batchku/MO/openframeworks/MOD/bin/data/img_mask_720b.png

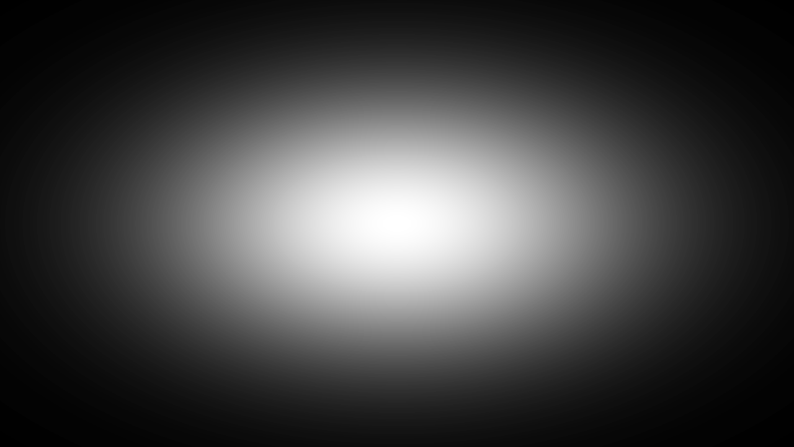
openframeworks/MOD/bin/data/img_mask_720b.png
