batchku/MO/openframeworks/MOD/bin/data/img_mask_720c.png

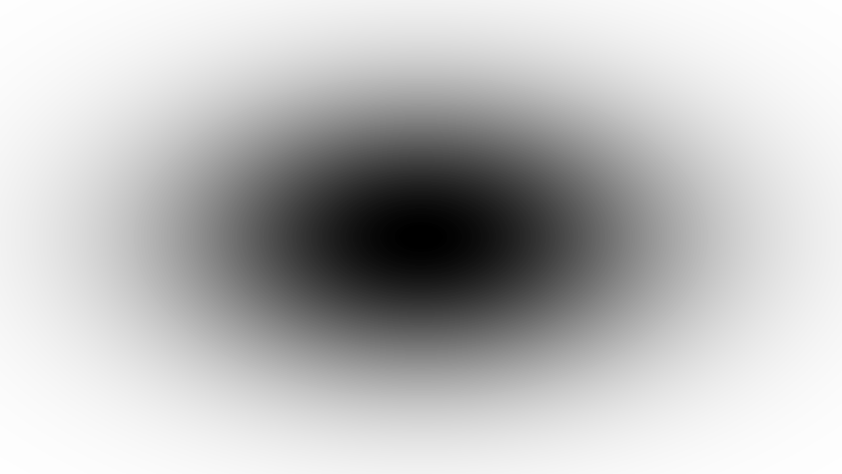
openframeworks/MOD/bin/data/img_mask_720c.png
