batchku/MO/CAD/MOD/_MOD-vr_rhino-exports/MOD-v1_MOD-lightbox-mids.dxf

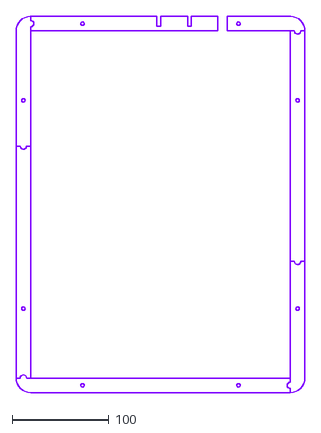
[picture p23: CAD file, 2017-08-02]
CAD/MOD/_MOD-vr_rhino-exports/MOD-v1_MOD-lightbox-mids.dxf
299.0 x 389.5
