batchku/MO/CAD/MOD/MOD-Button-Cap-Cap_v9-A.stl

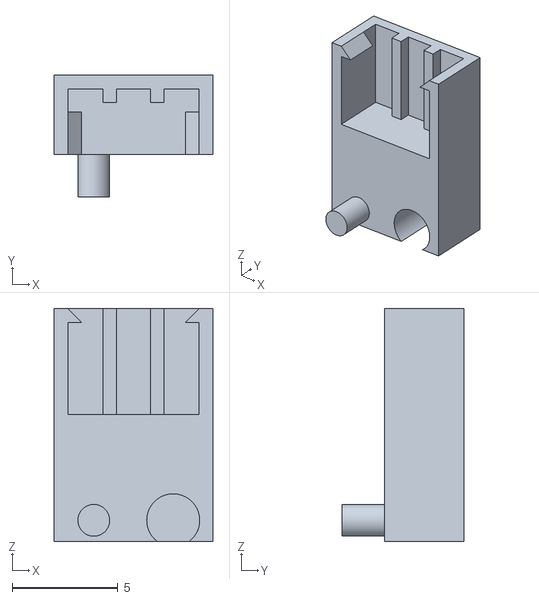
[picture p24: CAD file, 2017-09-18]
CAD/MOD/MOD-Button-Cap-Cap_v9-A.stl
7.50 x 5.75 x 11.0
