batchku/MO/CAD/MOM/_exports/MOMv2_bottom-plate.dxf

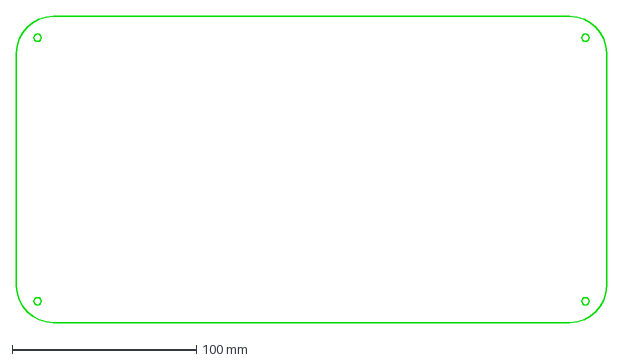
[picture p25: CAD file, 2017-09-16]
CAD/MOM/_exports/MOMv2_bottom-plate.dxf
320.0 x 166.0 mm
