batchku/MO/PCBs/MO/MO-v2-6b.dxf

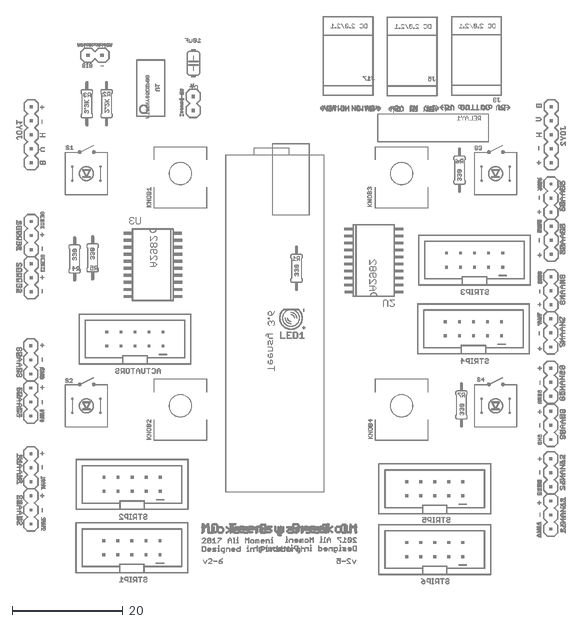
[picture p26: CAD file, 2017-12-16]
PCBs/MO/MO-v2-6b.dxf
99.4 x 102.7
