batchku/MO/PCBs/MOD/MOD-v2-1_MOD-Strips.dxf

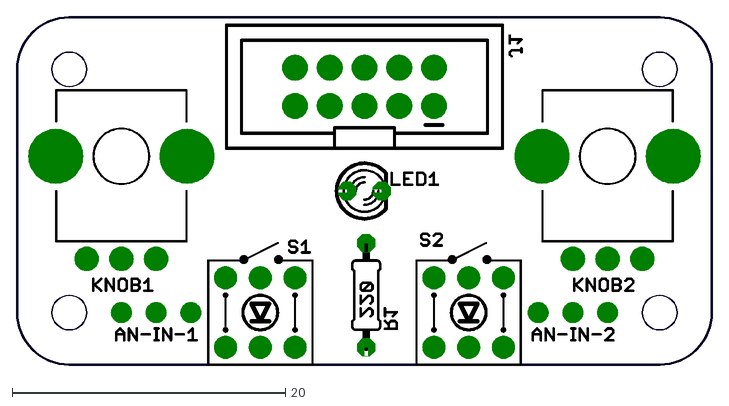
[picture p27: CAD file, 2017-07-28]
PCBs/MOD/MOD-v2-1_MOD-Strips.dxf
51.0 x 25.6
