batchku/MO/CAD/_exports/Clamp-male-4.stl

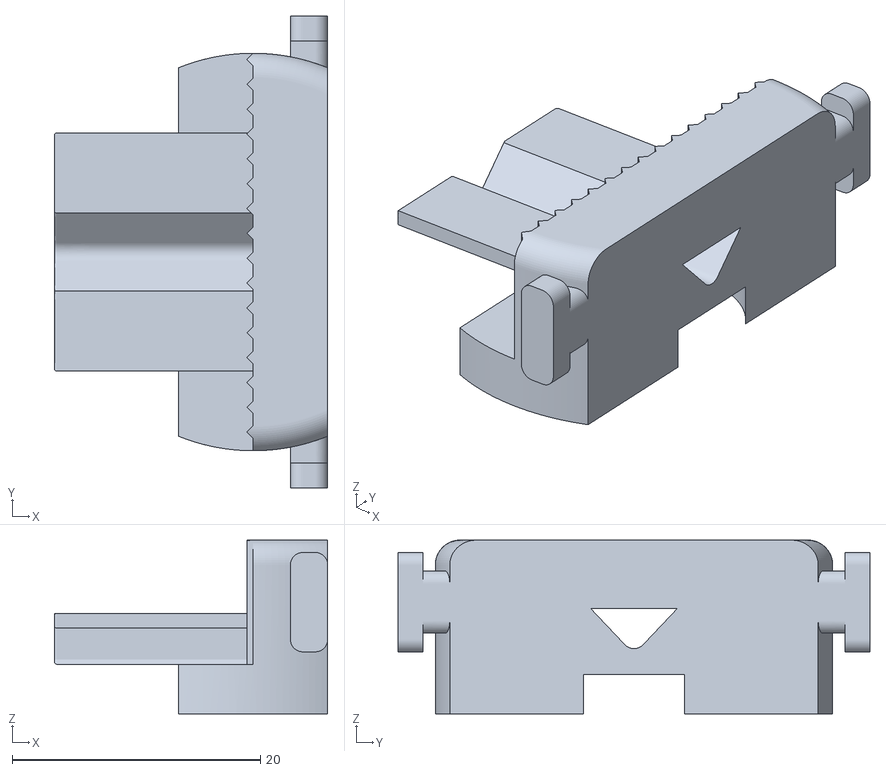
[picture p28: CAD file, 2017-12-22]
CAD/_exports/Clamp-male-4.stl
22.0 x 38.0 x 14.0
