batchku/MO/CAD/MOD/_MOD-vr_rhino-exports/MOD-v1_MOD-lightbox-neck.dxf

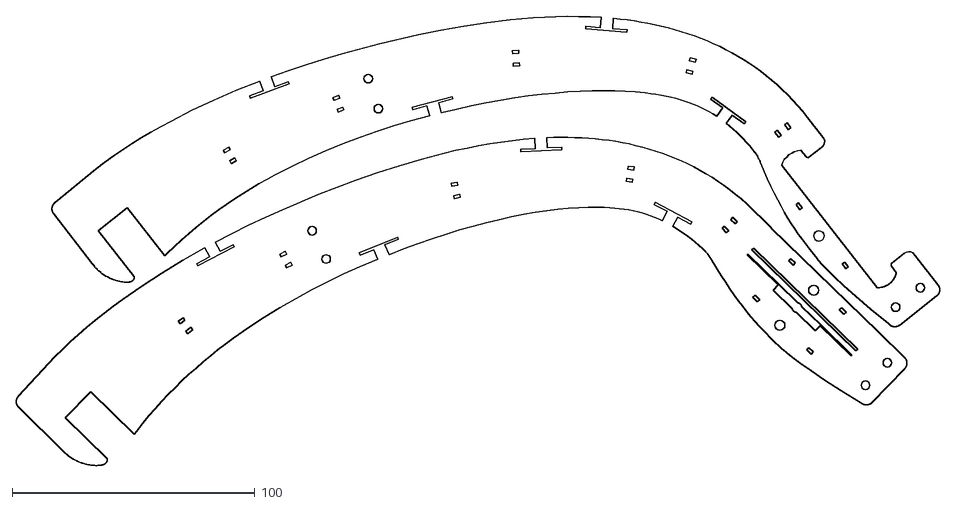
[picture p29: CAD file, 2017-08-02]
CAD/MOD/_MOD-vr_rhino-exports/MOD-v1_MOD-lightbox-neck.dxf
380.2 x 184.8
