batchku/MO/CAD/MOM/_exports/MOMv2_top-plate.dxf

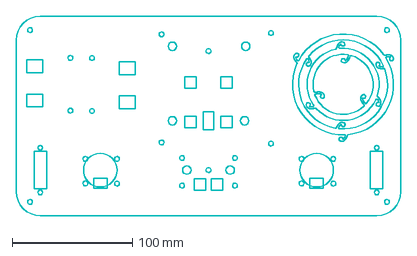
[picture p30: CAD file, 2017-09-16]
CAD/MOM/_exports/MOMv2_top-plate.dxf
320.0 x 166.0 mm
