batchku/MO/PCBs/MO/MO-v2-6.dxf

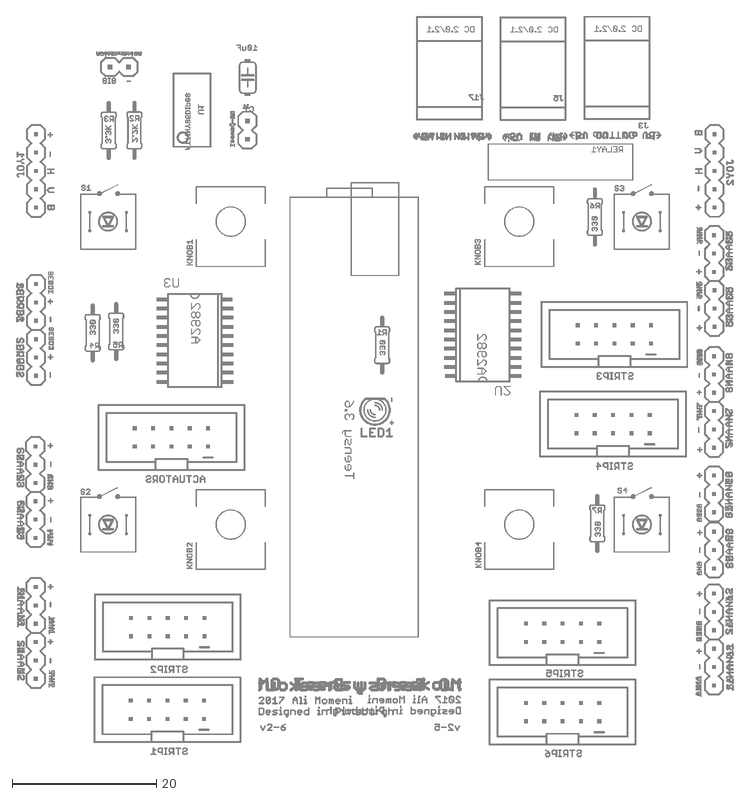
[picture p31: CAD file, 2017-12-16]
PCBs/MO/MO-v2-6.dxf
99.4 x 102.7
