batchku/MO/PCBs/MOD/MOD-v2-1.dxf

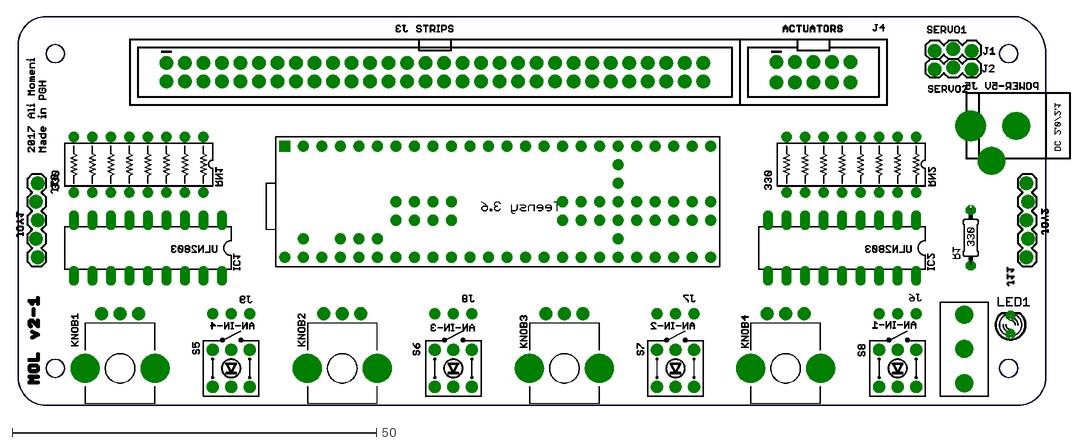
[picture p32: CAD file, 2017-07-28]
PCBs/MOD/MOD-v2-1.dxf
144.6 x 53.5
