batchku/MO/CAD/MOD/MOD-Button-Cap-Cap_v7.stl

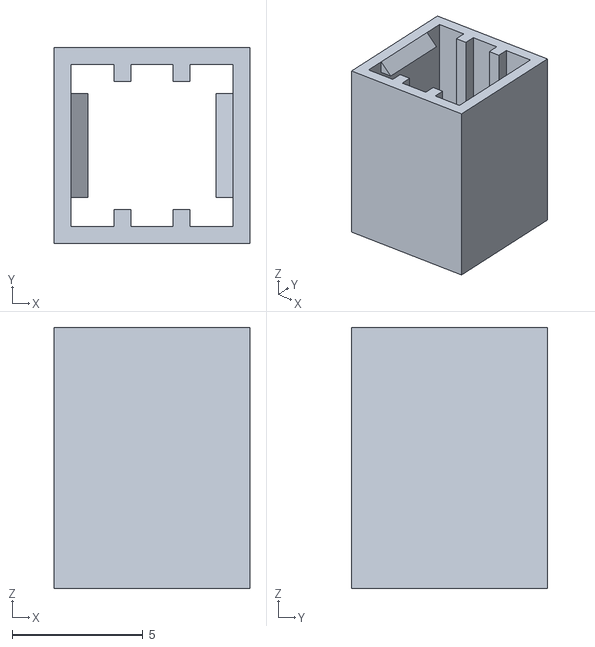
[picture p35: CAD file, 2017-09-17]
CAD/MOD/MOD-Button-Cap-Cap_v7.stl
7.50 x 7.50 x 10.0
