batchku/MO/PCBs/MO/MO-v2-6c.dxf

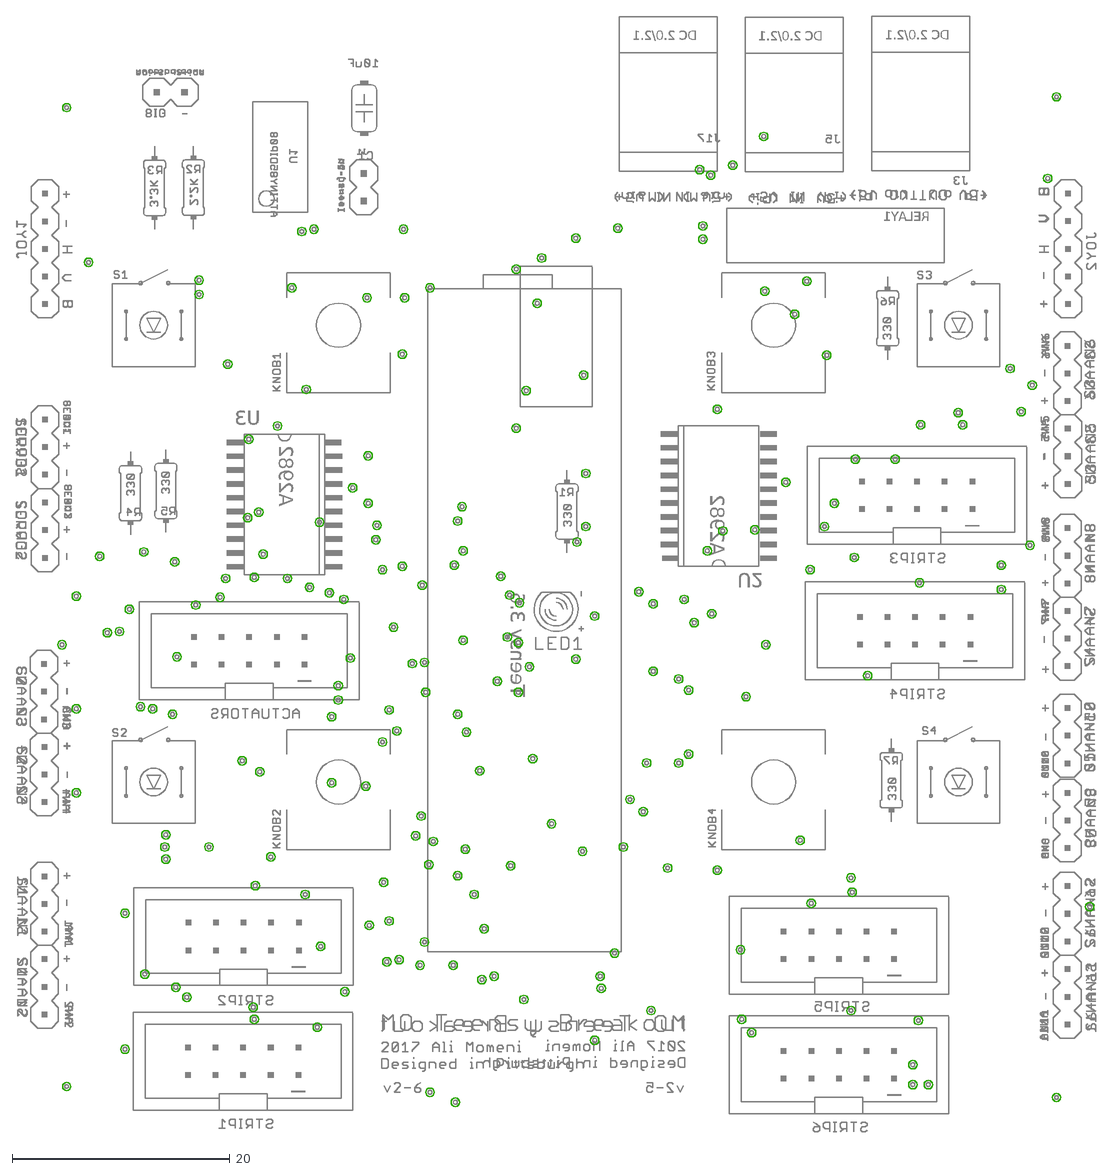
[picture p36: CAD file, 2017-12-16]
PCBs/MO/MO-v2-6c.dxf
DC 2.0/2.1
RELAY1
Teensy 3.6
U2
A2982
U3
