batchku/MO/PCBs/MOD/Joystick.dxf

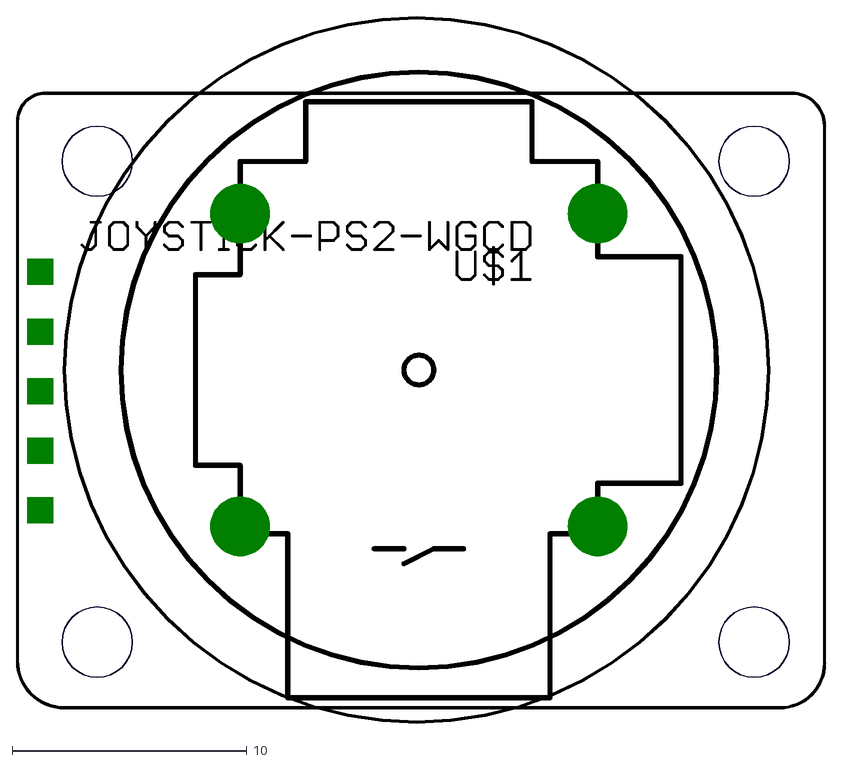
[picture p37: CAD file, 2017-07-28]
PCBs/MOD/Joystick.dxf
34.5 x 30.1
