batchku/MO/CAD/_exports/magnet-test-3.dxf

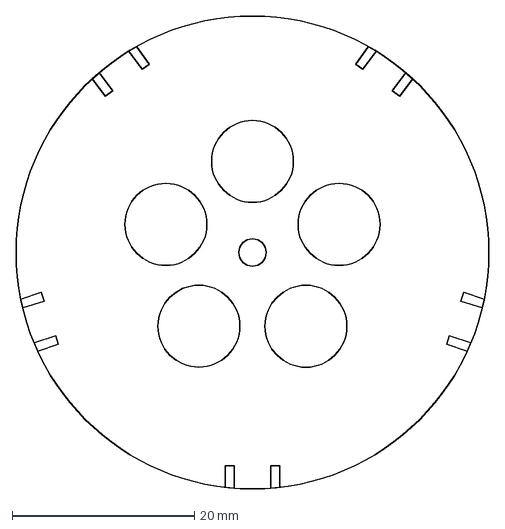
[picture p38: CAD file, 2017-12-21]
CAD/_exports/magnet-test-3.dxf
51.9 x 51.9 mm
