batchku/MO/CAD/MOD/MOD-Button-Cap-Frame_v6.stl

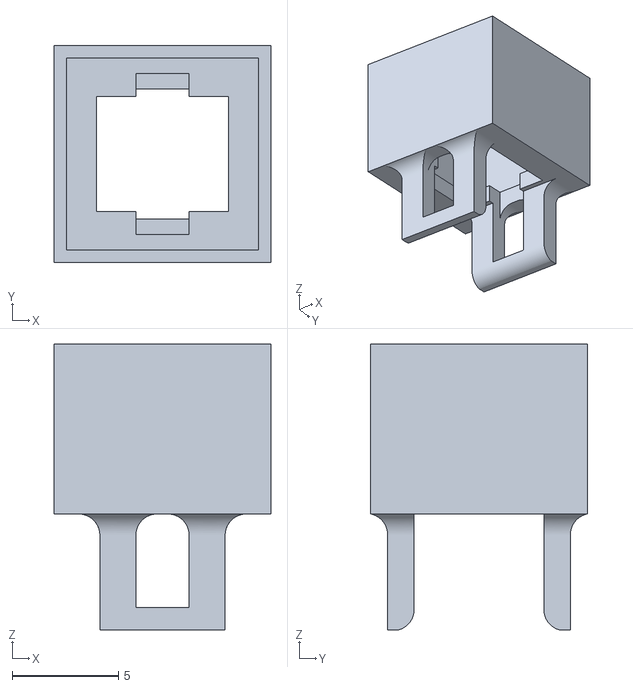
[picture p39: CAD file, 2017-09-17]
CAD/MOD/MOD-Button-Cap-Frame_v6.stl
10.2 x 10.2 x 13.5
