batchku/MO/PCBs/MO/MO-v2-1_MOD-Actuators.dxf

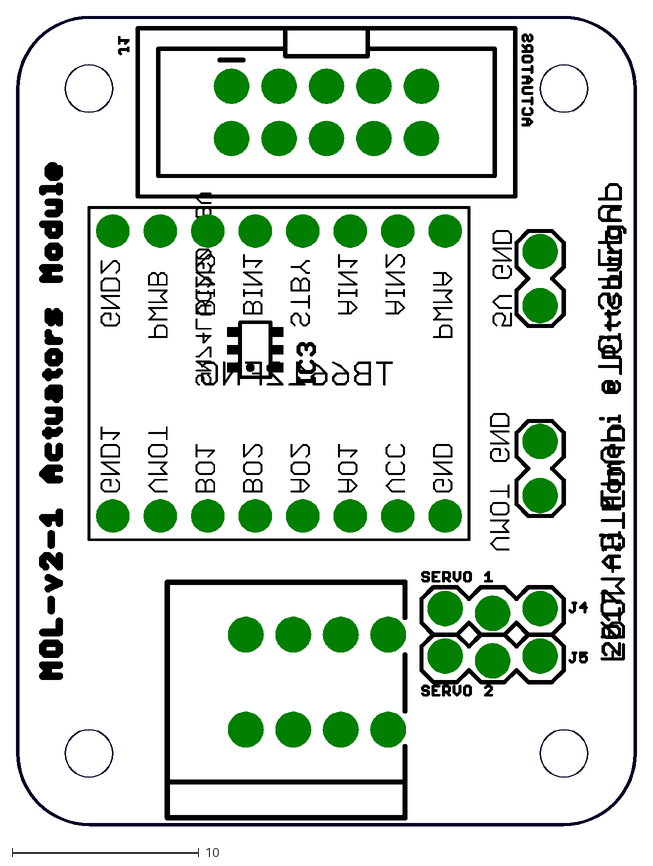
[picture p40: CAD file, 2017-07-28]
PCBs/MO/MO-v2-1_MOD-Actuators.dxf
33.2 x 43.3
