batchku/MO/PCBs/MOD/MOD-v1.dxf

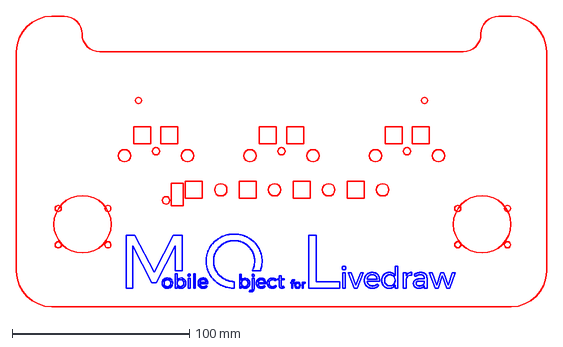
[picture p41: CAD file, 2017-07-28]
PCBs/MOD/MOD-v1.dxf
299.0 x 163.8 mm
