batchku/MO/CAD/_exports/MOMv5_tickler-pad.dxf

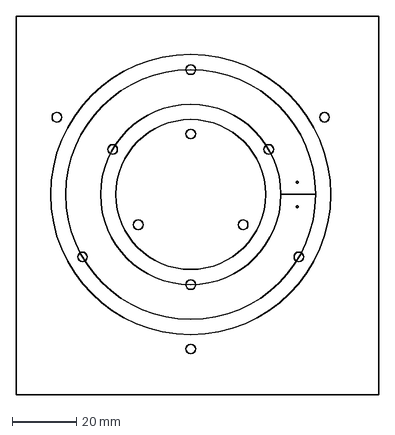
[picture p44: CAD file, 2017-12-21]
CAD/_exports/MOMv5_tickler-pad.dxf
112.6 x 117.7 mm
