batchku/MO/CAD/MOD/Button-profile.dxf

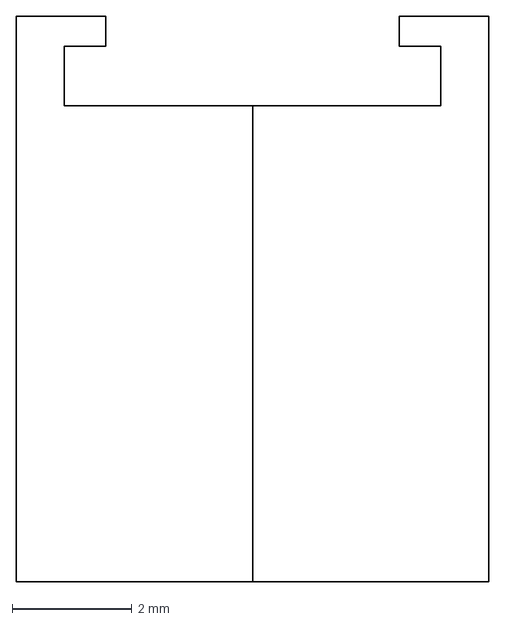
[picture p46: CAD file, 2017-08-03]
CAD/MOD/Button-profile.dxf
7.90 x 9.46 mm
