batchku/MO/CAD/_exports/clamp-metal-holder-4.stl

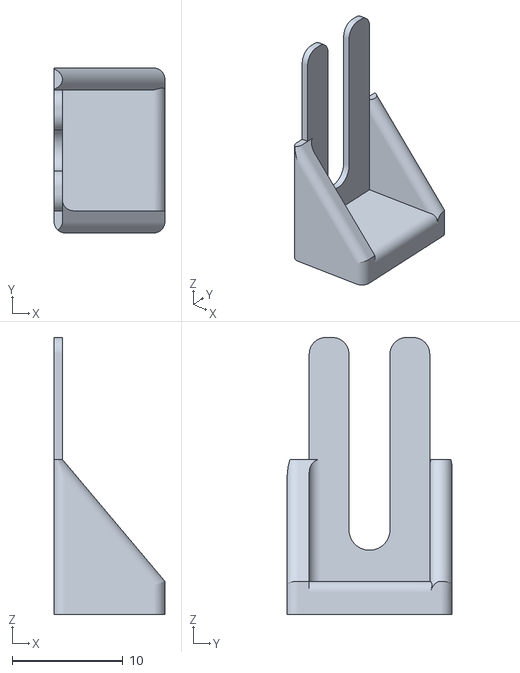
[picture p47: CAD file, 2017-12-21]
CAD/_exports/clamp-metal-holder-4.stl
10.0 x 14.9 x 25.0
