batchku/MO/CAD/MOD/MOD-Button-Cap-Cap-1.stl

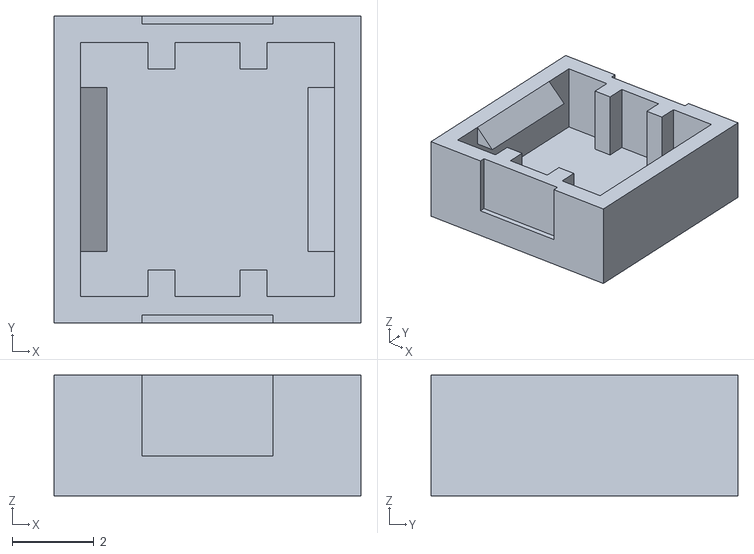
[picture p48: CAD file, 2017-08-03]
CAD/MOD/MOD-Button-Cap-Cap-1.stl
7.50 x 7.50 x 2.95
