batchku/MO/CAD/_exports/MOMv5-6_base.dxf

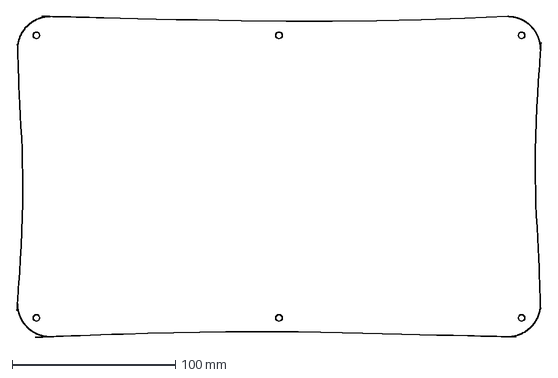
[picture p49: CAD file, 2017-12-21]
CAD/_exports/MOMv5-6_base.dxf
321.5 x 196.9 mm
