batchku/MO/CAD/MOD/MOD-Button-Frame-1.stl

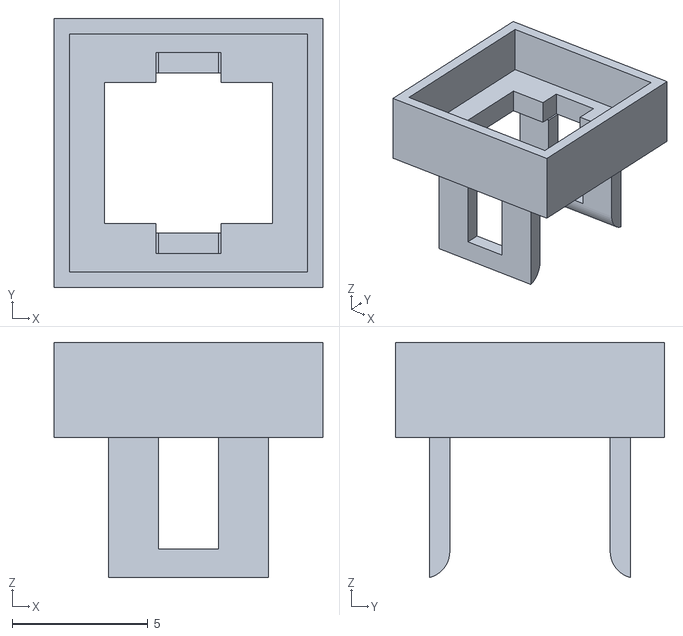
[picture p50: CAD file, 2017-08-03]
CAD/MOD/MOD-Button-Frame-1.stl
9.90 x 9.90 x 8.66
