batchku/MO/CAD/_exports/button-simple.stl

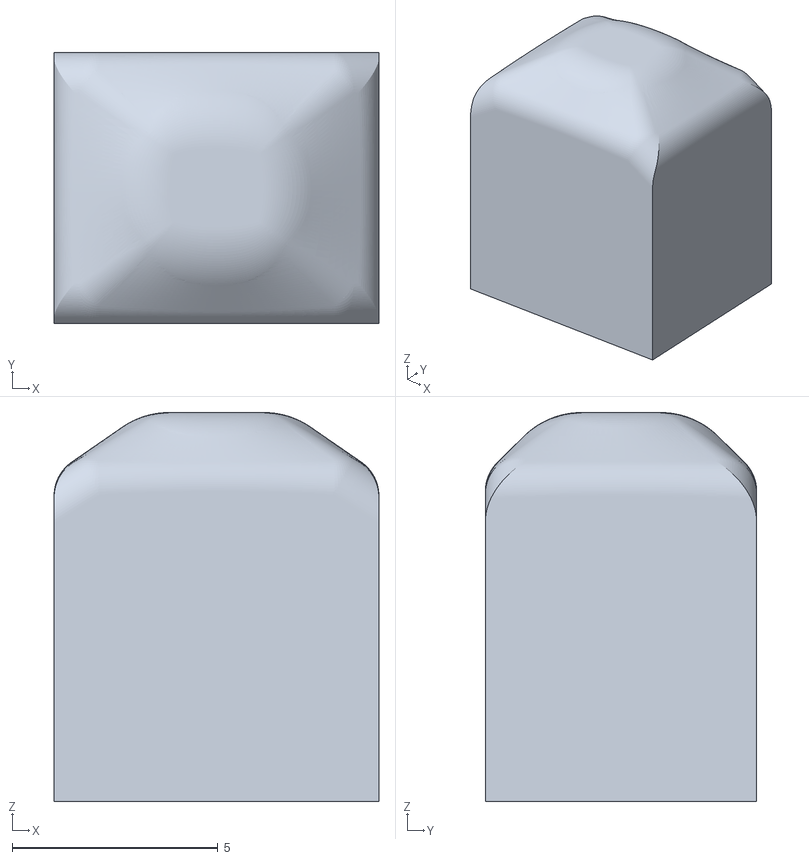
[picture p51: CAD file, 2017-12-21]
CAD/_exports/button-simple.stl
7.90 x 6.60 x 9.46
