batchku/MO/CAD/_exports/button-simple-5.stl

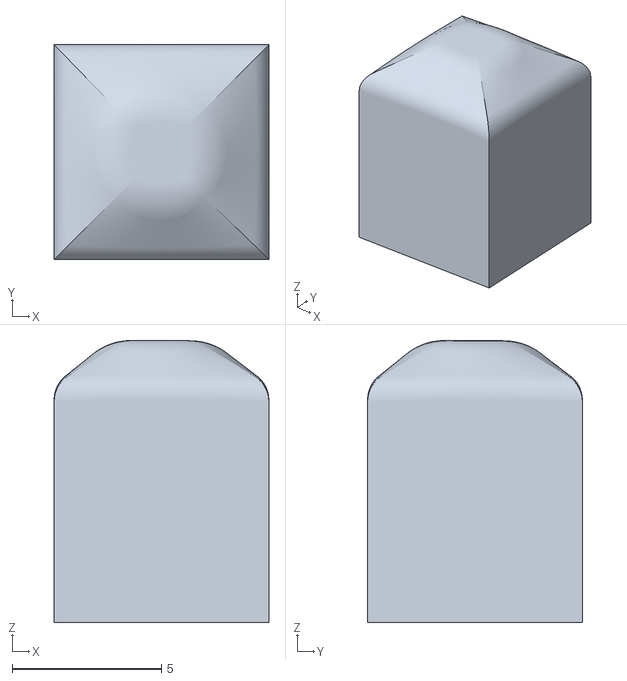
[picture p53: CAD file, 2017-12-21]
CAD/_exports/button-simple-5.stl
7.20 x 7.20 x 9.46
