batchku/MO/CAD/MOD/MOD-v2.0-all-b.dxf

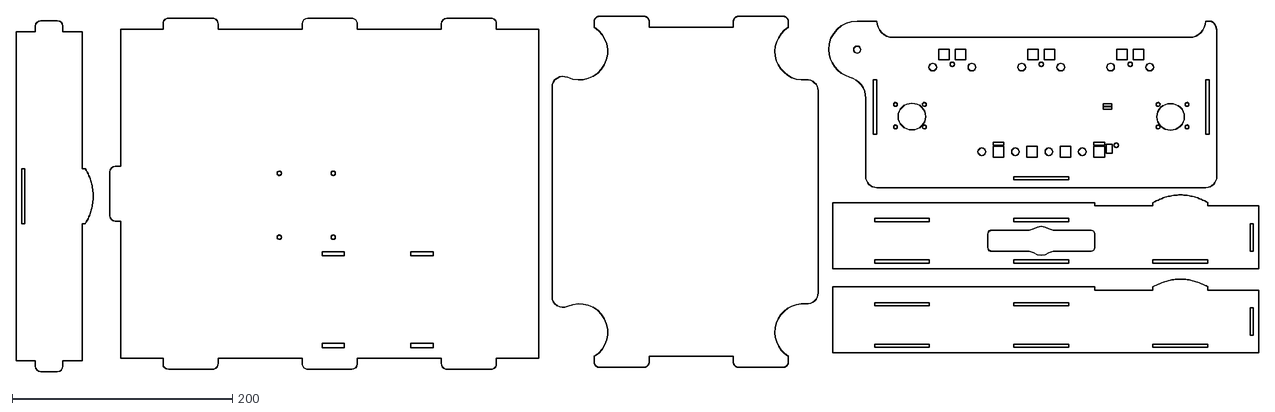
[picture p54: CAD file, 2017-08-02]
CAD/MOD/MOD-v2.0-all-b.dxf
1129.0 x 322.9
