batchku/MO/CAD/MOD/MOD-v2.0-all-UI-panel-a.dxf

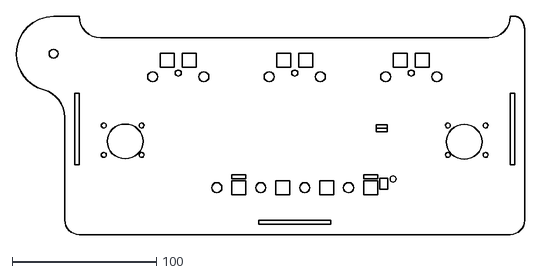
[picture p56: CAD file, 2017-08-02]
CAD/MOD/MOD-v2.0-all-UI-panel-a.dxf
352.6 x 151.3
