batchku/MO/CAD/_exports/button-simple-4.stl

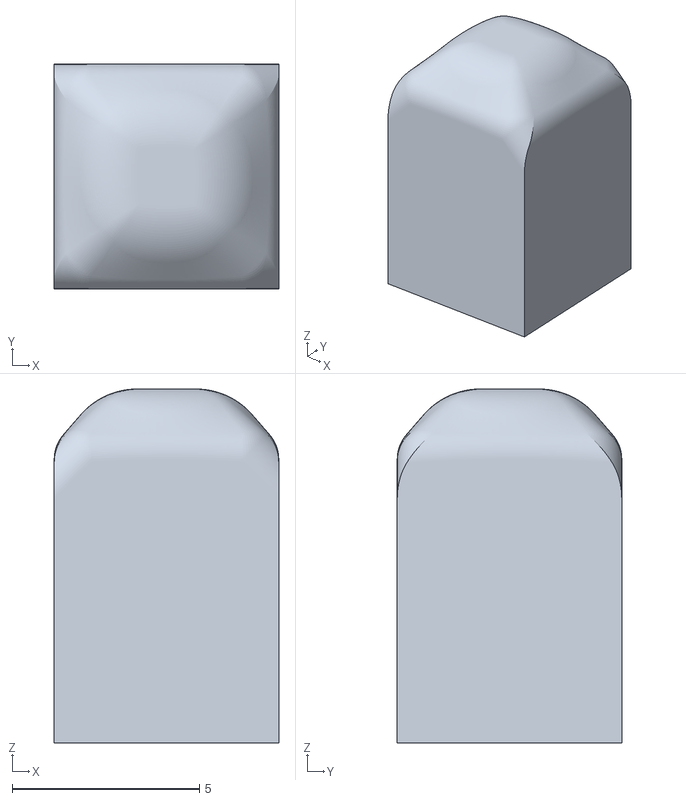
[picture p57: CAD file, 2017-12-21]
CAD/_exports/button-simple-4.stl
6.00 x 6.00 x 9.46
