batchku/MO/CAD/MOD/MOD-v2.0-all-UI-panel-b.dxf

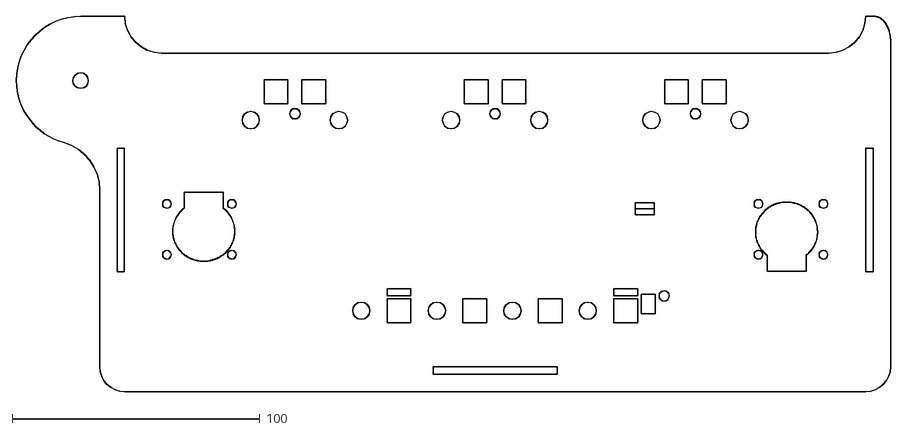
[picture p58: CAD file, 2017-08-02]
CAD/MOD/MOD-v2.0-all-UI-panel-b.dxf
352.6 x 151.3
