batchku/MO/CAD/_exports/Clamp-female-2.stl

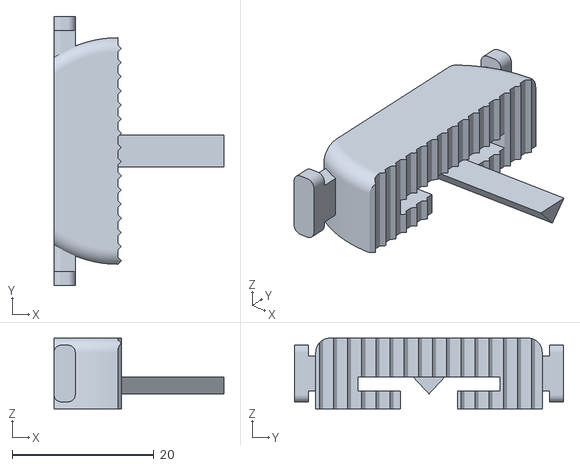
[picture p59: CAD file, 2017-12-21]
CAD/_exports/Clamp-female-2.stl
24.0 x 38.0 x 10.0
