batchku/MO/CAD/MOD/MOD-v2.0-all-h.dxf

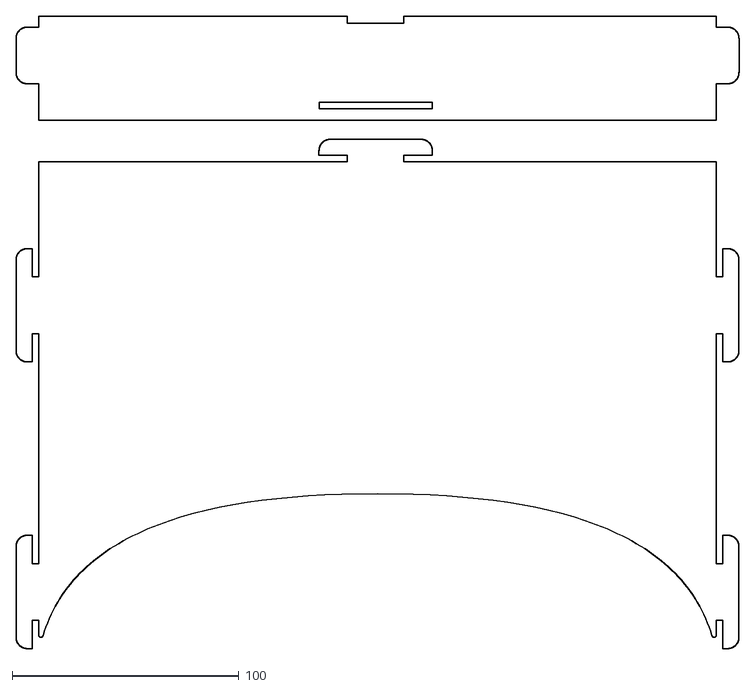
[picture p60: CAD file, 2017-08-02]
CAD/MOD/MOD-v2.0-all-h.dxf
319.0 x 278.9
