batchku/MO/CAD/MOD/MOD-v2.0-all-UI-wall-e.dxf

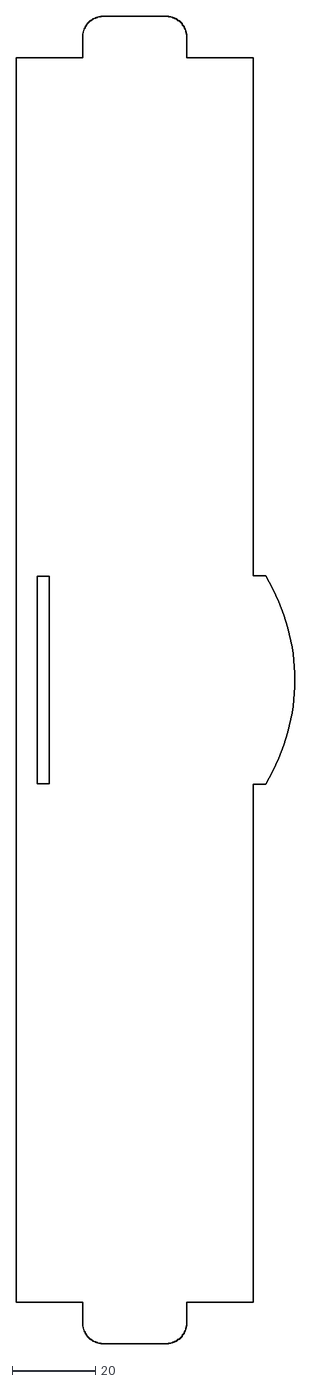
[picture p61: CAD file, 2017-08-02]
CAD/MOD/MOD-v2.0-all-UI-wall-e.dxf
67.0 x 319.0
