batchku/MO/CAD/_exports/Clamp-part2_2.stl

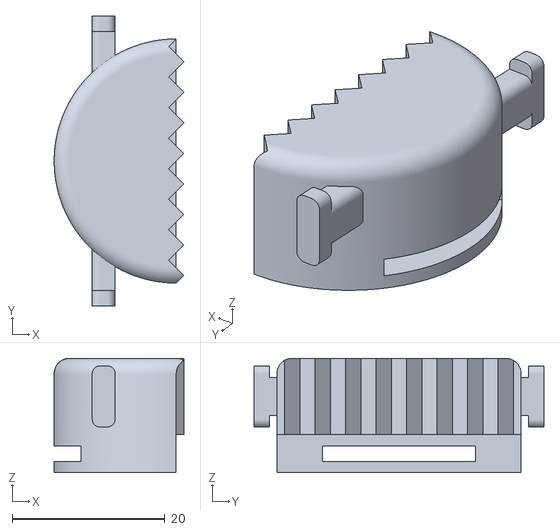
[picture p62: CAD file, 2017-12-21]
CAD/_exports/Clamp-part2_2.stl
17.0 x 38.0 x 15.0
