batchku/MO/CAD/MOD/MOD-v2.0-all-UI-wall-f.dxf

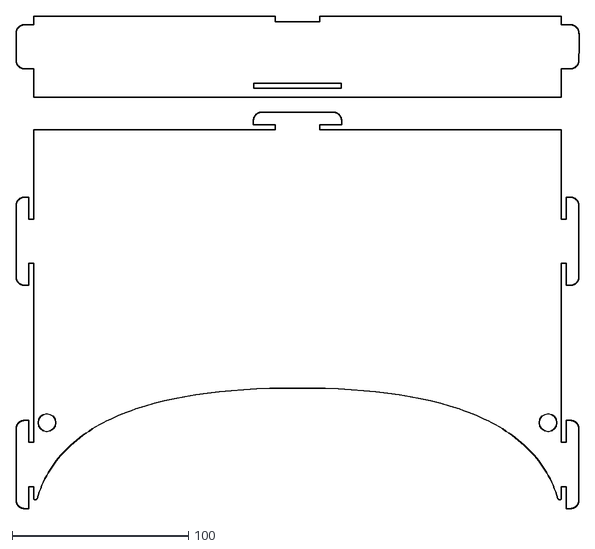
[picture p63: CAD file, 2017-08-02]
CAD/MOD/MOD-v2.0-all-UI-wall-f.dxf
319.0 x 278.9
