batchku/MO/CAD/_exports/clamp-part1_1.stl

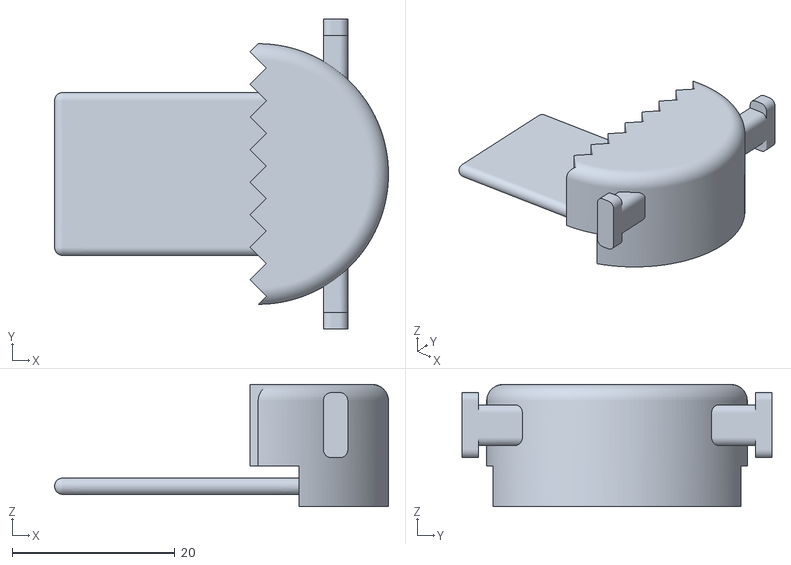
[picture p64: CAD file, 2017-12-21]
CAD/_exports/clamp-part1_1.stl
41.0 x 38.0 x 15.0
