batchku/MO/CAD/MOD/MOD-v2.0-all.dxf

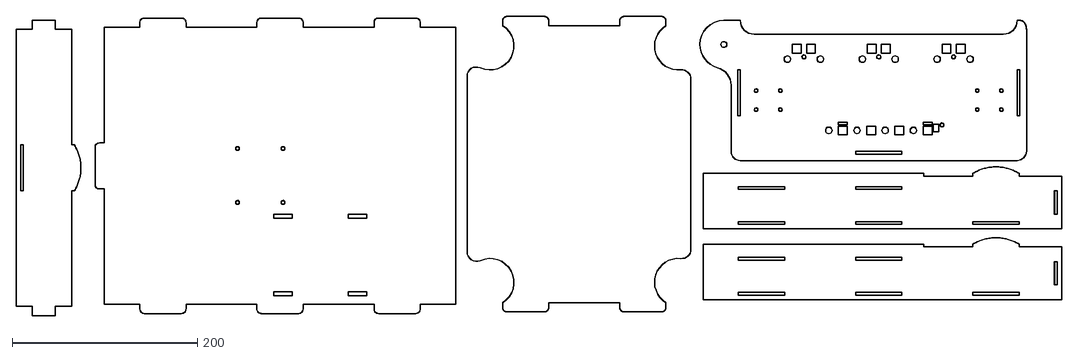
[picture p65: CAD file, 2017-08-02]
CAD/MOD/MOD-v2.0-all.dxf
1129.0 x 322.9
