batchku/MO/CAD/_exports/magnet-test-1.dxf

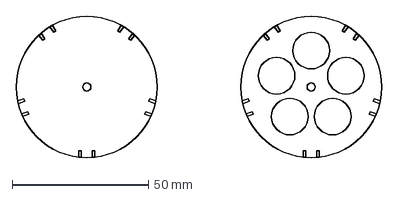
[picture p66: CAD file, 2017-12-21]
CAD/_exports/magnet-test-1.dxf
134.4 x 51.9 mm
