batchku/MO/CAD/MOD/MOD-v2.0-all-UI-some-d.dxf

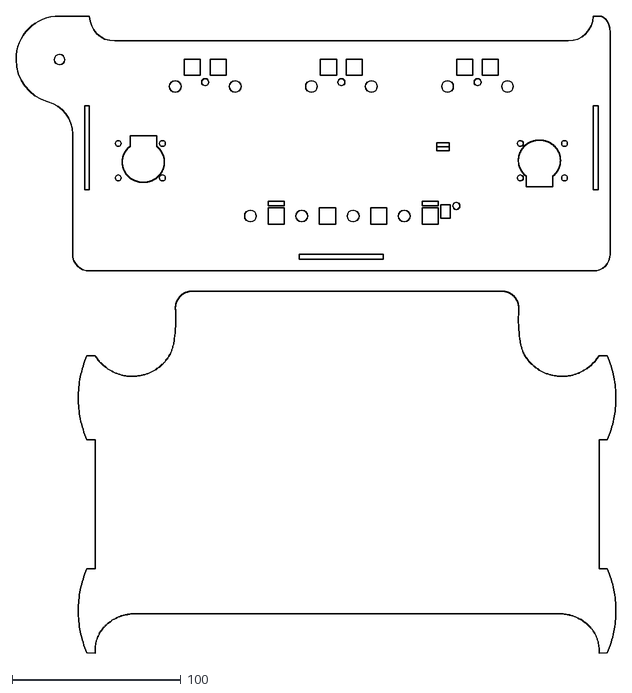
[picture p67: CAD file, 2017-08-02]
CAD/MOD/MOD-v2.0-all-UI-some-d.dxf
356.1 x 378.0
