batchku/MO/CAD/_exports/MOMv5-5.dxf

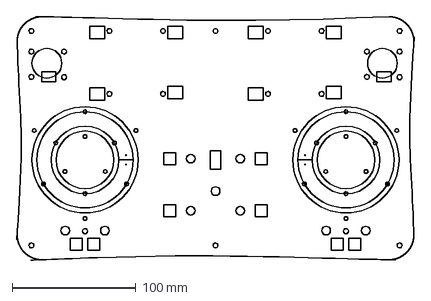
[picture p68: CAD file, 2017-12-21]
CAD/_exports/MOMv5-5.dxf
321.5 x 196.9 mm
