batchku/MO/CAD/MOD/MOD-v2.0-all-i2.dxf

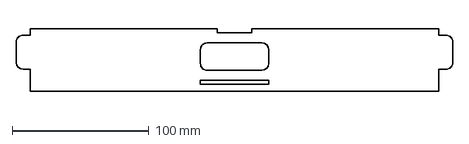
[picture p69: CAD file, 2017-08-02]
CAD/MOD/MOD-v2.0-all-i2.dxf
319.0 x 45.7 mm
