batchku/MO/CAD/_exports/Clamp-part2.stl

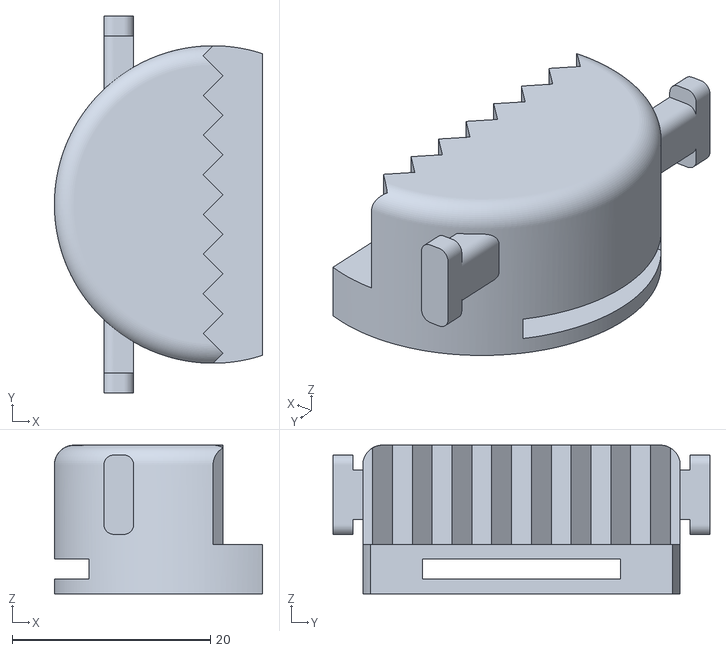
[picture p70: CAD file, 2017-12-21]
CAD/_exports/Clamp-part2.stl
21.0 x 38.0 x 15.0
