batchku/MO/CAD/MOD/MOD-v2.0-all-i.dxf

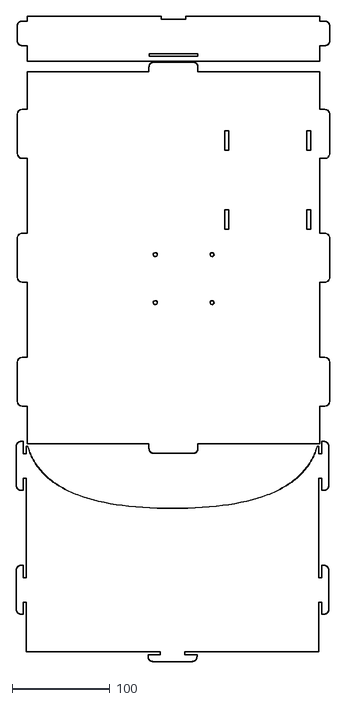
[picture p71: CAD file, 2017-08-02]
CAD/MOD/MOD-v2.0-all-i.dxf
320.0 x 658.5
