batchku/MO/CAD/_exports/button-simple-2.stl

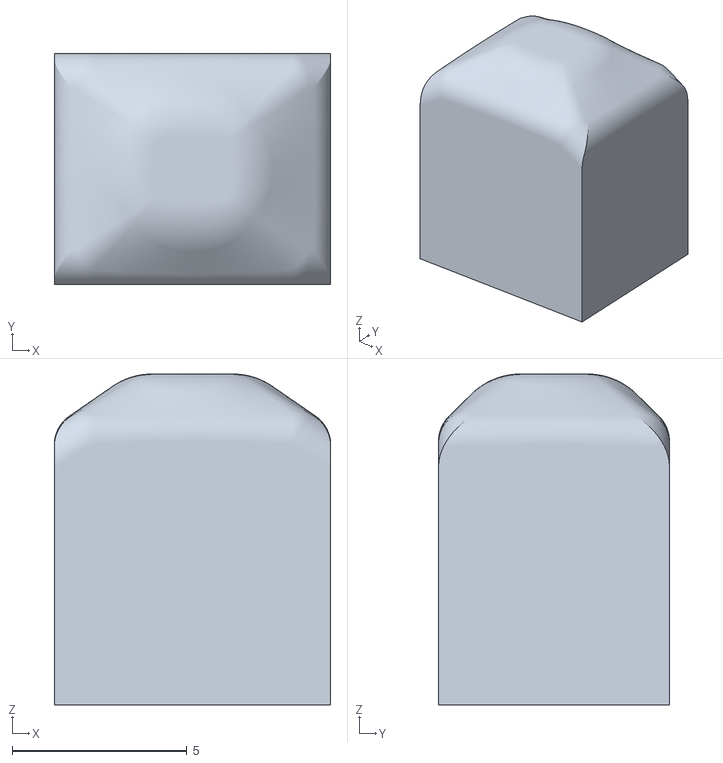
[picture p72: CAD file, 2017-12-21]
CAD/_exports/button-simple-2.stl
7.90 x 6.60 x 9.46
