batchku/MO/CAD/MOD/MOD-v2.0-all-g.dxf

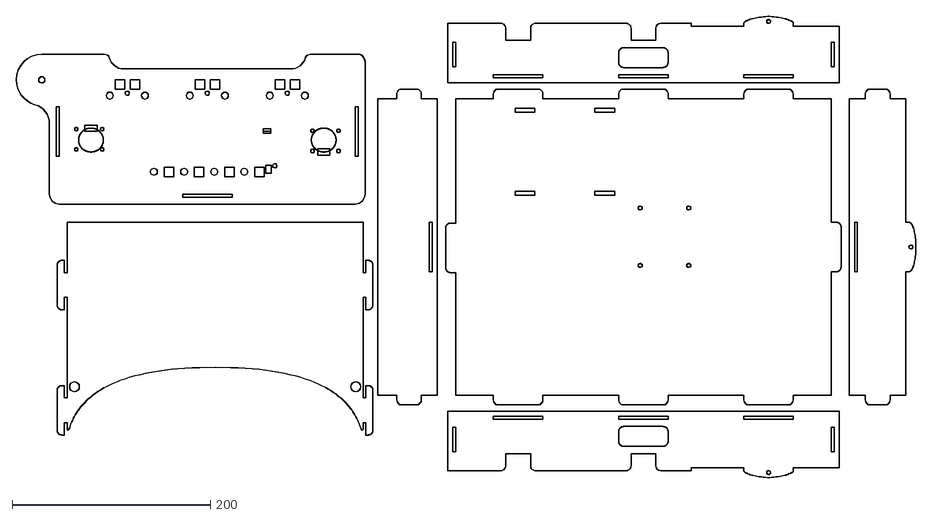
[picture p73: CAD file, 2017-08-02]
CAD/MOD/MOD-v2.0-all-g.dxf
908.7 x 465.9
