batchku/MO/CAD/_exports/magnet-test-4.dxf

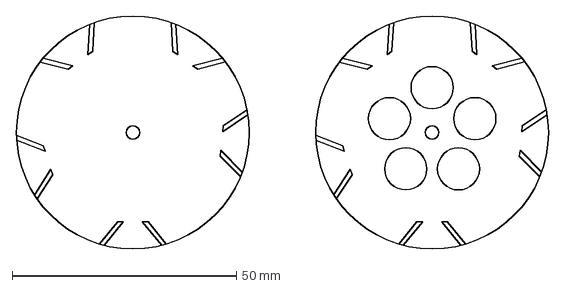
[picture p74: CAD file, 2017-12-21]
CAD/_exports/magnet-test-4.dxf
118.6 x 51.9 mm
