batchku/MO/CAD/MOD/MOD-v1.1.dxf

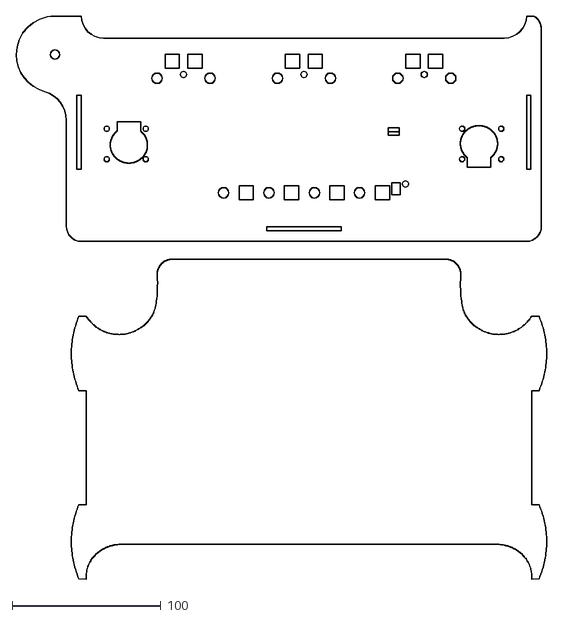
[picture p75: CAD file, 2017-08-02]
CAD/MOD/MOD-v1.1.dxf
356.1 x 378.0
