batchku/MO/CAD/_exports/Clamp-male-2.stl

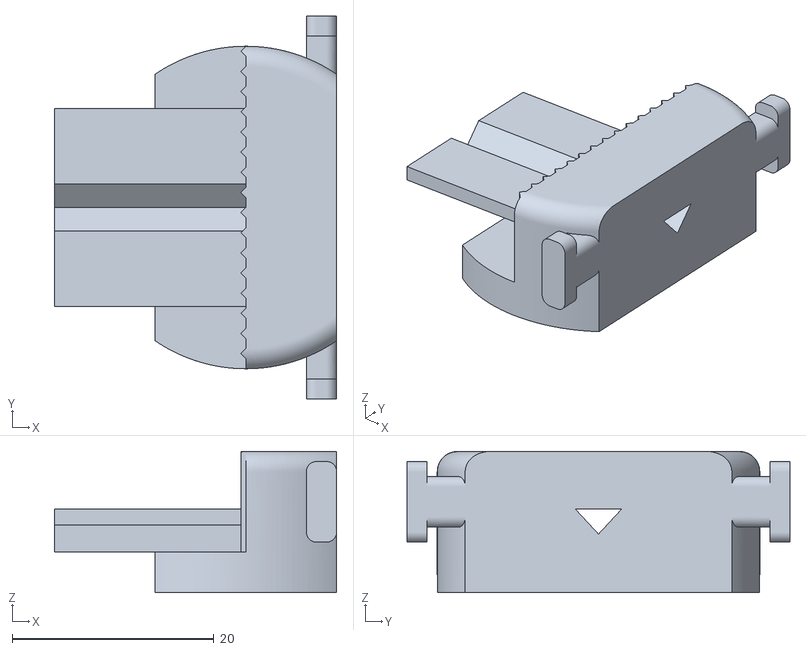
[picture p76: CAD file, 2017-12-21]
CAD/_exports/Clamp-male-2.stl
28.0 x 38.0 x 14.0
