batchku/MO/CAD/MOD/MOD-holder_all-v3-4.dxf

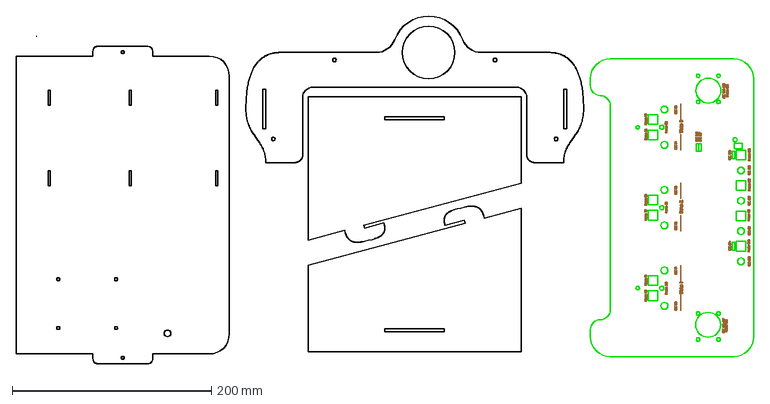
[picture p77: CAD file, 2017-07-31]
CAD/MOD/MOD-holder_all-v3-4.dxf
740.2 x 349.1 mm
