batchku/MO/CAD/_exports/clamp-metal-holder.stl

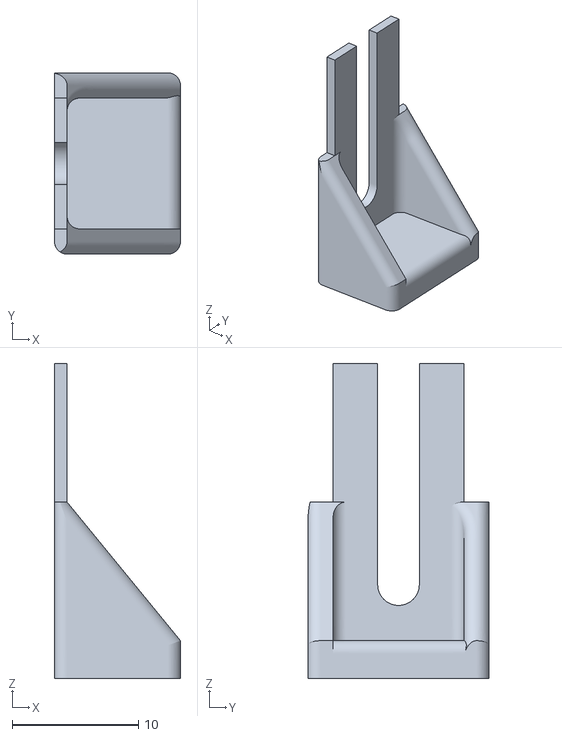
[picture p78: CAD file, 2017-12-21]
CAD/_exports/clamp-metal-holder.stl
10.0 x 14.4 x 25.0
