batchku/MO/CAD/MOD/MOD-v1_knob-cap17.stl

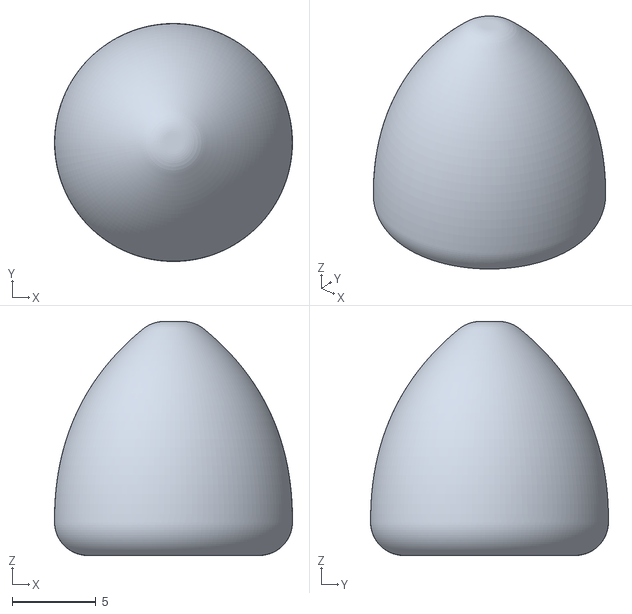
[picture p79: CAD file, 2017-07-31]
CAD/MOD/MOD-v1_knob-cap17.stl
14.2 x 14.2 x 14.0
