batchku/MO/CAD/_exports/magnet-test-5.dxf

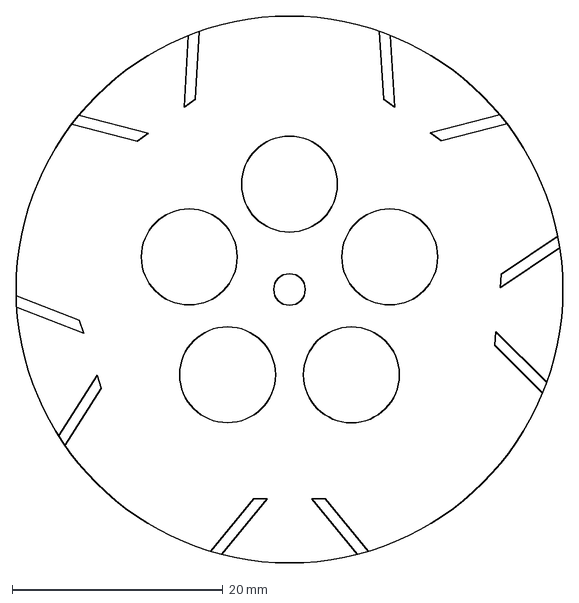
[picture p80: CAD file, 2017-12-21]
CAD/_exports/magnet-test-5.dxf
51.9 x 51.9 mm
