batchku/MO/CAD/MOD/MOM-holder-ali_v3-2d.dxf

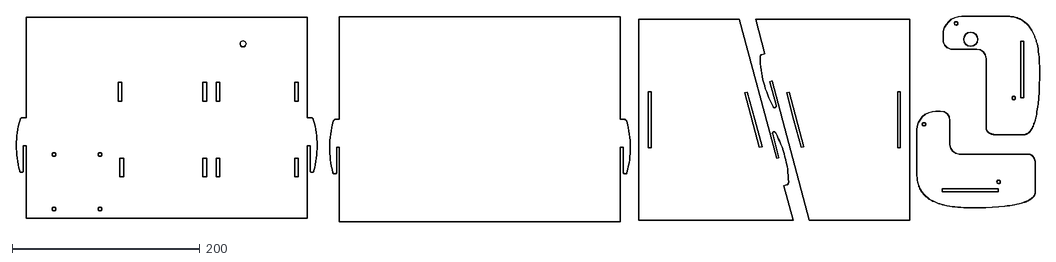
[picture p81: CAD file, 2017-07-31]
CAD/MOD/MOM-holder-ali_v3-2d.dxf
1088.8 x 218.6
