batchku/MO/CAD/_exports/Clamp-part1_2.stl

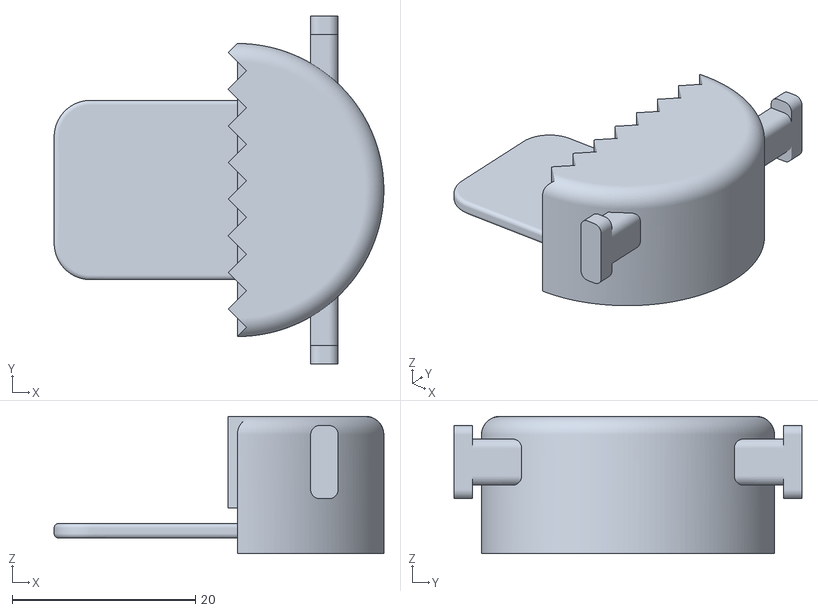
[picture p82: CAD file, 2017-12-21]
CAD/_exports/Clamp-part1_2.stl
36.0 x 38.0 x 15.0
