batchku/MO/CAD/MOD/MOD-v1_knob-cap7.stl

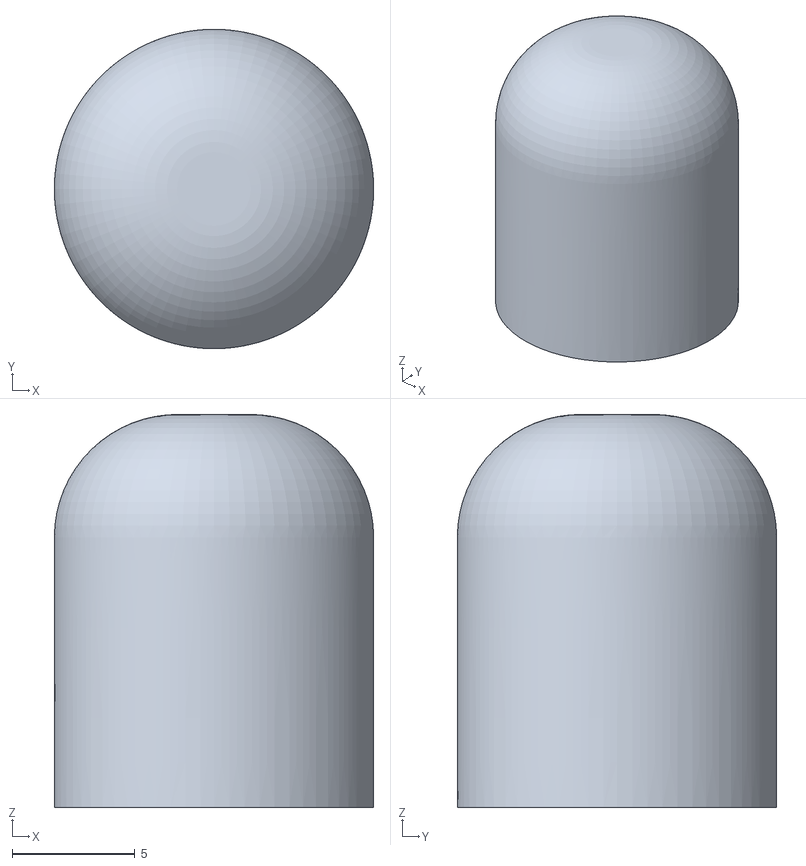
[picture p83: CAD file, 2017-07-31]
CAD/MOD/MOD-v1_knob-cap7.stl
13.0 x 13.0 x 16.0
