batchku/MO/CAD/MOD/MOD-v1_knob-cap19.stl

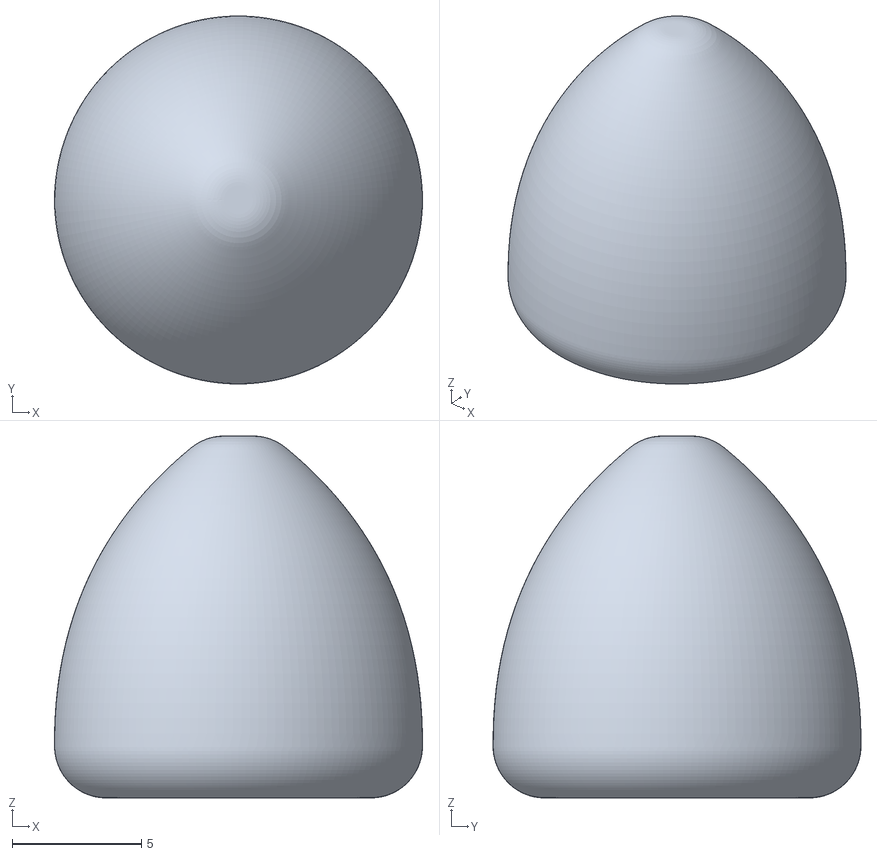
[picture p85: CAD file, 2017-07-31]
CAD/MOD/MOD-v1_knob-cap19.stl
14.2 x 14.2 x 14.0
