batchku/MO/CAD/MOD/MOM-holder-top_v3-2b.dxf

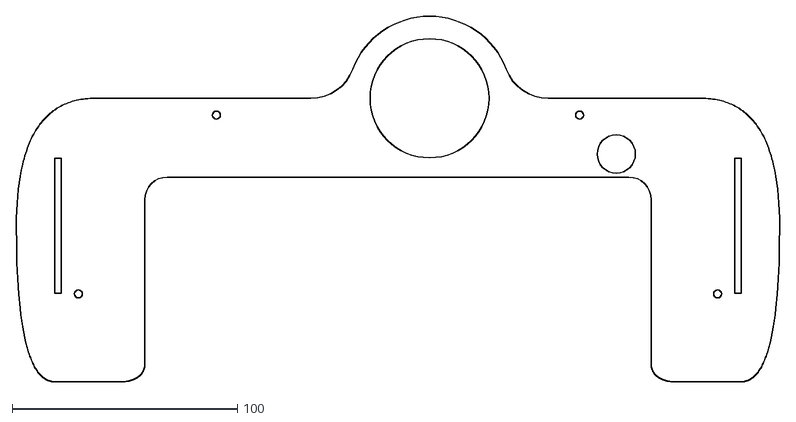
[picture p86: CAD file, 2017-07-31]
CAD/MOD/MOM-holder-top_v3-2b.dxf
339.1 x 162.4
