batchku/MO/CAD/_exports/magnet-test-6.dxf

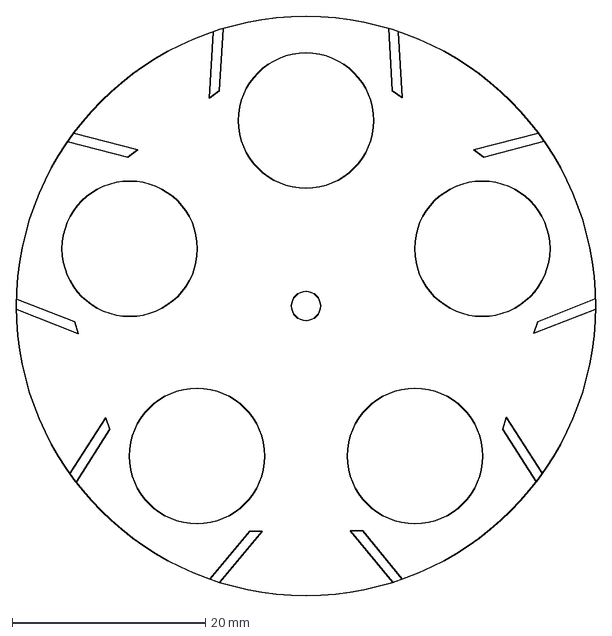
[picture p87: CAD file, 2017-12-21]
CAD/_exports/magnet-test-6.dxf
59.9 x 59.9 mm
