batchku/MO/CAD/MOD/MOM-holder-top_v3-2-RevB.dxf

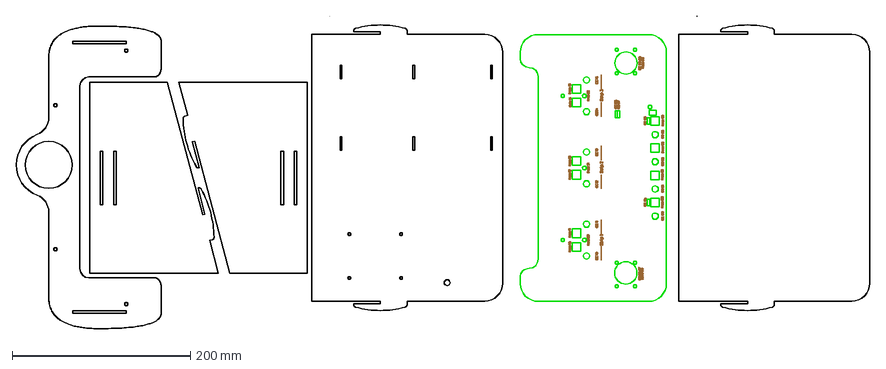
[picture p88: CAD file, 2017-07-31]
CAD/MOD/MOM-holder-top_v3-2-RevB.dxf
956.4 x 349.9 mm
