batchku/MO/CAD/_exports/magnet-test-2.dxf

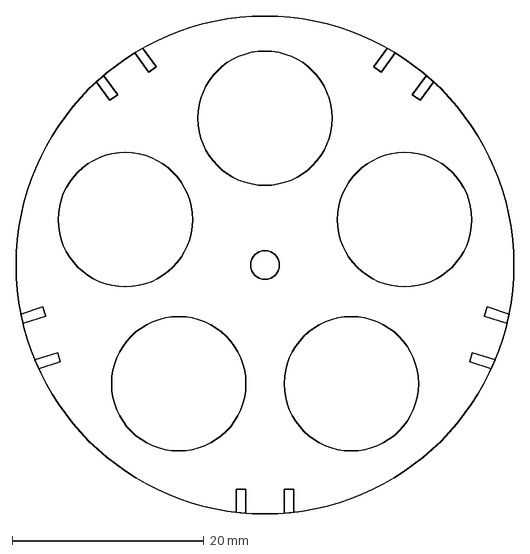
[picture p89: CAD file, 2017-12-21]
CAD/_exports/magnet-test-2.dxf
51.9 x 51.9 mm
