batchku/MO/CAD/MOD/MOD-v1_knob-cap20.stl

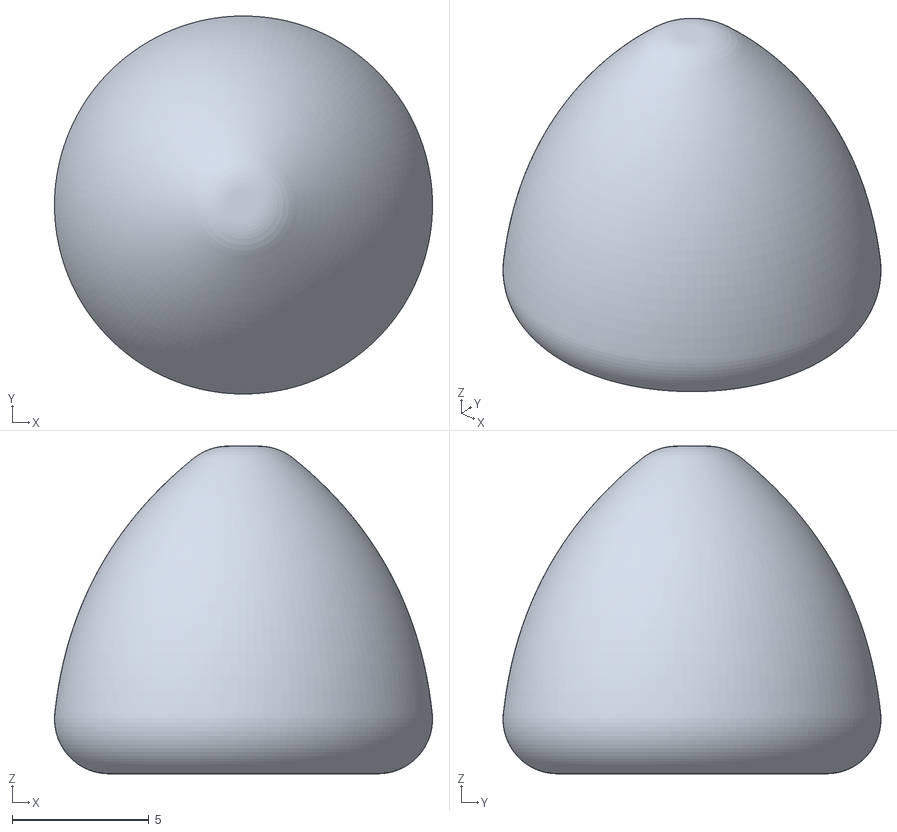
[picture p90: CAD file, 2017-07-31]
CAD/MOD/MOD-v1_knob-cap20.stl
13.8 x 13.8 x 12.0
