batchku/MO/CAD/MOD/MOD-v1_button-cap8.stl

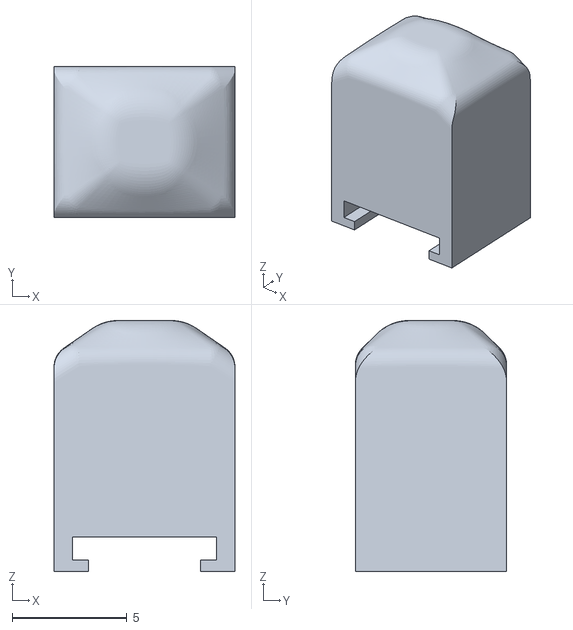
[picture p92: CAD file, 2017-07-31]
CAD/MOD/MOD-v1_button-cap8.stl
7.90 x 6.60 x 11.0
