batchku/MO/CAD/_exports/Livedraw Redraw 2017-Lightbox-Webcam FISHBOWL 02.dxf

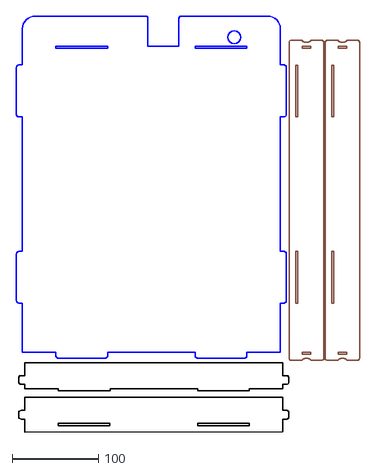
[picture p93: CAD file, 2017-07-26]
CAD/_exports/Livedraw Redraw 2017-Lightbox-Webcam FISHBOWL 02.dxf
397.9 x 482.1
