batchku/MO/CAD/_exports/Livedraw Redraw 2017-Lightbox-Webcam 04b.dxf

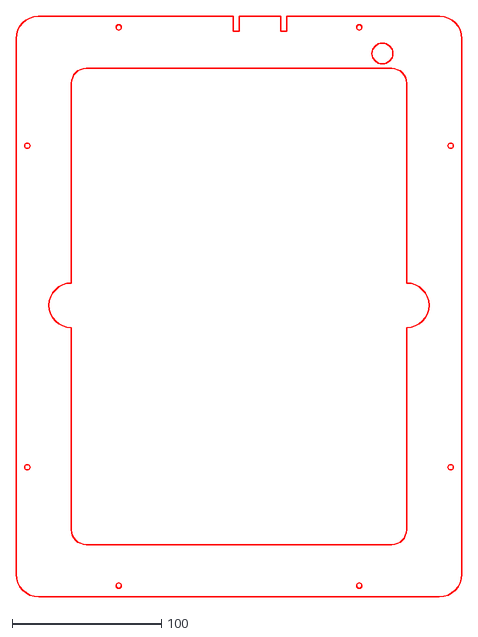
[picture p94: CAD file, 2017-07-26]
CAD/_exports/Livedraw Redraw 2017-Lightbox-Webcam 04b.dxf
299.0 x 389.5
