batchku/MO/CAD/MOD/MOD-v1_knob-cap13.stl

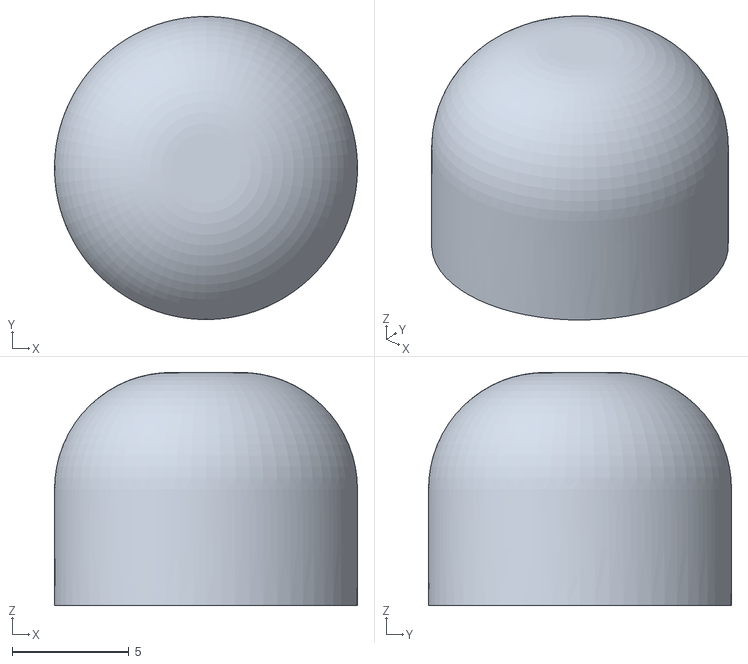
[picture p95: CAD file, 2017-07-31]
CAD/MOD/MOD-v1_knob-cap13.stl
13.0 x 13.0 x 10.0
