batchku/MO/CAD/_exports/Livedraw Redraw 2017-Lightbox-Webcam FISHBOWL 02 test.dxf

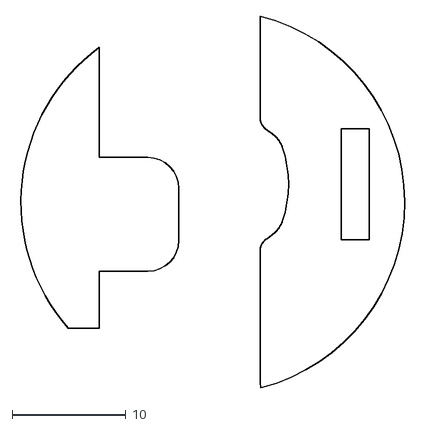
[picture p96: CAD file, 2017-07-26]
CAD/_exports/Livedraw Redraw 2017-Lightbox-Webcam FISHBOWL 02 test.dxf
34.2 x 32.7
