batchku/MO/CAD/MOD/MOD-v1_knob-cap22.stl

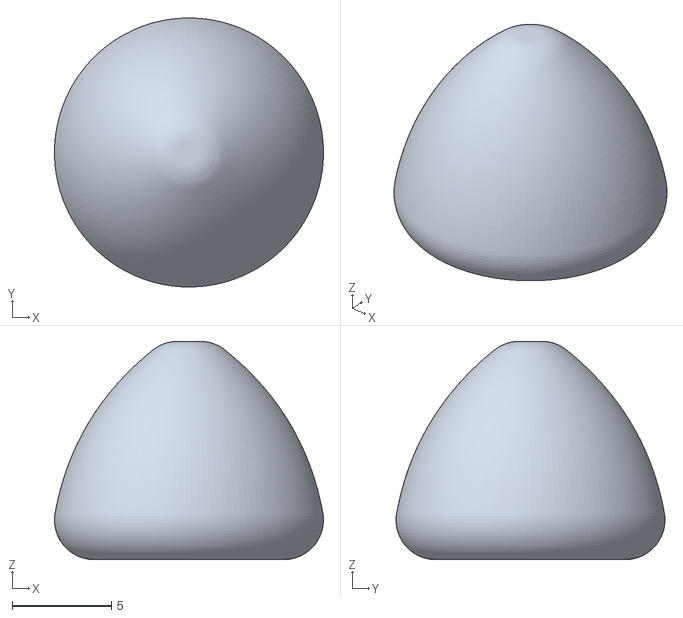
[picture p97: CAD file, 2017-07-31]
CAD/MOD/MOD-v1_knob-cap22.stl
13.6 x 13.6 x 11.0
