batchku/MO/CAD/_exports/Livedraw Redraw 2017-Lightbox-Webcam 09.dxf

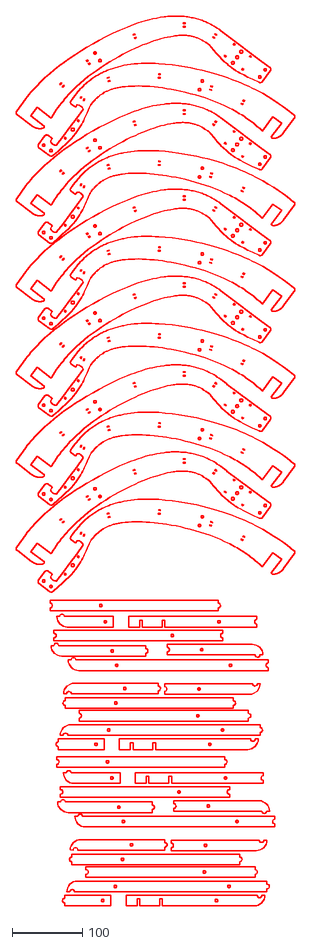
[picture p98: CAD file, 2017-07-26]
CAD/_exports/Livedraw Redraw 2017-Lightbox-Webcam 09.dxf
395.9 x 1263.5
