batchku/MO/CAD/_exports/Livedraw Redraw 2017-Lightbox-Webcam 07.dxf

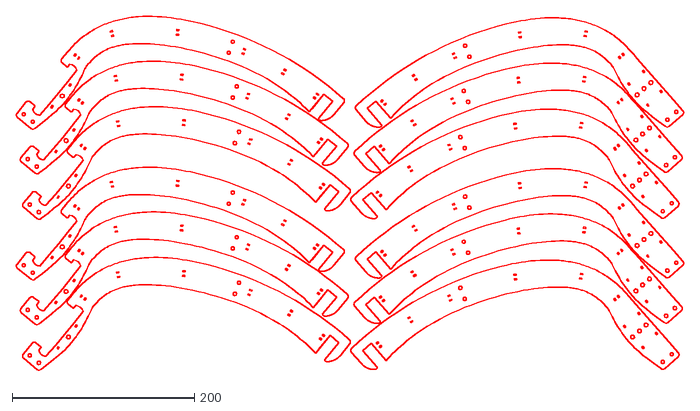
[picture p99: CAD file, 2017-07-26]
CAD/_exports/Livedraw Redraw 2017-Lightbox-Webcam 07.dxf
732.2 x 388.8
