batchku/MO/CAD/MOD/MOD-v1_proj-holder1.stl

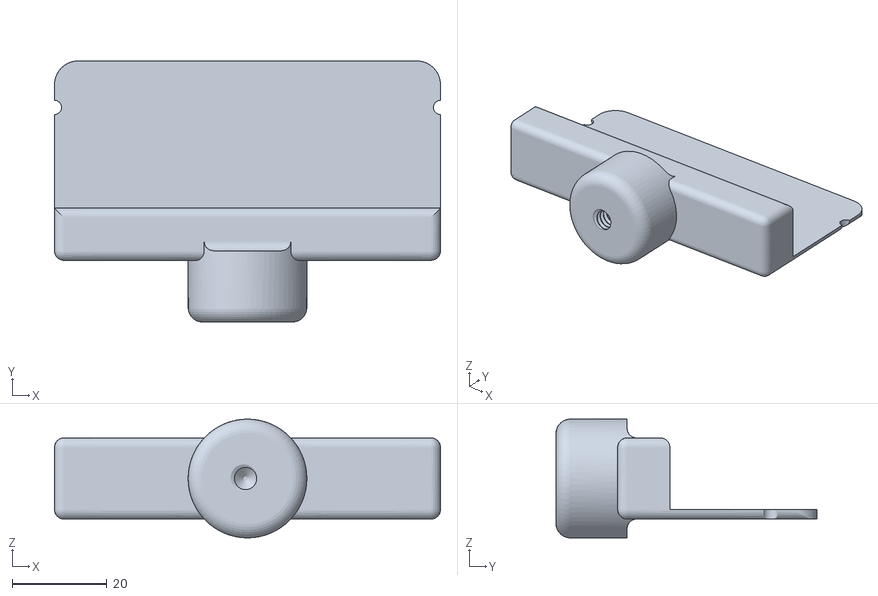
[picture p100: CAD file, 2017-07-31]
CAD/MOD/MOD-v1_proj-holder1.stl
81.3 x 55.0 x 25.0
