batchku/MO/CAD/_exports/Livedraw Redraw 2017-Lightbox-Webcam FISHBOWL 02b.dxf

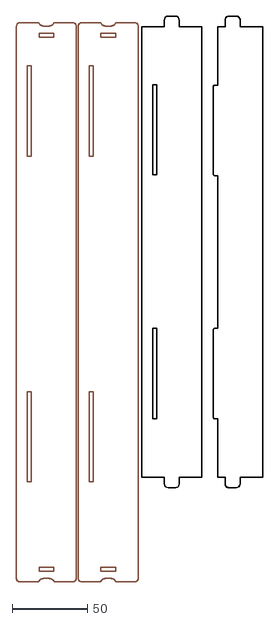
[picture p101: CAD file, 2017-07-26]
CAD/_exports/Livedraw Redraw 2017-Lightbox-Webcam FISHBOWL 02b.dxf
163.6 x 375.5
