batchku/MO/CAD/MOD/MOD-v1_knob-cap10.stl

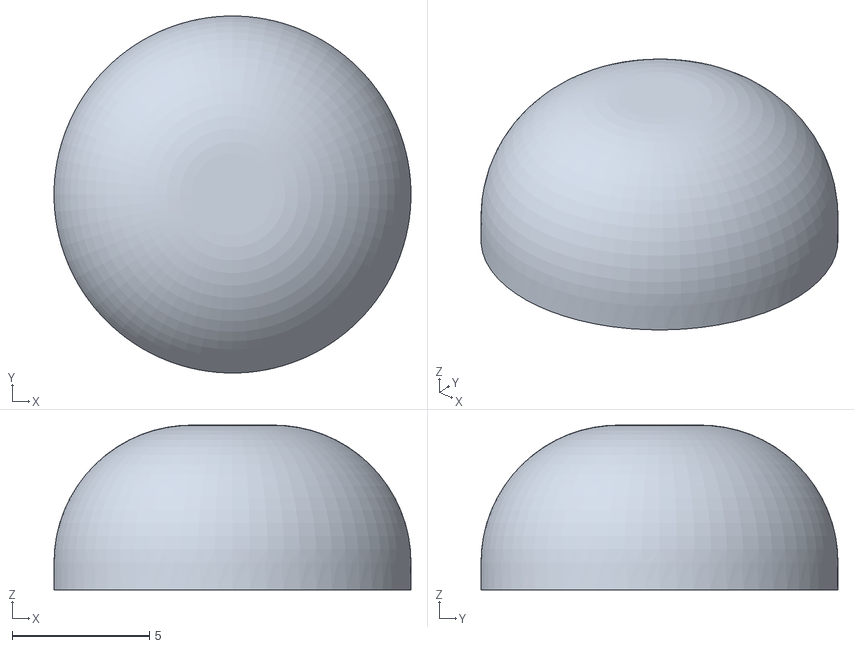
[picture p102: CAD file, 2017-07-31]
CAD/MOD/MOD-v1_knob-cap10.stl
13.0 x 13.0 x 6.00
