batchku/MO/CAD/MOD/MOD-v1_proj-holder2.stl

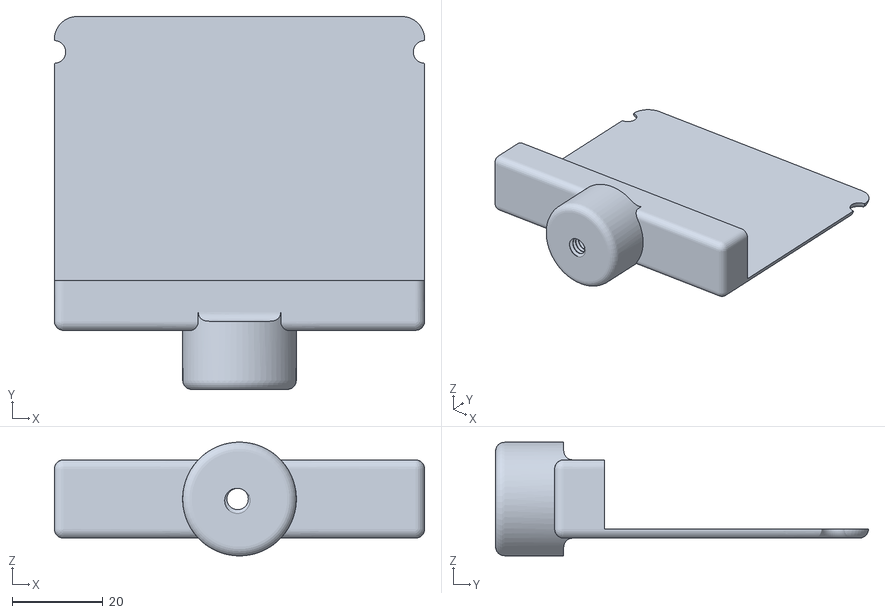
[picture p103: CAD file, 2017-07-31]
CAD/MOD/MOD-v1_proj-holder2.stl
81.4 x 82.0 x 25.0
