batchku/MO/CAD/_exports/Livedraw Redraw 2017-Lightbox-Webcam FISHBOWL 01b.dxf

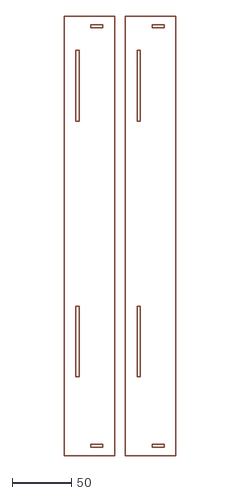
[picture p104: CAD file, 2017-07-26]
CAD/_exports/Livedraw Redraw 2017-Lightbox-Webcam FISHBOWL 01b.dxf
94.6 x 371.2
