batchku/MO/CAD/MOD/MOD-v1_knob-cap11.stl

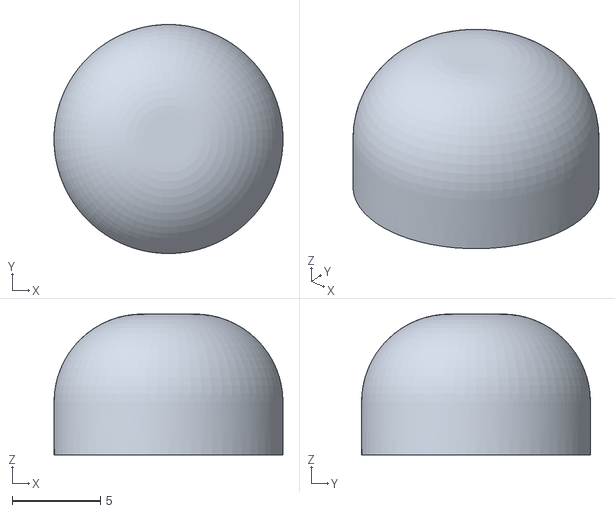
[picture p105: CAD file, 2017-07-31]
CAD/MOD/MOD-v1_knob-cap11.stl
13.0 x 13.0 x 8.00
