batchku/MO/CAD/_exports/Livedraw Redraw 2017-Lightbox-Webcam 05.dxf

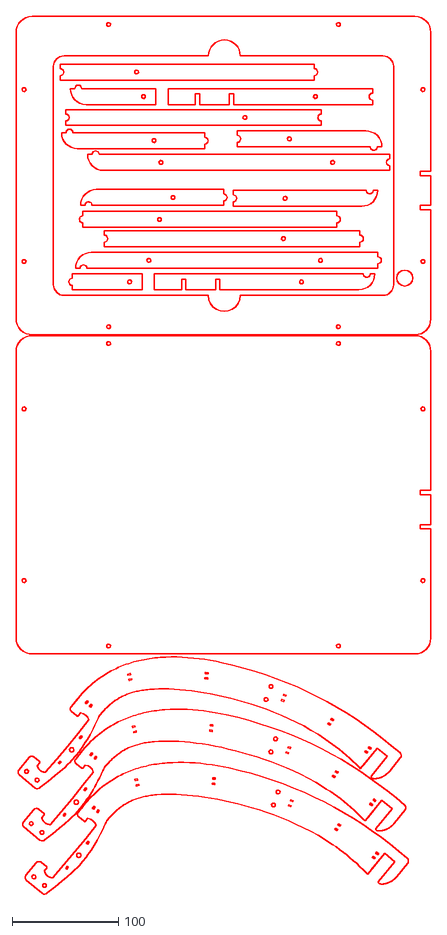
[picture p106: CAD file, 2017-07-26]
CAD/_exports/Livedraw Redraw 2017-Lightbox-Webcam 05.dxf
389.5 x 824.9
