batchku/MO/CAD/MOD/MOD-v1_knob-cap14.stl

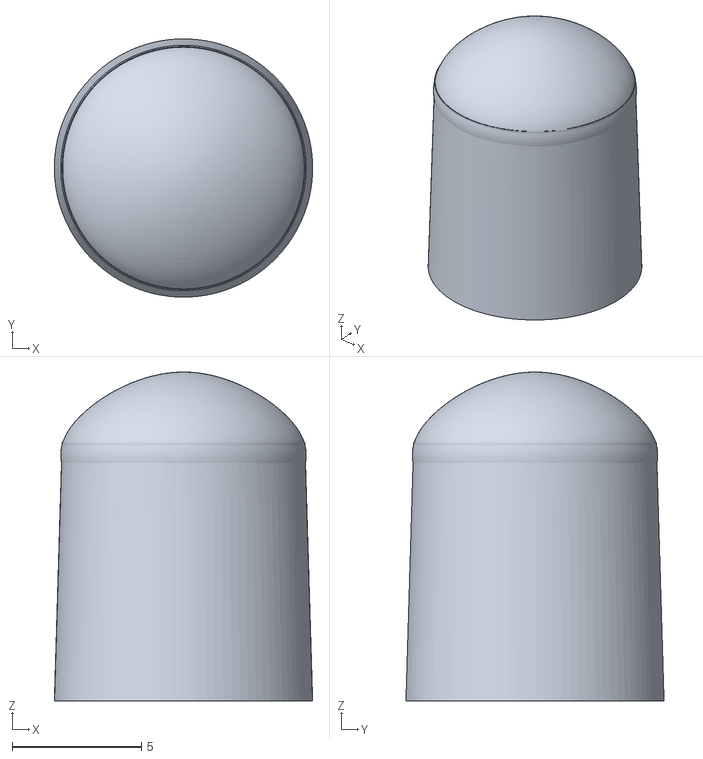
[picture p107: CAD file, 2017-07-31]
CAD/MOD/MOD-v1_knob-cap14.stl
10.0 x 9.99 x 12.7
