batchku/MO/CAD/_exports/Livedraw Redraw 2017-Lightbox-Webcam 05b.dxf

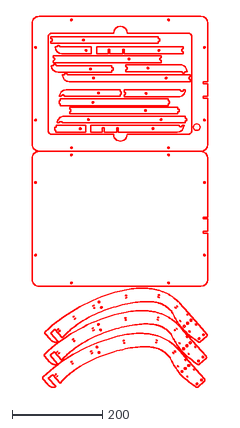
[picture p108: CAD file, 2017-07-26]
CAD/_exports/Livedraw Redraw 2017-Lightbox-Webcam 05b.dxf
389.5 x 823.8
