batchku/MO/CAD/MOD/MOD-v1_knob-cap23.stl

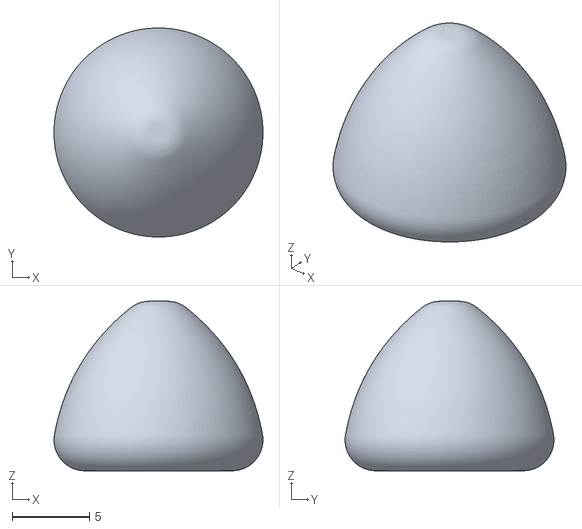
[picture p109: CAD file, 2017-07-31]
CAD/MOD/MOD-v1_knob-cap23.stl
13.6 x 13.6 x 11.0
