batchku/MO/CAD/_exports/Livedraw Redraw 2017-Lightbox-Webcam 02.dxf

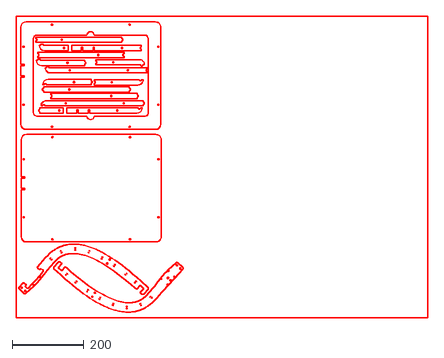
[picture p110: CAD file, 2017-07-26]
CAD/_exports/Livedraw Redraw 2017-Lightbox-Webcam 02.dxf
1143.0 x 838.0
