batchku/MO/CAD/_exports/Livedraw Redraw 2017-Lightbox-Webcam 08.dxf

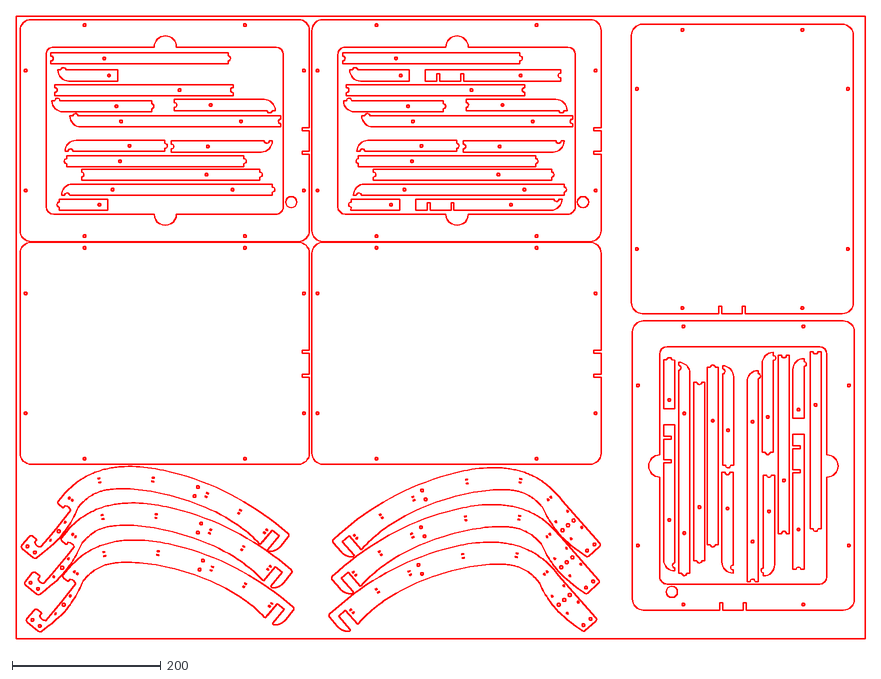
[picture p111: CAD file, 2017-07-26]
CAD/_exports/Livedraw Redraw 2017-Lightbox-Webcam 08.dxf
1143.0 x 838.0
