batchku/MO/CAD/MOD/MOM-holder-top_v3-2c.dxf

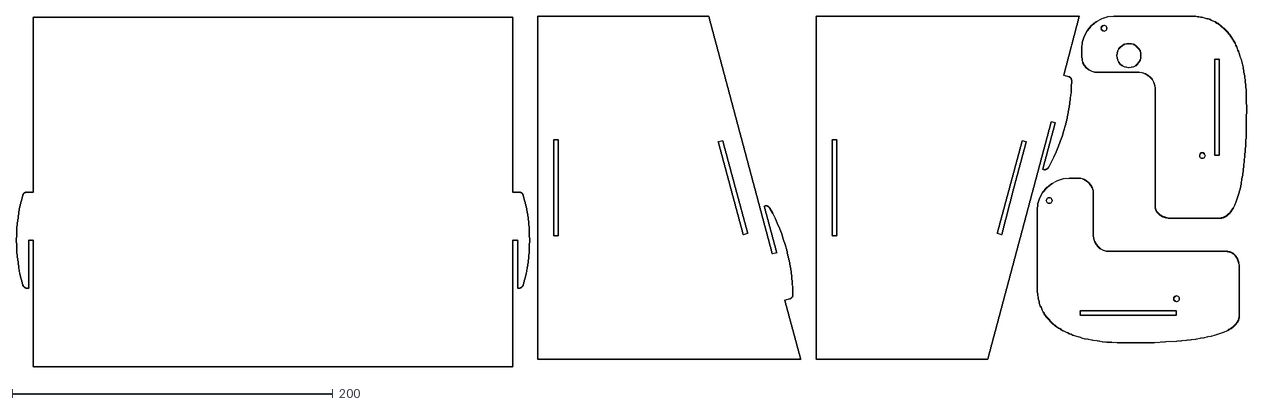
[picture p112: CAD file, 2017-07-31]
CAD/MOD/MOM-holder-top_v3-2c.dxf
767.1 x 218.6
