batchku/MO/CAD/MOD/MOM-mid-plane-ali_v3-2d.dxf

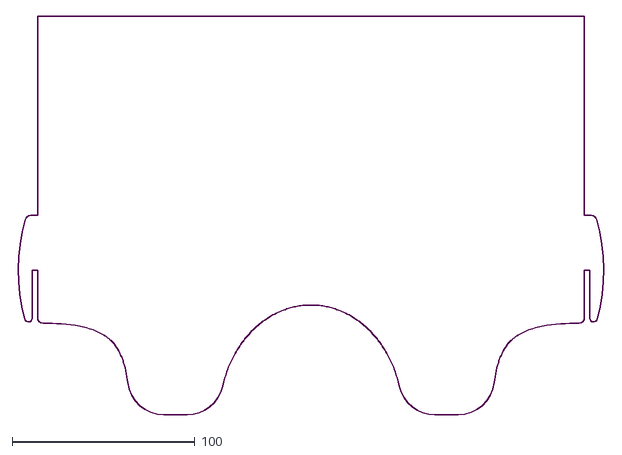
[picture p114: CAD file, 2017-07-31]
CAD/MOD/MOM-mid-plane-ali_v3-2d.dxf
322.6 x 217.9
