batchku/MO/CAD/_exports/Livedraw Redraw 2017-Lightbox-Webcam v2.dxf

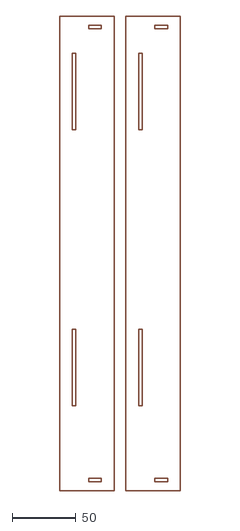
[picture p115: CAD file, 2017-07-26]
CAD/_exports/Livedraw Redraw 2017-Lightbox-Webcam v2.dxf
94.6 x 371.2
