batchku/MO/CAD/MOD/MOD-v1_knob-cap9.stl

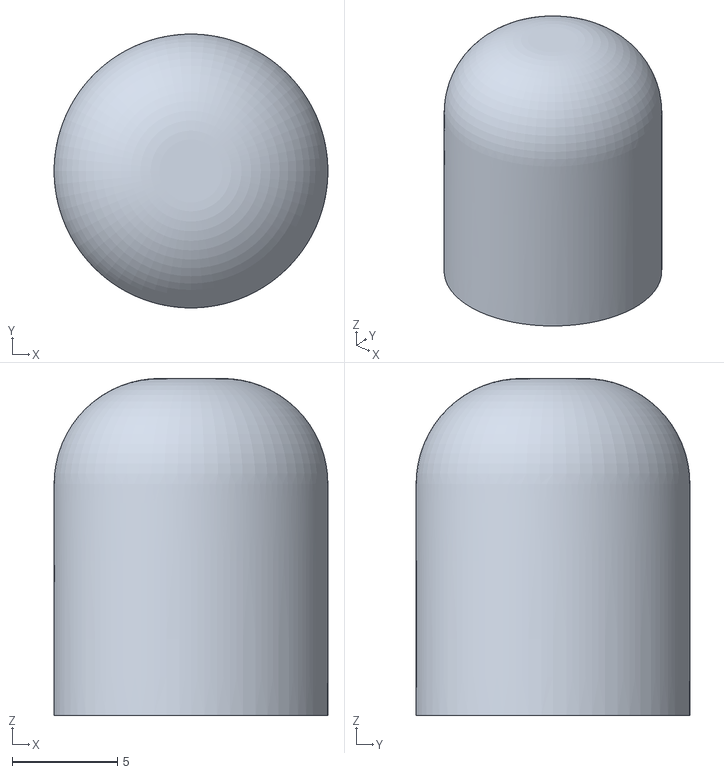
[picture p116: CAD file, 2017-07-31]
CAD/MOD/MOD-v1_knob-cap9.stl
13.0 x 13.0 x 16.0
