batchku/MO/CAD/_exports/Livedraw Redraw 2017-Lightbox-Webcam 03.dxf

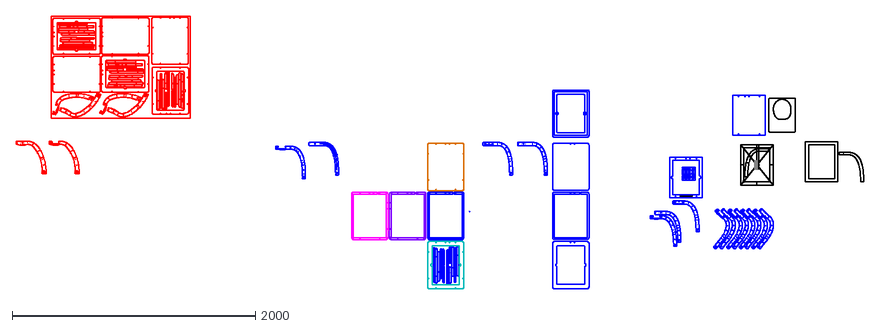
[picture p117: CAD file, 2017-07-26]
CAD/_exports/Livedraw Redraw 2017-Lightbox-Webcam 03.dxf
6964.1 x 2241.8
