batchku/MO/CAD/MOD/MOD-v1_button-cap7.stl

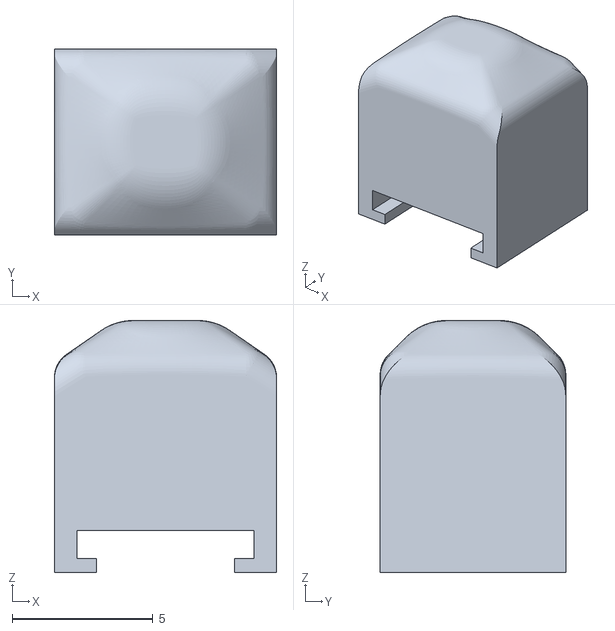
[picture p118: CAD file, 2017-07-31]
CAD/MOD/MOD-v1_button-cap7.stl
7.90 x 6.60 x 8.96
