batchku/MO/CAD/_exports/Livedraw Redraw 2017-Lightbox-Webcam 06a.dxf

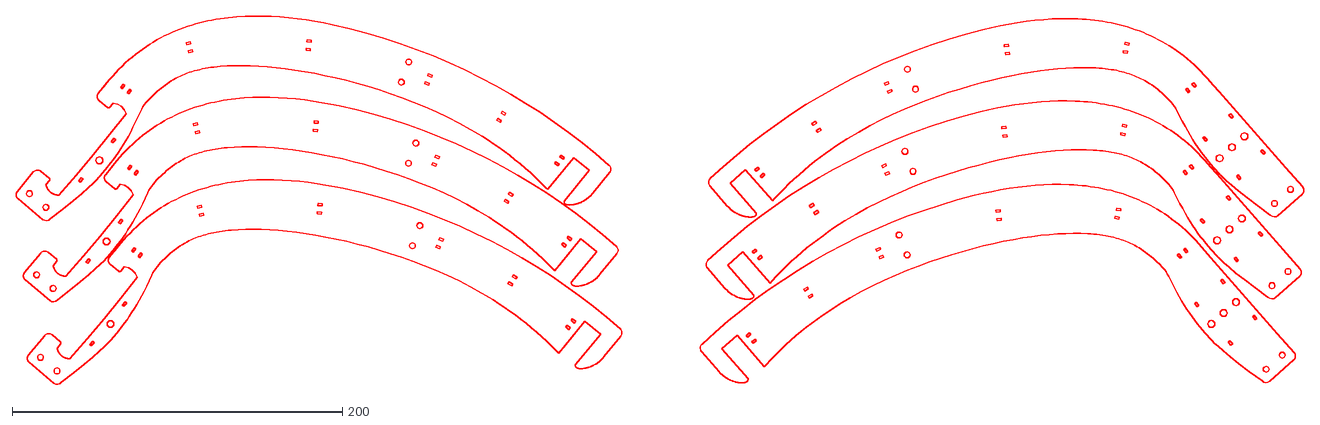
[picture p119: CAD file, 2017-07-26]
CAD/_exports/Livedraw Redraw 2017-Lightbox-Webcam 06a.dxf
779.3 x 223.2
