batchku/MO/CAD/MOD/MOM-mid-plane-ali_v3-2e.dxf

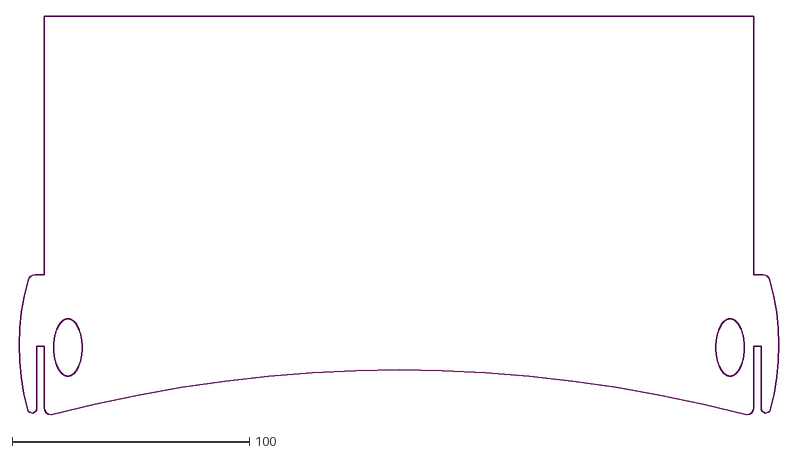
[picture p120: CAD file, 2017-07-31]
CAD/MOD/MOM-mid-plane-ali_v3-2e.dxf
322.6 x 167.9
