batchku/MO/CAD/MOD/MOM-holder-top_v3-2.dxf

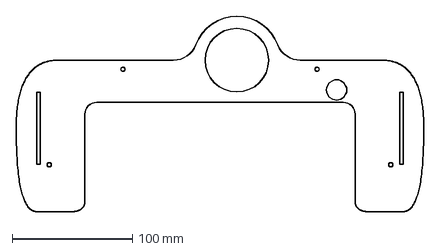
[picture p121: CAD file, 2017-07-31]
CAD/MOD/MOM-holder-top_v3-2.dxf
339.1 x 162.4 mm
