batchku/MO/CAD/MOD/MOD-v1_knob-cap15.stl

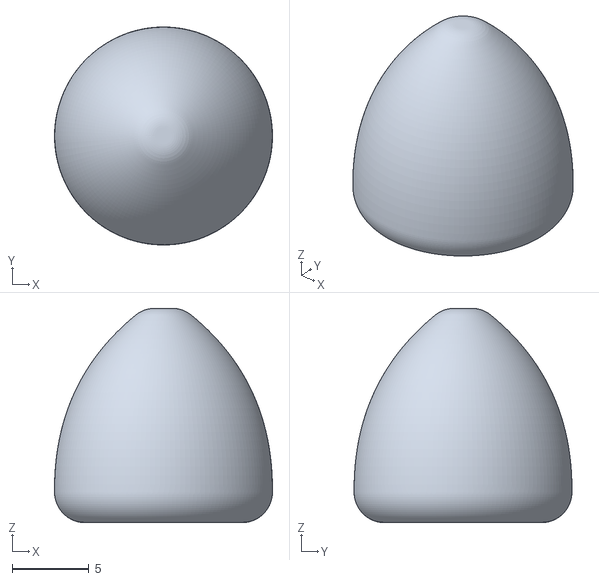
[picture p123: CAD file, 2017-07-31]
CAD/MOD/MOD-v1_knob-cap15.stl
14.2 x 14.2 x 14.0
