batchku/MO/CAD/MOD/MOD-v1.1d.dxf

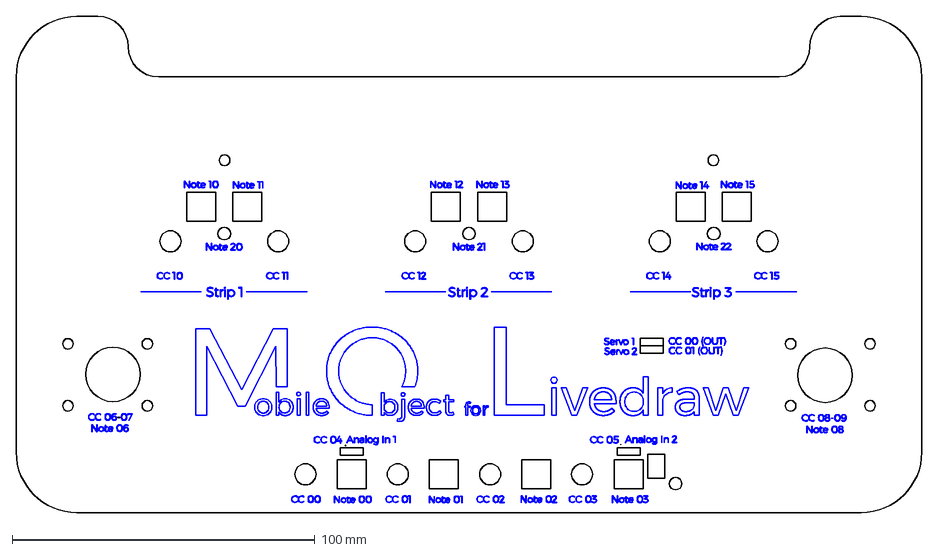
[picture p124: CAD file, 2017-07-31]
CAD/MOD/MOD-v1.1d.dxf
299.0 x 163.8 mm
