batchku/MO/CAD/MOD/MOD-v1.1-neck-v3-2a.dxf

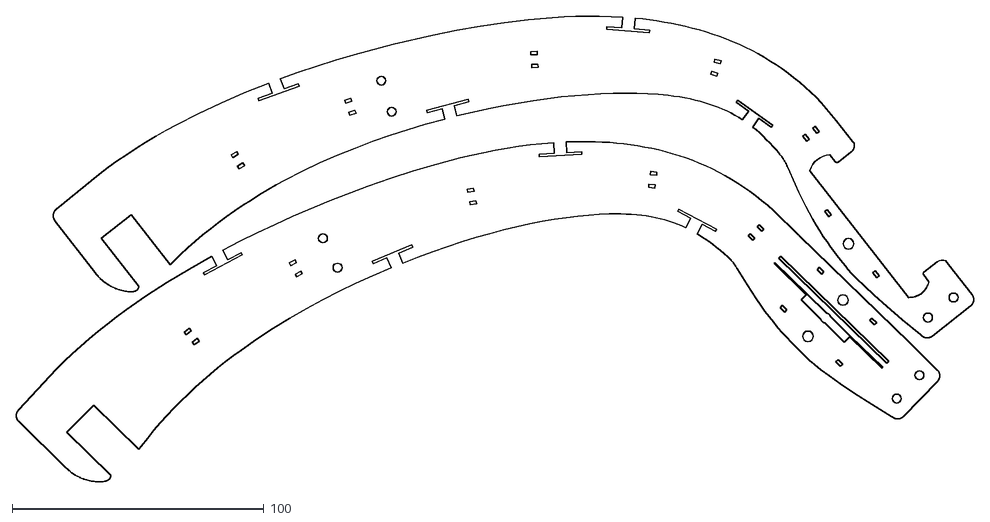
[picture p126: CAD file, 2017-07-31]
CAD/MOD/MOD-v1.1-neck-v3-2a.dxf
380.2 x 184.8
