batchku/MO/CAD/MOD/MOD-v1.1b.dxf

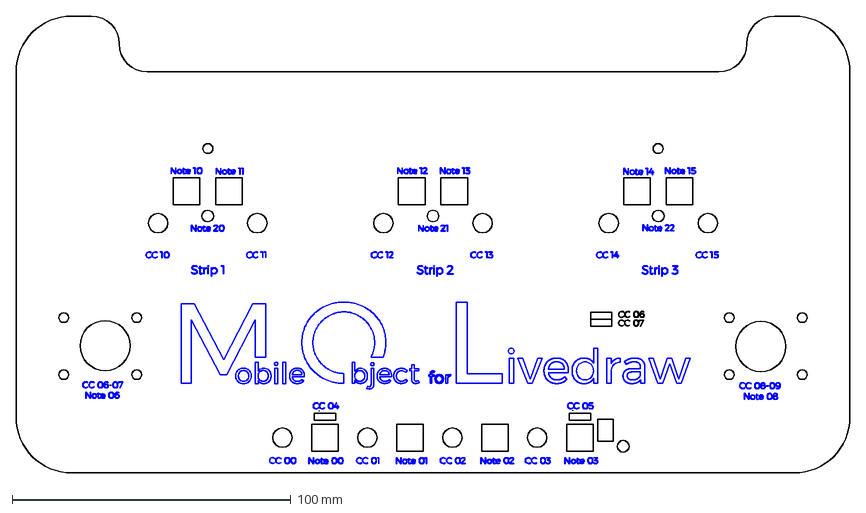
[picture p127: CAD file, 2017-07-28]
CAD/MOD/MOD-v1.1b.dxf
299.0 x 163.8 mm
