batchku/MO/CAD/MOD/MOD-v1.1c.dxf

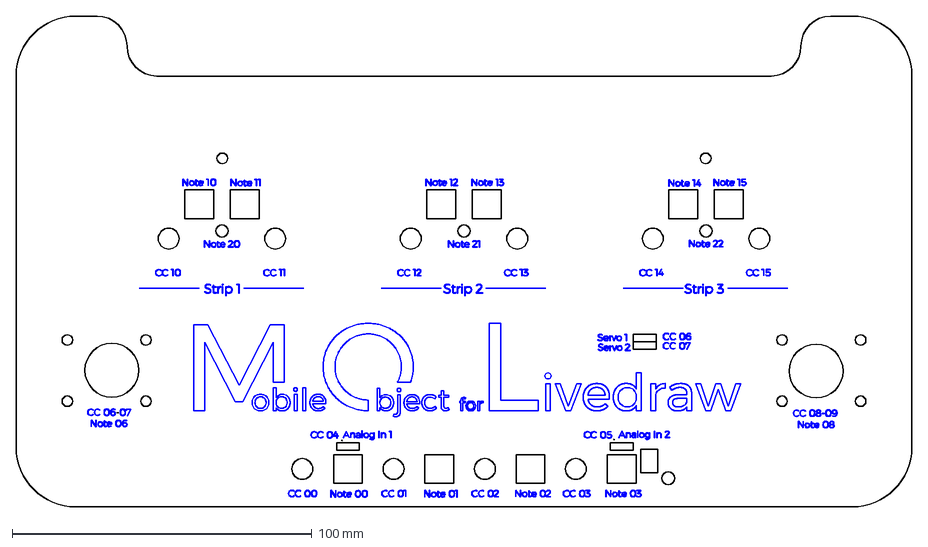
[picture p128: CAD file, 2017-07-28]
CAD/MOD/MOD-v1.1c.dxf
299.0 x 163.8 mm
