batchku/MO/CAD/MOD/MOD-v1.1a.dxf

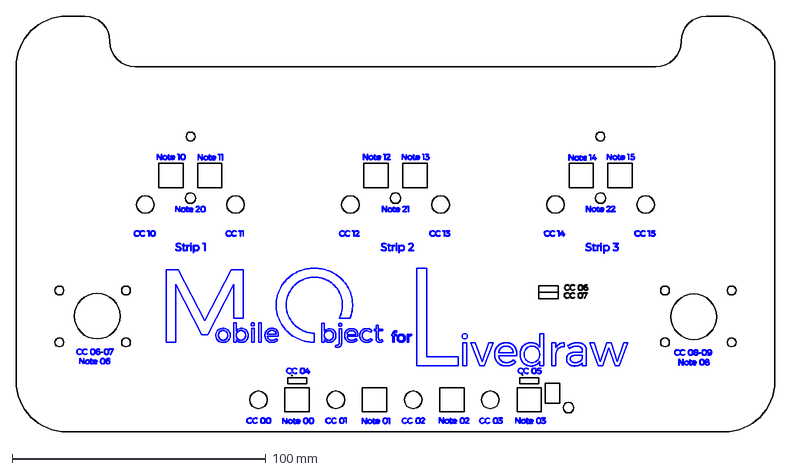
[picture p129: CAD file, 2017-07-28]
CAD/MOD/MOD-v1.1a.dxf
299.0 x 163.8 mm
