batchku/MO/CAD/MOD/MOD-v1_knob-cap4.stl

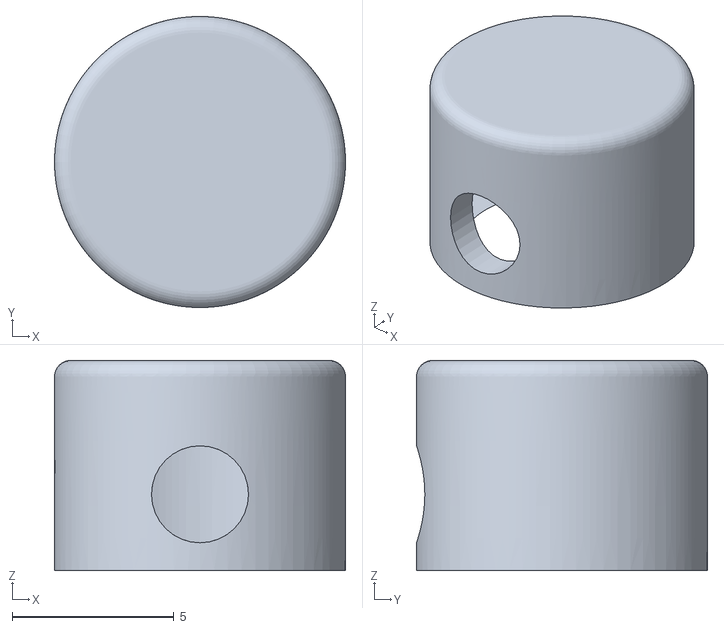
[picture p130: CAD file, 2017-07-28]
CAD/MOD/MOD-v1_knob-cap4.stl
9.00 x 9.00 x 6.50
