batchku/MO/CAD/MOD/MOD-v1_knob-cap6.stl

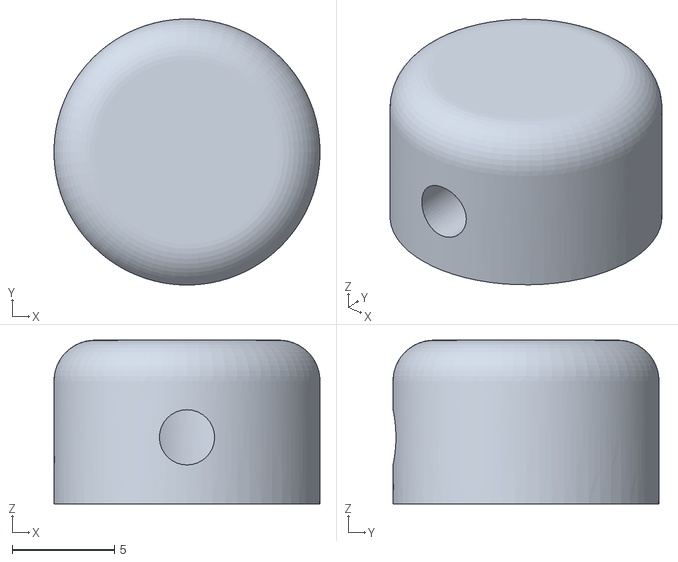
[picture p131: CAD file, 2017-07-28]
CAD/MOD/MOD-v1_knob-cap6.stl
13.0 x 13.0 x 8.00
