batchku/MO/CAD/MOD/MOD-v1_button-cap4.stl

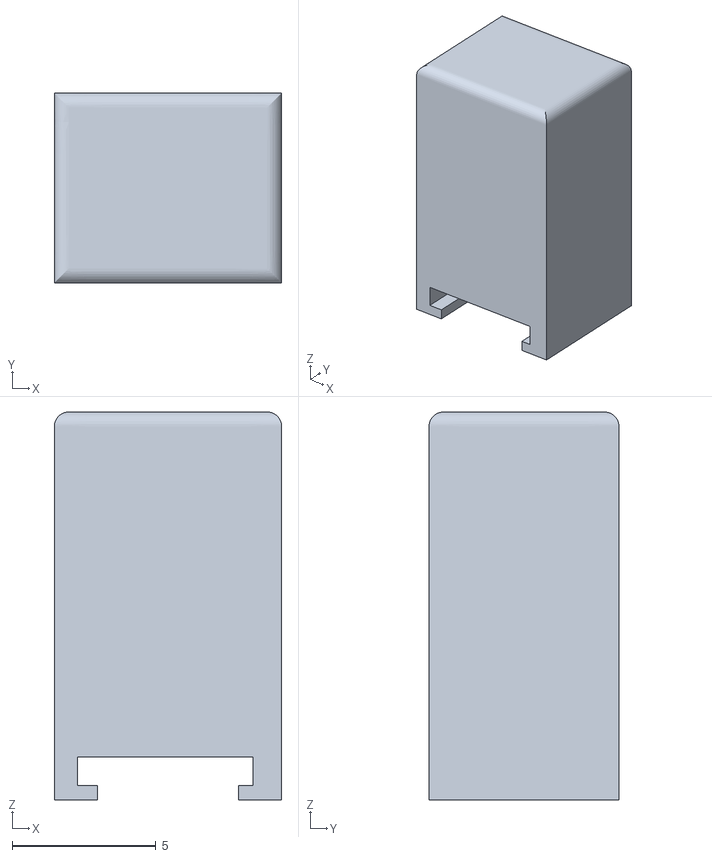
[picture p133: CAD file, 2017-07-28]
CAD/MOD/MOD-v1_button-cap4.stl
7.90 x 6.60 x 13.5
