batchku/MO/CAD/MOD/MOD-v1_button-cap5.stl

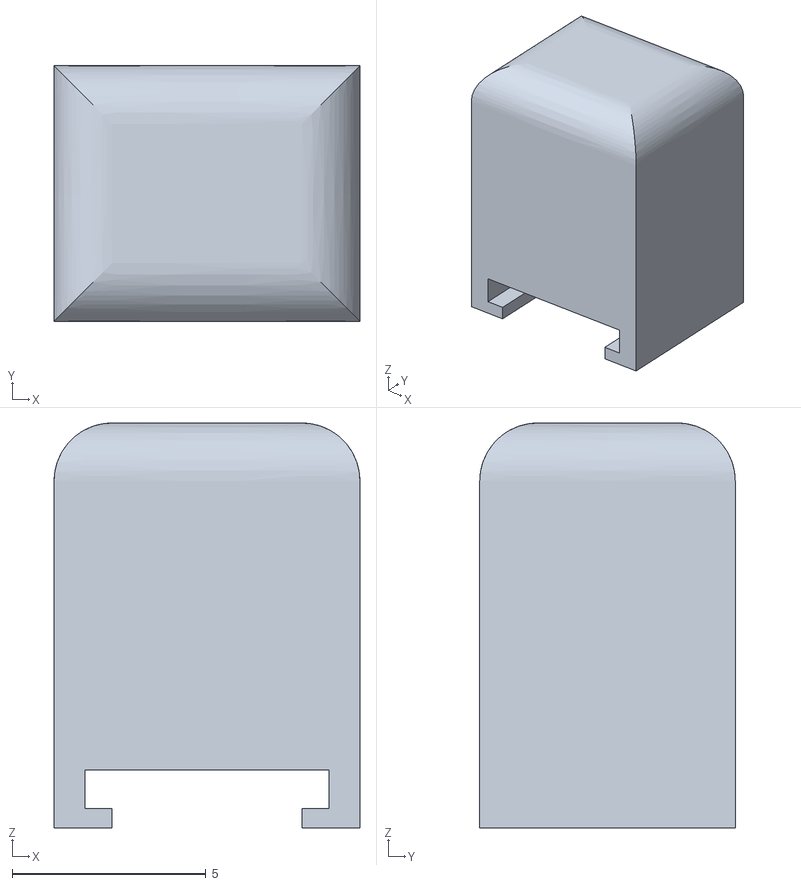
[picture p134: CAD file, 2017-07-28]
CAD/MOD/MOD-v1_button-cap5.stl
7.90 x 6.60 x 10.5
