batchku/MO/CAD/MOD/MOD-v1_button-cap6.stl

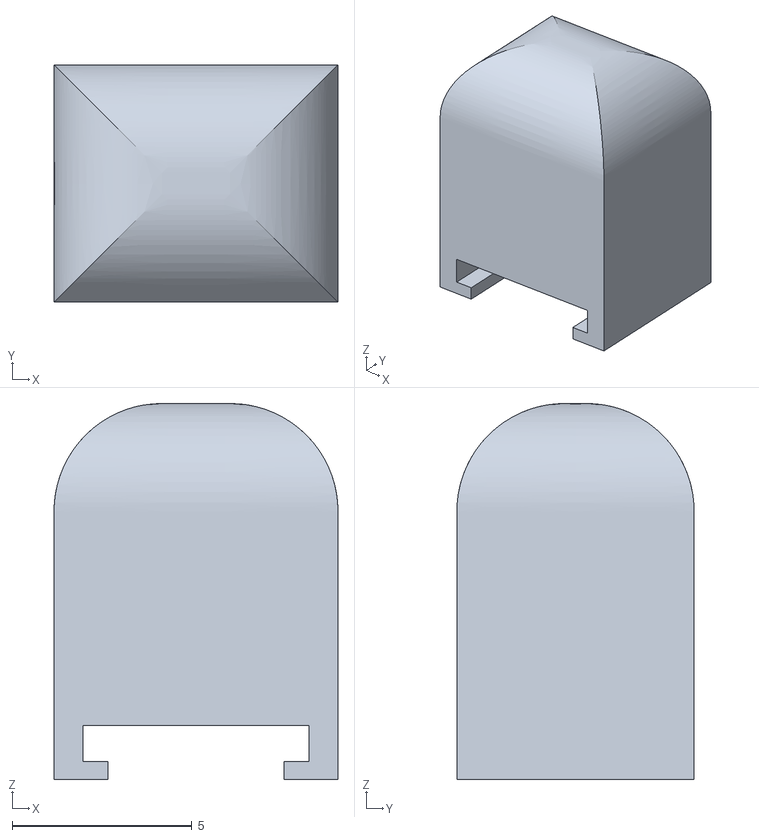
[picture p135: CAD file, 2017-07-28]
CAD/MOD/MOD-v1_button-cap6.stl
7.90 x 6.60 x 10.5
