batchku/MO/CAD/MOD/MOD-v1_knob-cap5.stl

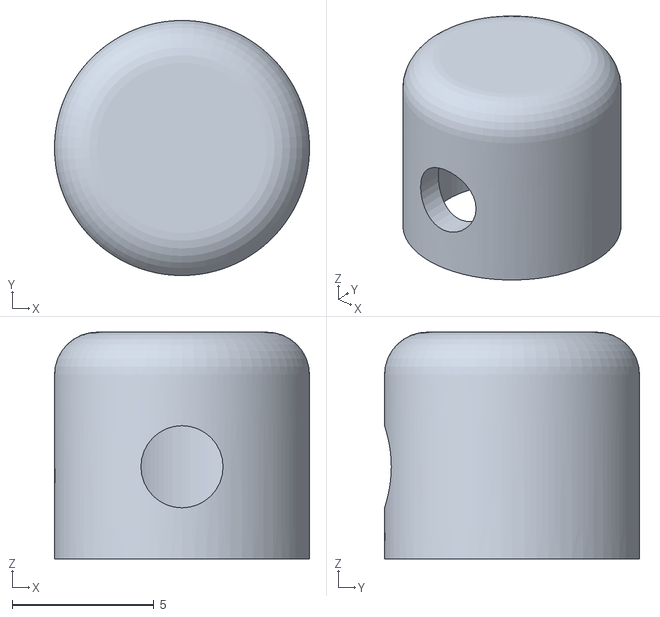
[picture p136: CAD file, 2017-07-28]
CAD/MOD/MOD-v1_knob-cap5.stl
9.00 x 9.00 x 8.00
