batchku/MO/CAD/MOD/MOD-v1_button-cap3.stl

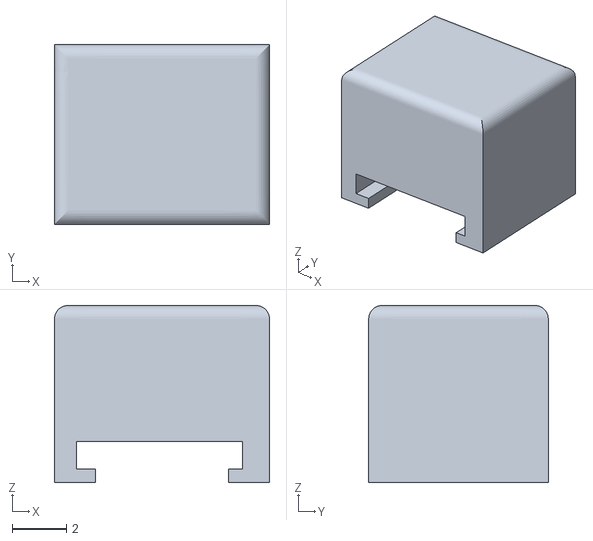
[picture p137: CAD file, 2017-07-28]
CAD/MOD/MOD-v1_button-cap3.stl
7.90 x 6.60 x 6.51
