batchku/MO/PCBs/MO/_archive/MOD-v1.1.brd

## EAGLE design PCBs/MO/_archive/MOD-v1.1.brd (2017-07-26, an earlier design)

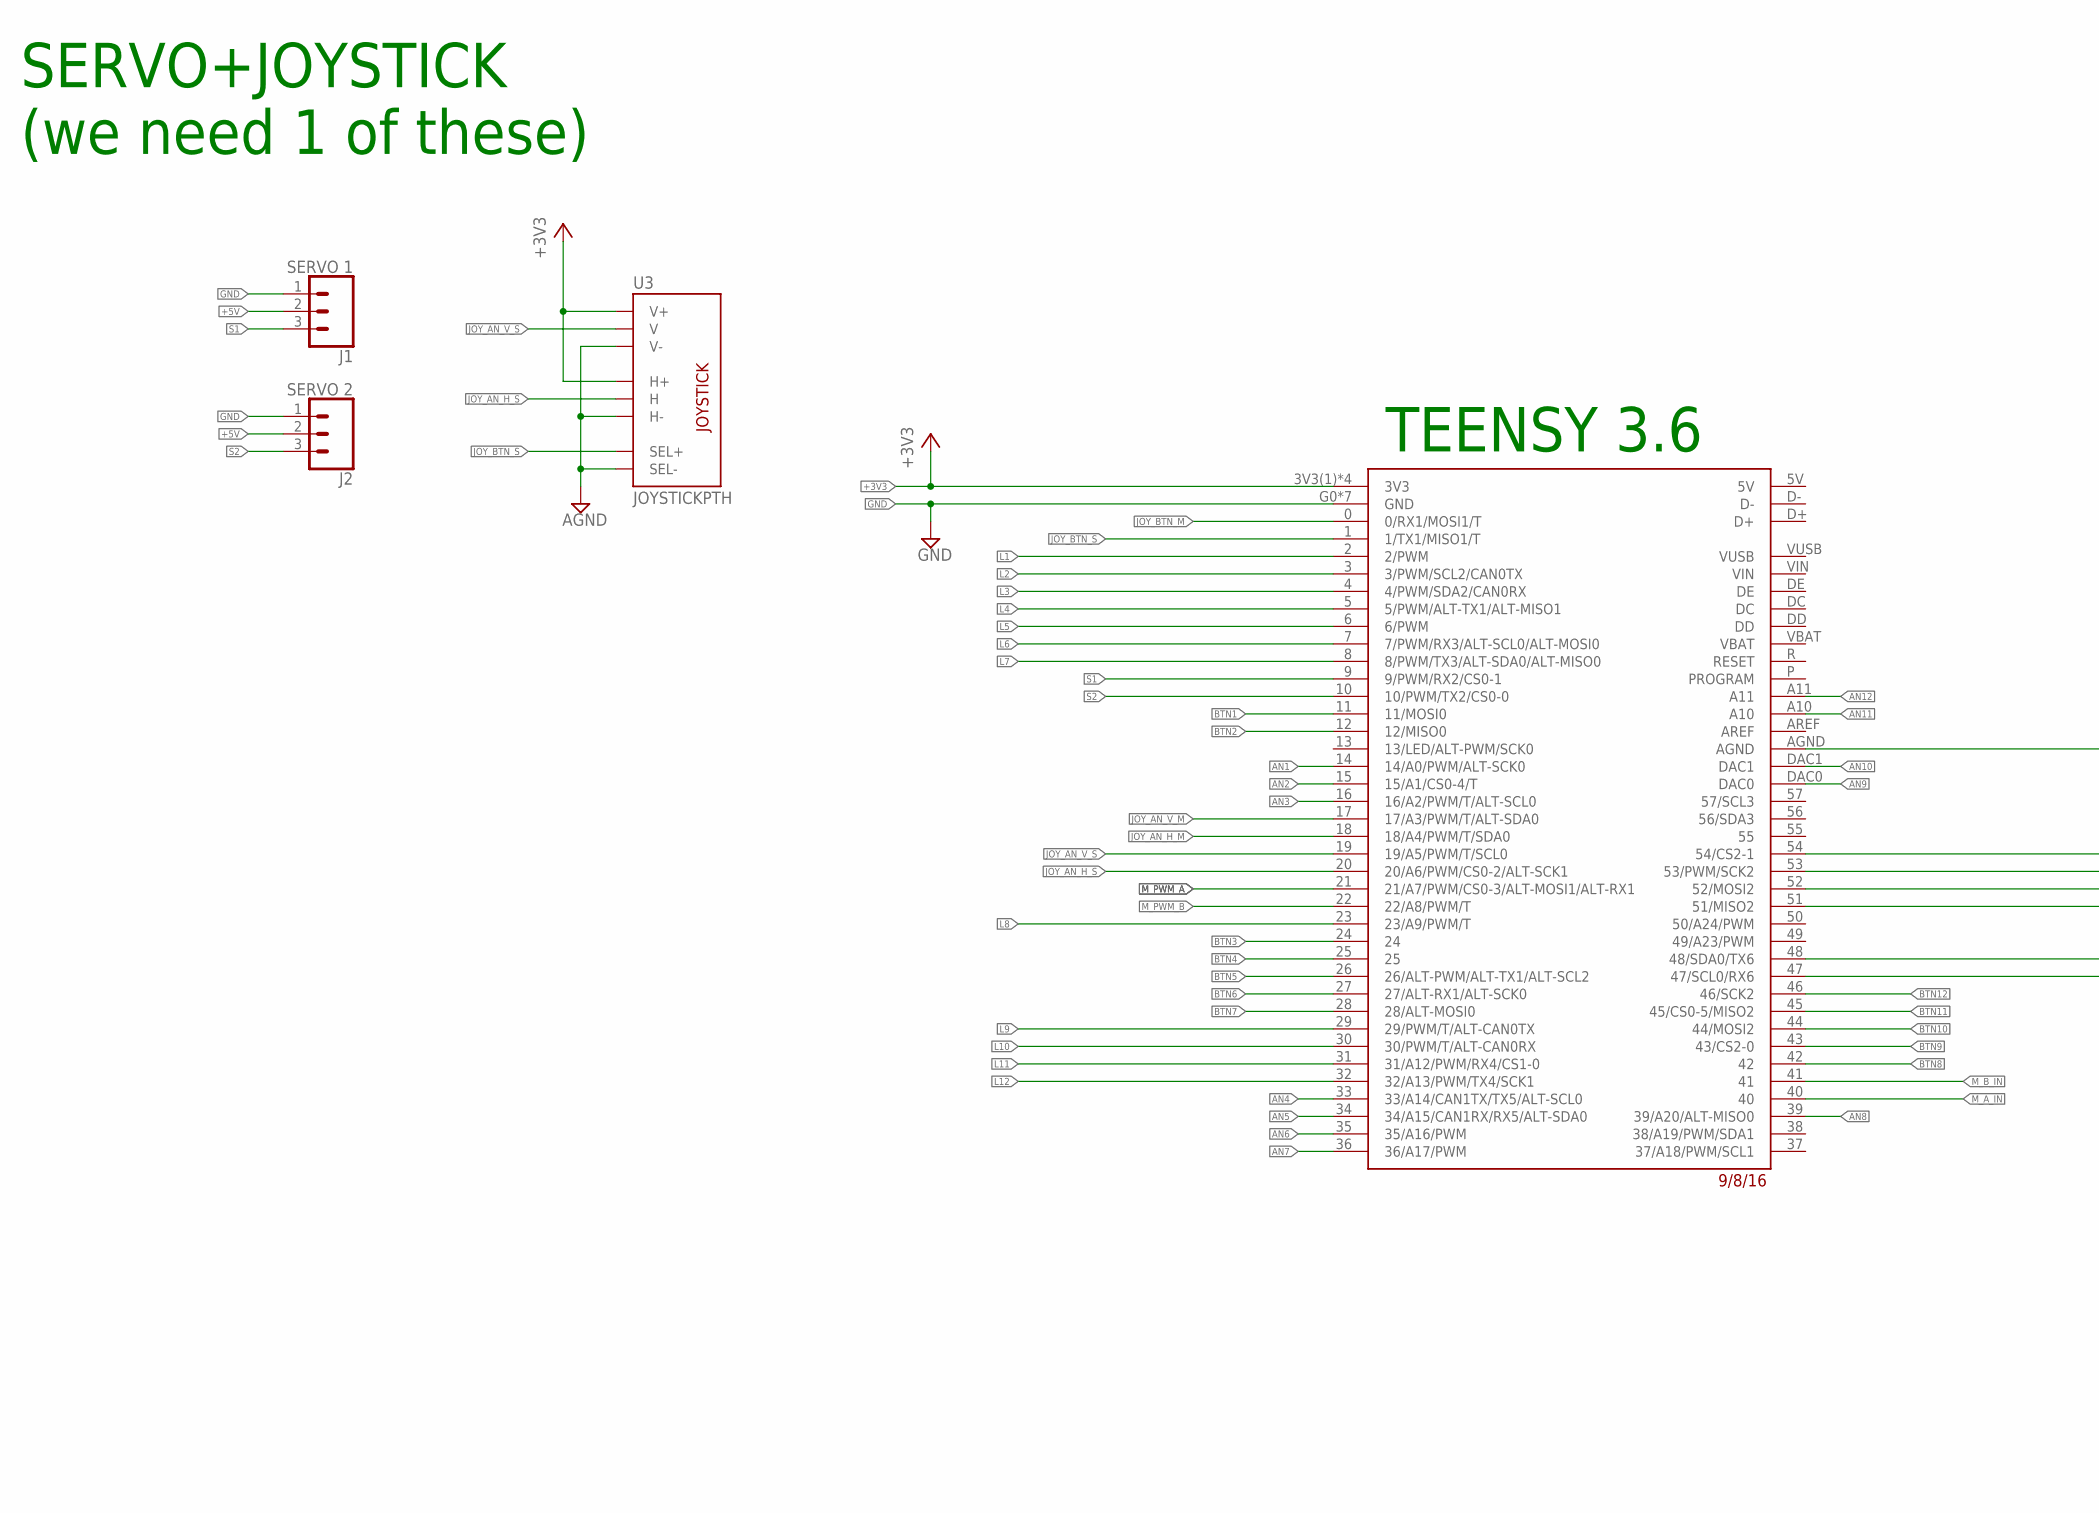
[picture p172: schematic MOD-v1.1.sch, part in row 1, column 1]

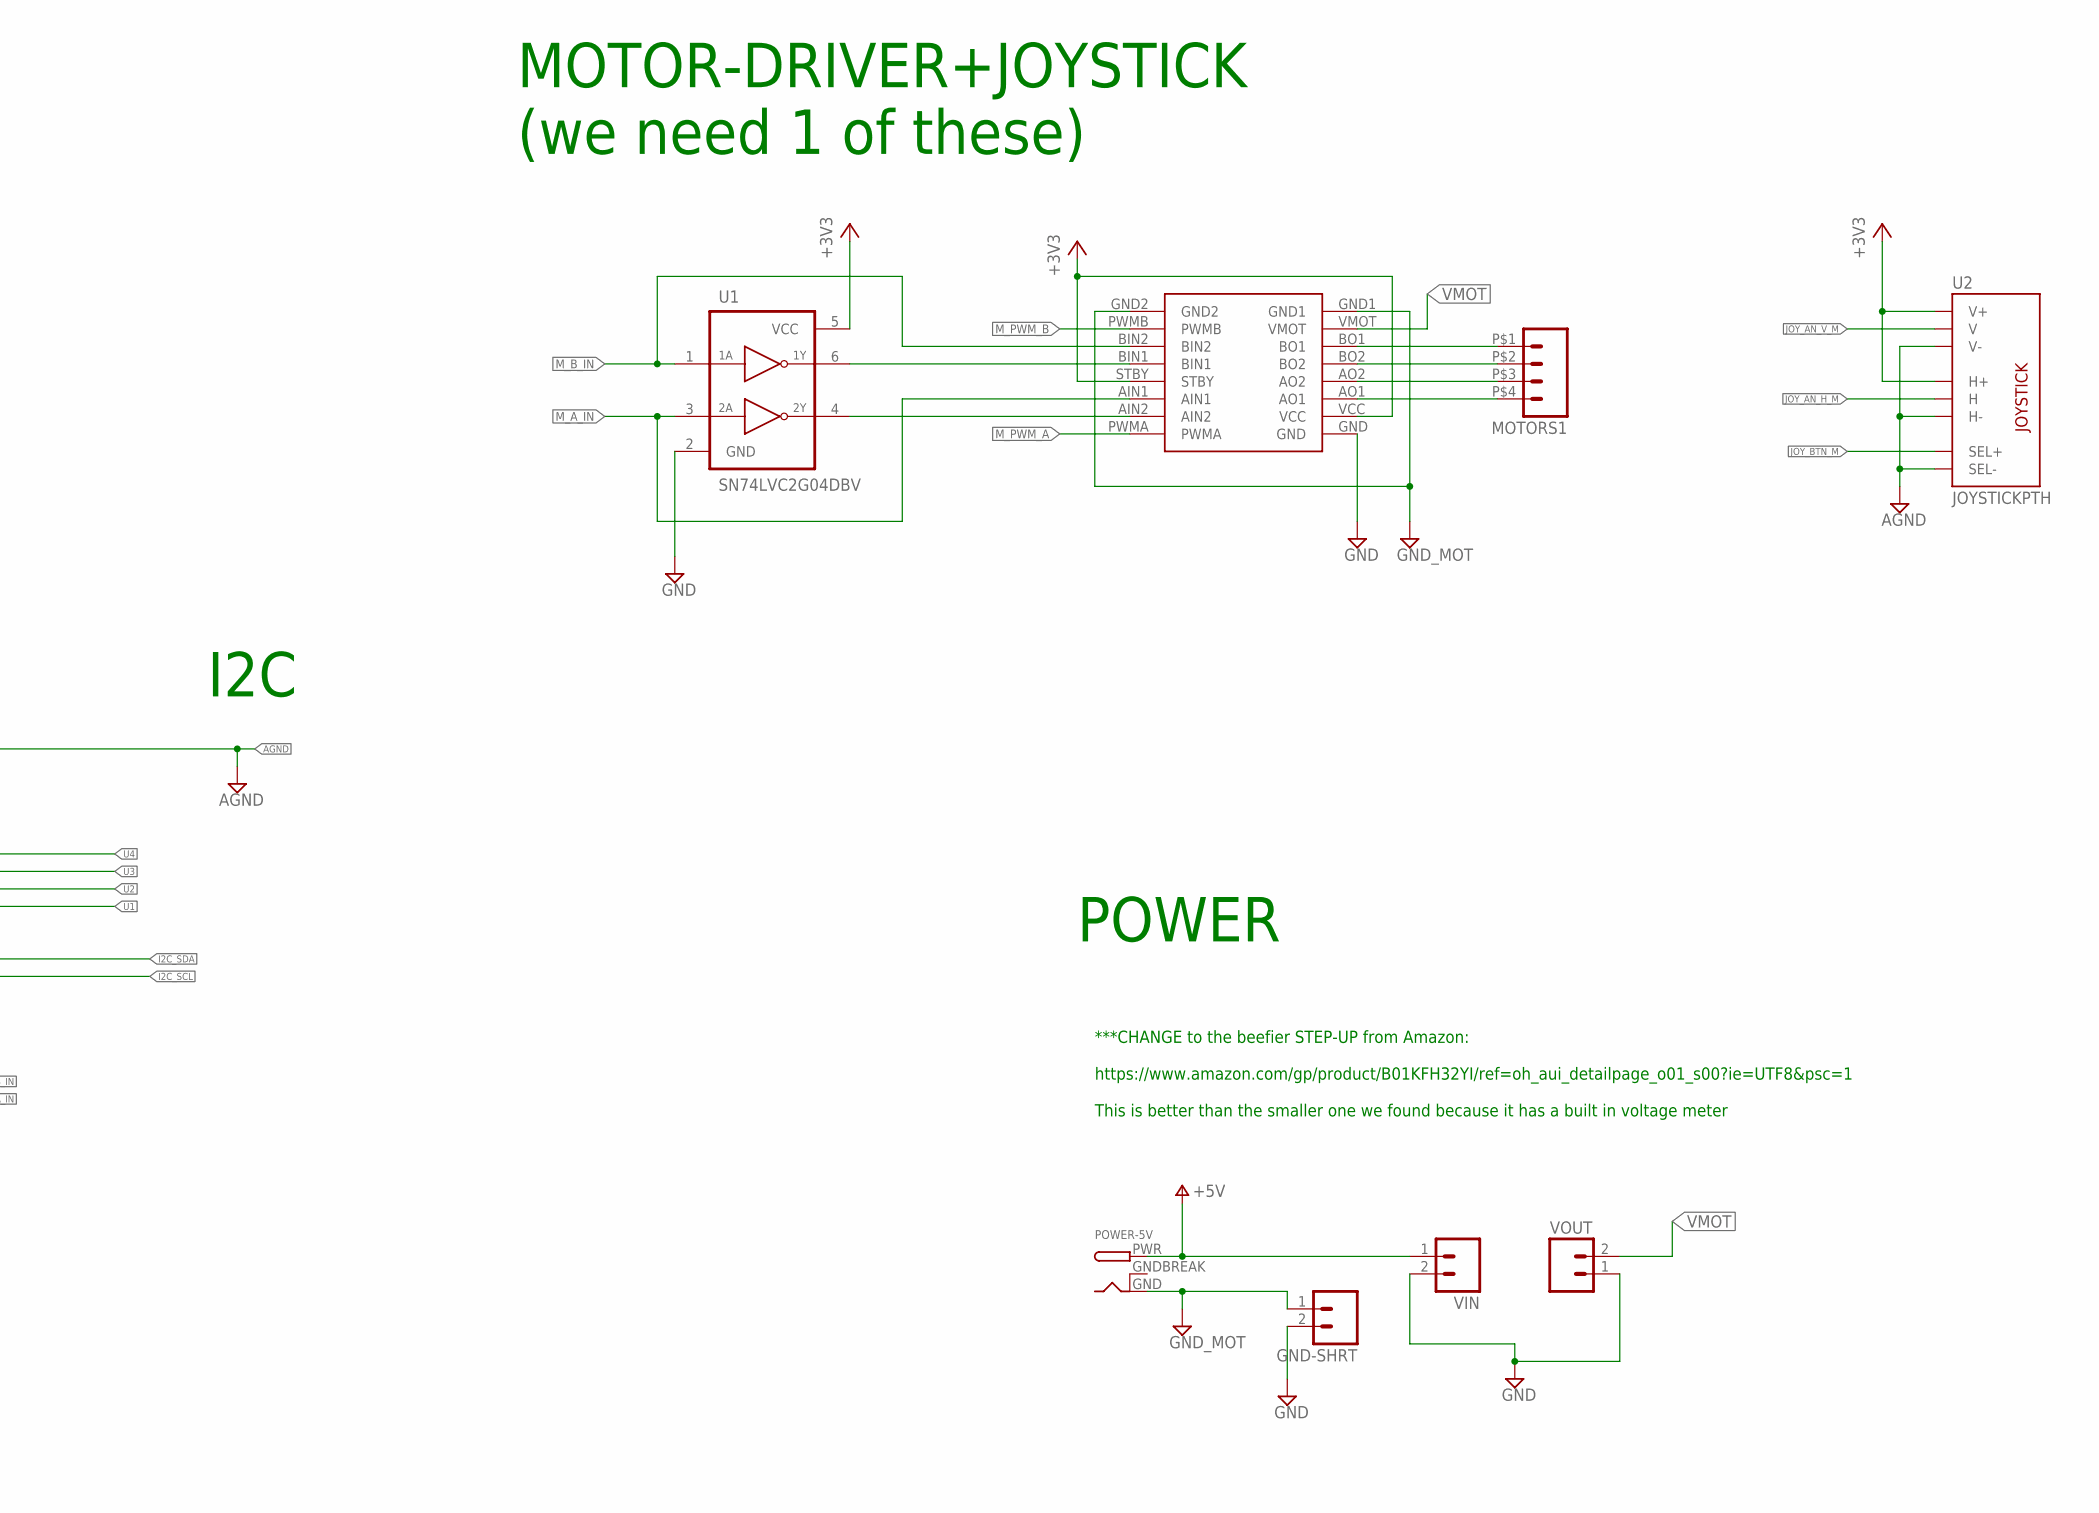
[picture p173: schematic MOD-v1.1.sch, part in row 1, column 2]

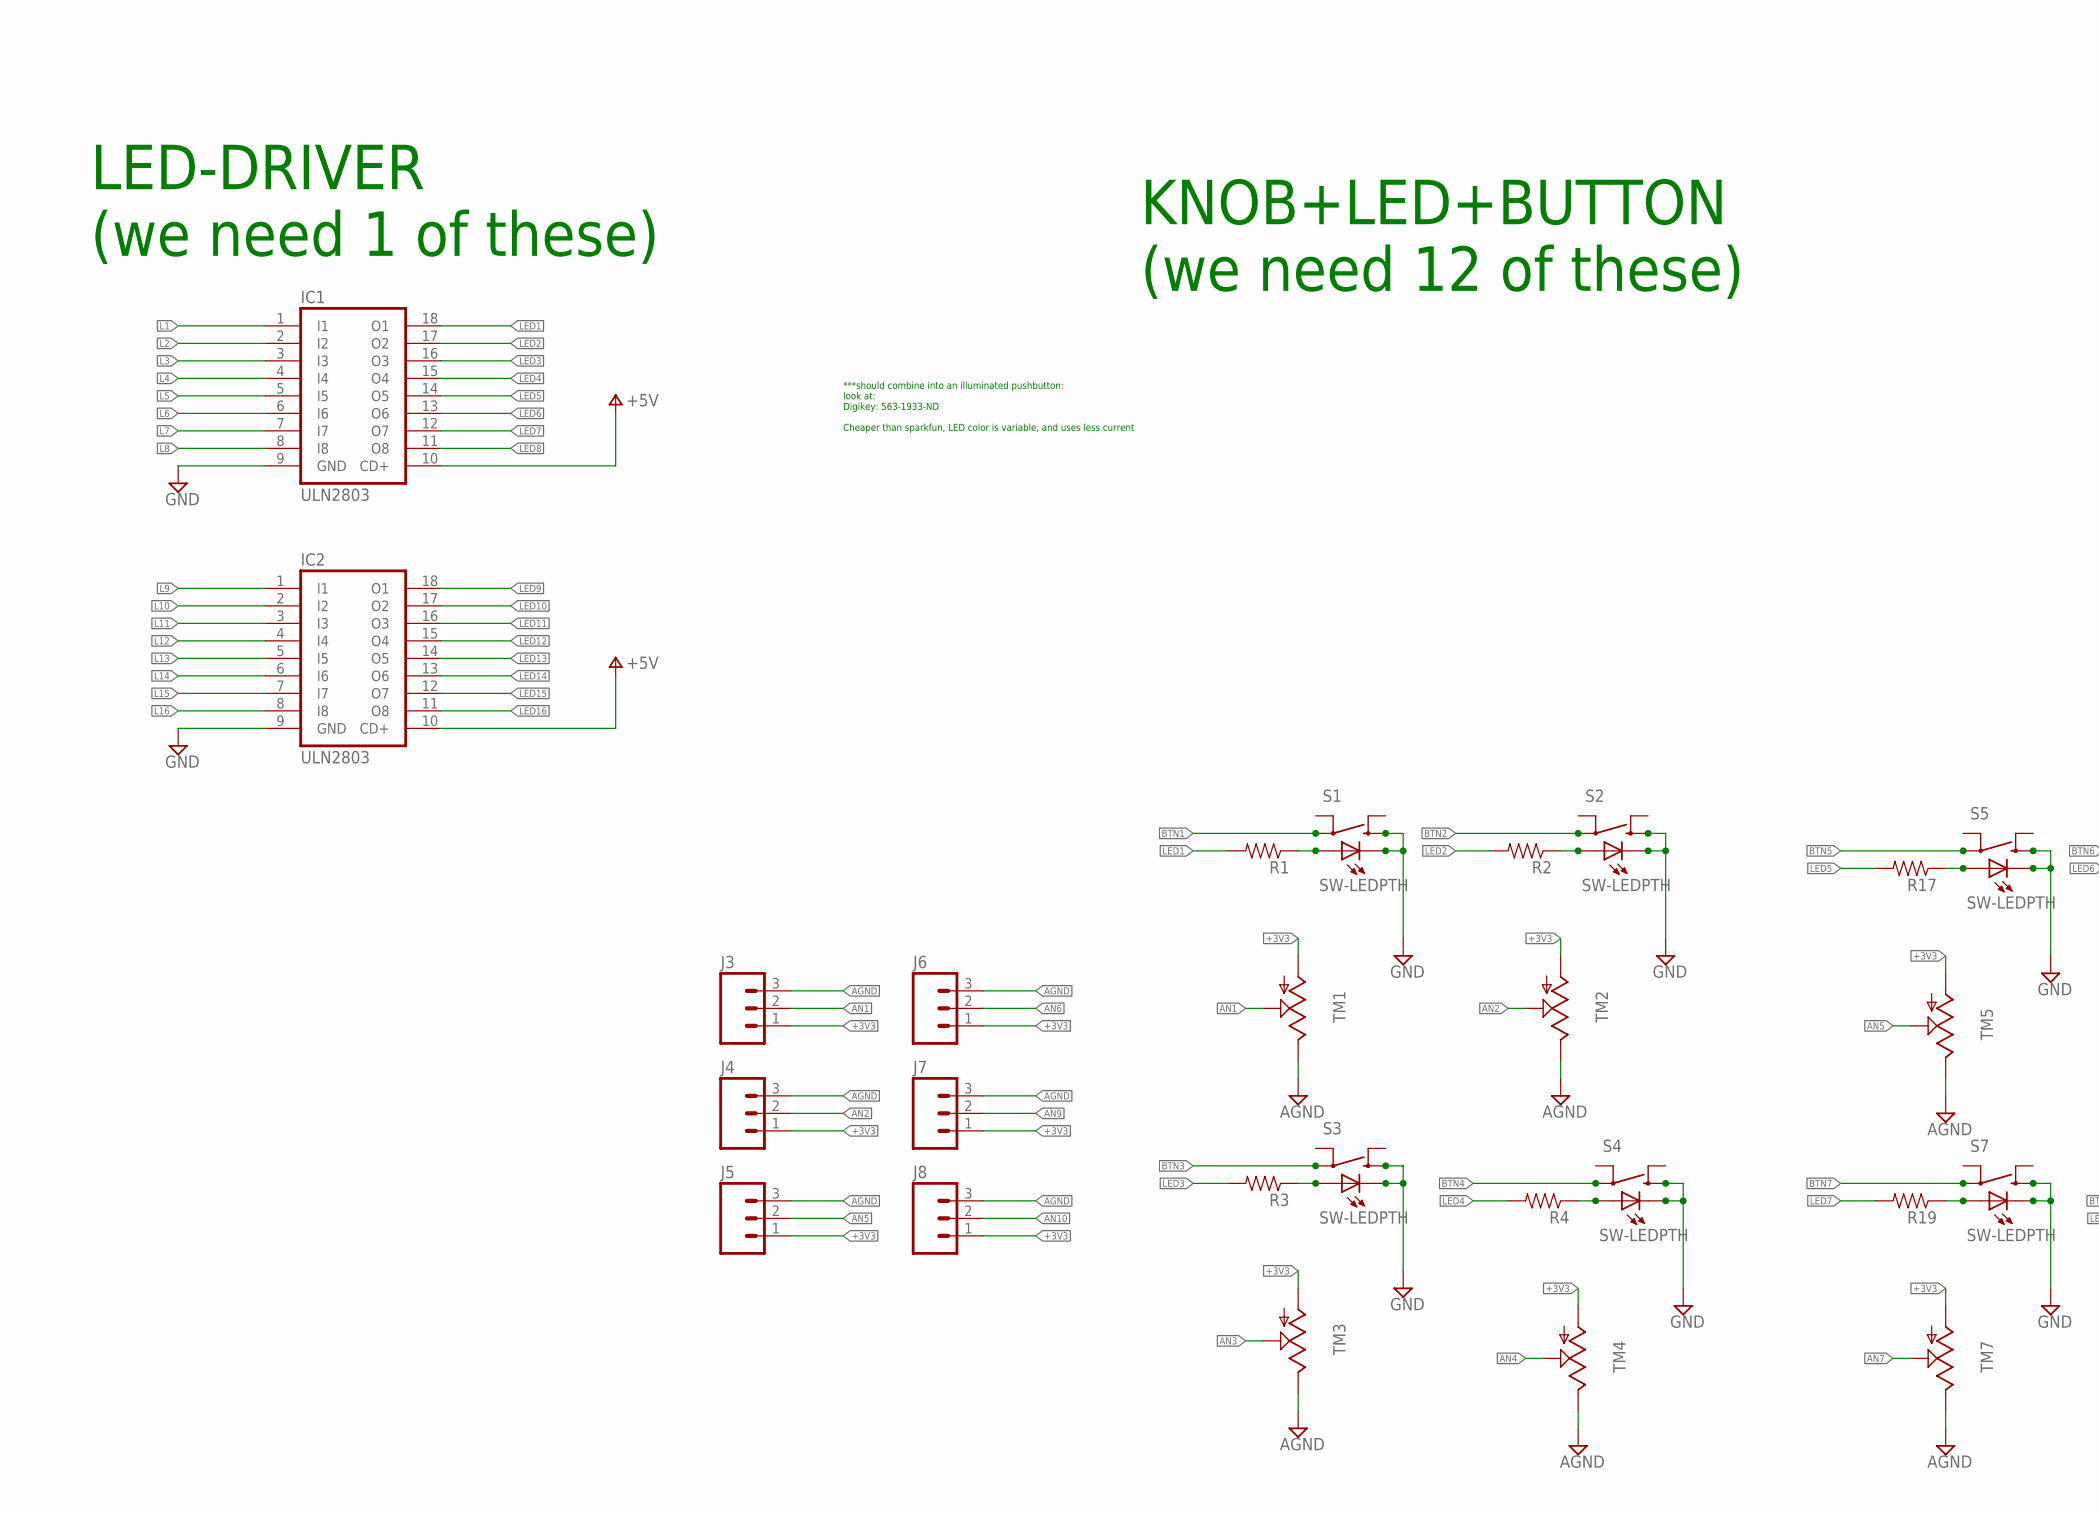
[picture p174: schematic MOD-v1.1.sch, part in row 2, column 1]

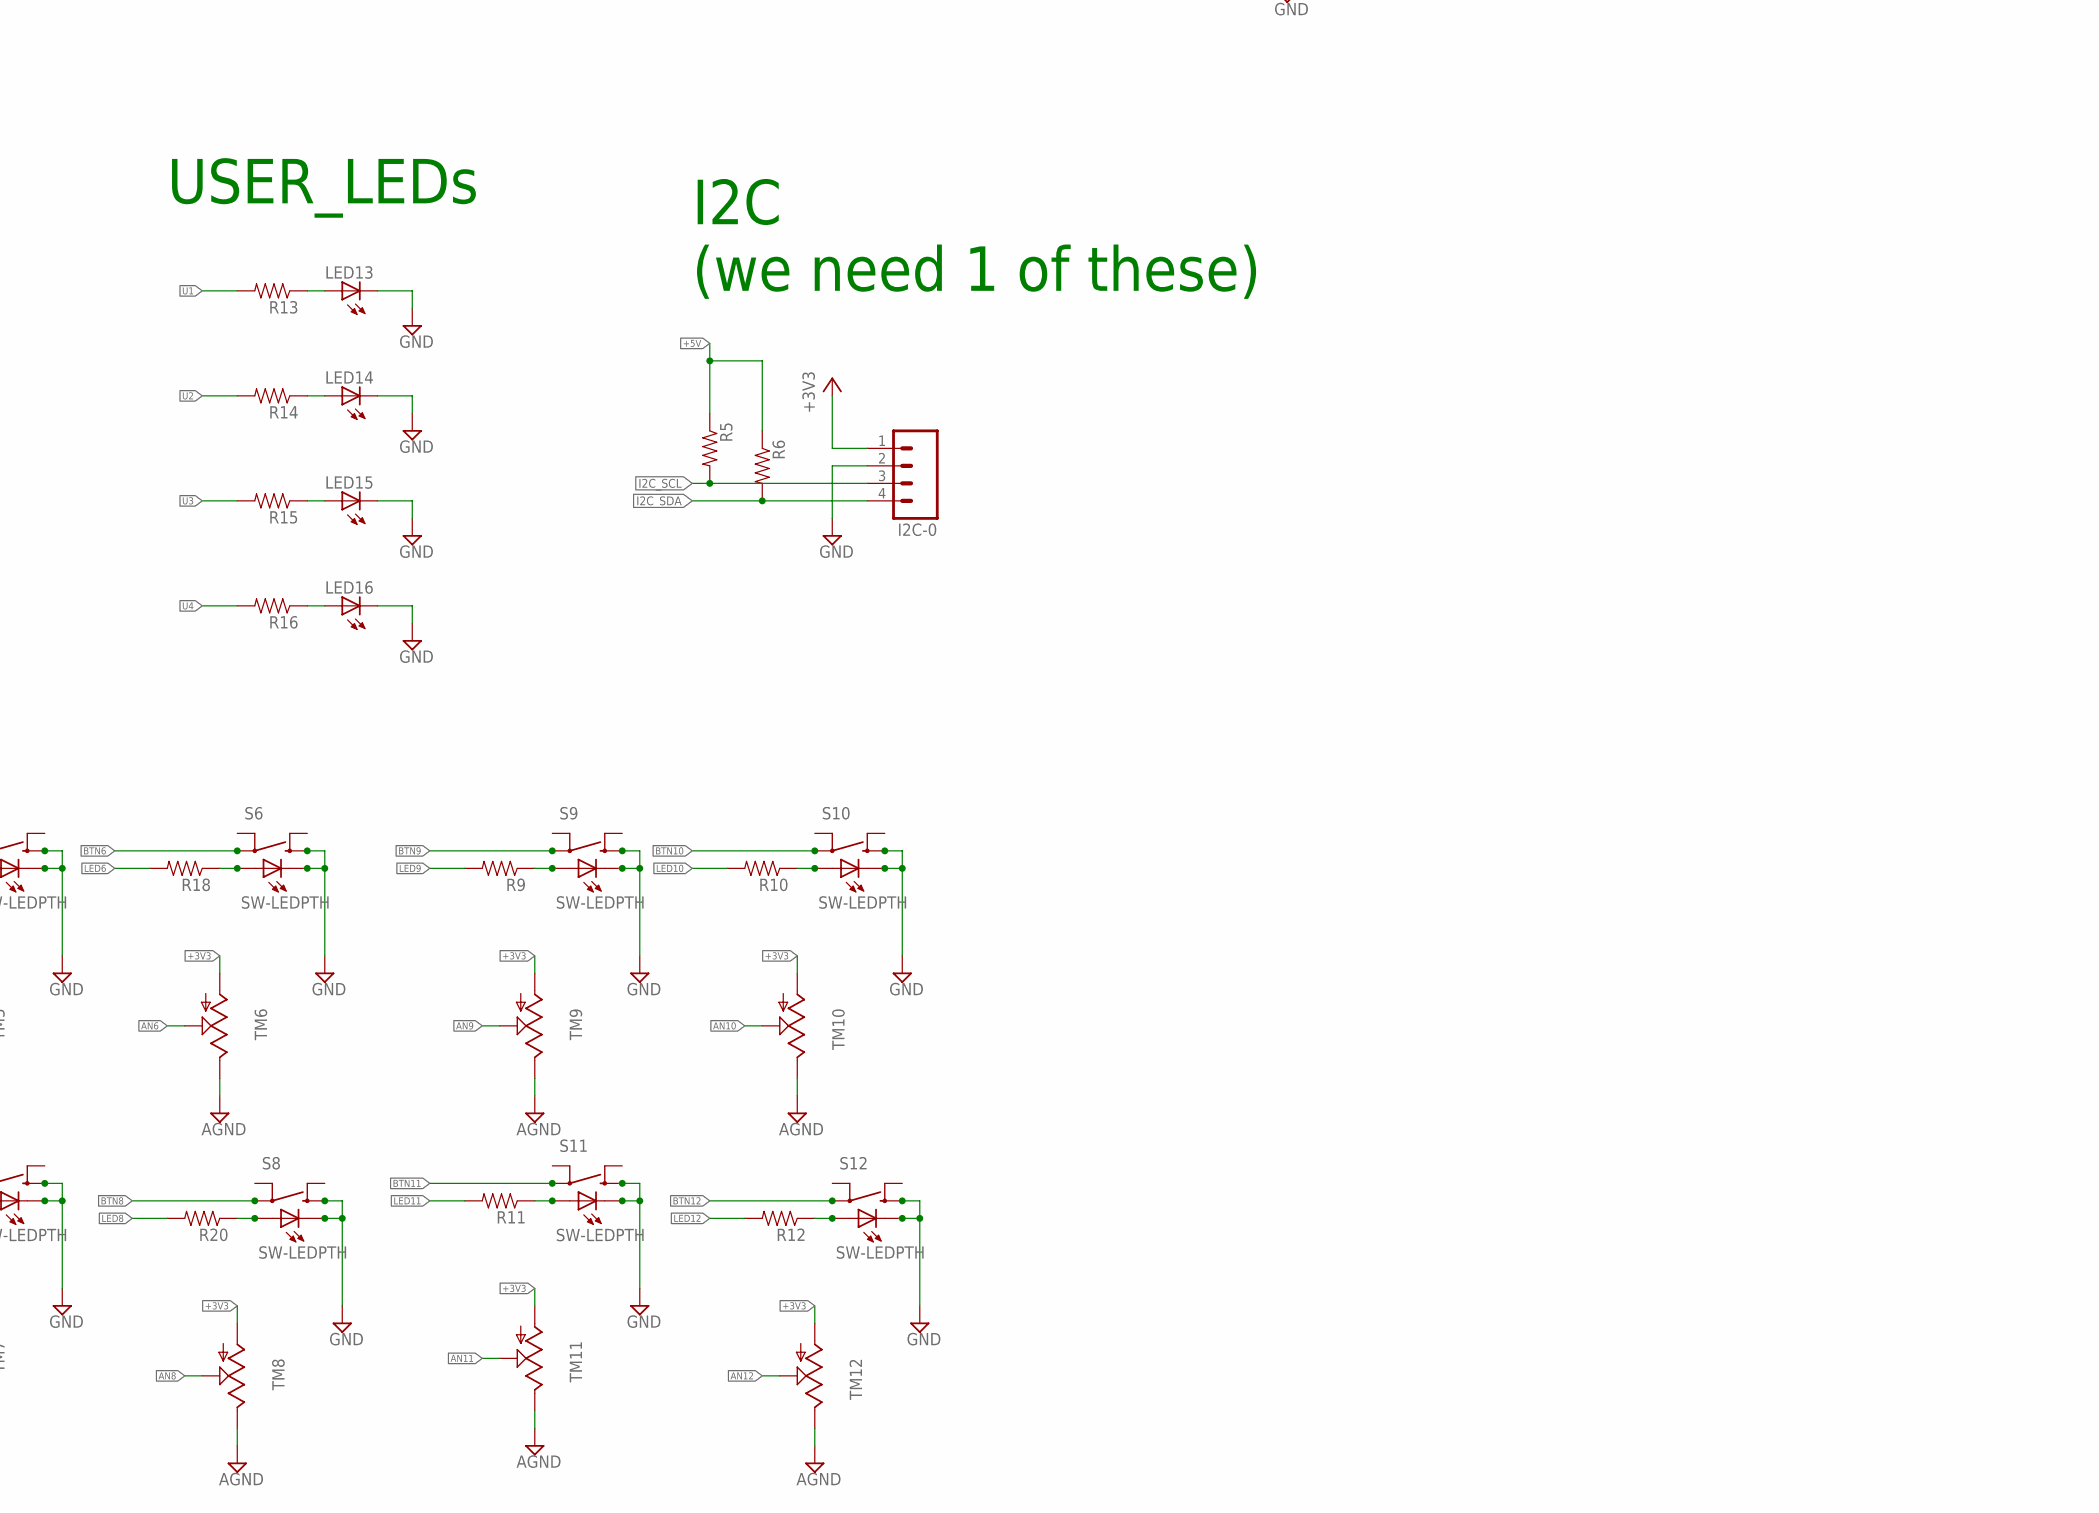
[picture p175: schematic MOD-v1.1.sch, part in row 2, column 2]

Parts:
GND-SHRT: M02LOCK; 1X02_LOCK
I2C-0: M04LOCK; 1X04_LOCK
IC1, IC2: ULN2803; DIL18
J1: SERVO 1; 1X03_LOCK@1
J2: SERVO 2; 1X03_LOCK@1
J3, J4, J5, J6, J7, J8: M031X03_NO_SILK; 1X03_NO_SILK
LED13, LED14, LED15, LED16: LED3MM
MOTORS1: M04; SPRINGTERMINAL-2.54MM-4
POWER-5V: DCBARRELPTH; DCJACK_2MM_PTH
R1, R2, R3, R4, R5, R6, R9, R10, R11, R12, R13, R14, R15, R16, R17, R18, R19, R20: RESISTOREZ; AXIAL-0.3EZ
S1, S2, S3, S4, S5, S6, S7, S8, S9, S10, S11, S12: SW-LEDPTH; TR2-SWITCH-MOMENTARY-LED
TEENSY: TEENSY3_6--ALLPINS; T36
TM1, TM2, TM3, TM4, TM5, TM6, TM7, TM8, TM9, TM10, TM11, TM12: TRIM; TRIM-PCB-9MM
U1: SN74LVC2G04DBV; SOT23-6
U2, U3: JOYSTICKPTH; JOYSTICK
U$7: POLOLU_TB6612FNG
VIN: M02LOCK; 1X02_LOCK
VOUT: M02LOCK; 1X02_LOCK

Connections:
+3V3: I2C-0.1, J3.1, J4.1, J5.1, J6.1, J7.1, J8.1, TEENSY.3V3(1) (3V3), TEENSY.3V3(2) (3V3), TEENSY.3V3(3) (3V3), TEENSY.3V3(4) (3V3), TM1.1 (A), TM2.1 (A), TM3.1 (A), TM4.1 (A), TM5.1 (A), TM6.1 (A), TM7.1 (A), TM8.1 (A), TM9.1 (A), TM10.1 (A), TM11.1 (A), TM12.1 (A), U1.5 (VCC), U2.H1 (H+), U2.V1 (V+), U3.H1 (H+), U3.V1 (V+), U$7.STBY, U$7.VCC
+5V: IC1.10 (CD+), IC2.10 (CD+), J1.2, J2.2, POWER-5V.PWR, R5.P$1 (1), R6.P$1 (1), VIN.1
AGND: J3.3, J4.3, J5.3, J6.3, J7.3, J8.3, TEENSY.AGND, TM1.3 (E), TM2.3 (E), TM3.3 (E), TM4.3 (E), TM5.3 (E), TM6.3 (E), TM7.3 (E), TM8.3 (E), TM9.3 (E), TM10.3 (E), TM11.3 (E), TM12.3 (E), U2.B2A (SEL-), U2.H3 (H-), U2.V3 (V-), U3.B2A (SEL-), U3.H3 (H-), U3.V3 (V-)
AN1: J3.2, TEENSY.14 (14/A0/PWM/ALT-SCK0), TM1.2 (S)
AN2: J4.2, TEENSY.15 (15/A1/CS0-4/T), TM2.2 (S)
AN3: TEENSY.16 (16/A2/PWM/T/ALT-SCL0), TM3.2 (S)
AN4: TEENSY.33 (33/A14/CAN1TX/TX5/ALT-SCL0), TM4.2 (S)
AN5: J5.2, TEENSY.34 (34/A15/CAN1RX/RX5/ALT-SDA0), TM5.2 (S)
AN6: J6.2, TEENSY.35 (35/A16/PWM), TM6.2 (S)
AN7: TEENSY.36 (36/A17/PWM), TM7.2 (S)
AN8: TEENSY.39 (39/A20/ALT-MISO0), TM8.2 (S)
AN9: J7.2, TEENSY.DAC0, TM9.2 (S)
AN10: J8.2, TEENSY.DAC1, TM10.2 (S)
AN11: TEENSY.A10, TM11.2 (S)
AN12: TEENSY.A11, TM12.2 (S)
BTN1: S1.3, TEENSY.11 (11/MOSI0)
BTN2: S2.3, TEENSY.12 (12/MISO0)
BTN3: S3.3, TEENSY.24
BTN4: S4.3, TEENSY.25
BTN5: S5.3, TEENSY.26 (26/ALT-PWM/ALT-TX1/ALT-SCL2)
BTN6: S6.3, TEENSY.27 (27/ALT-RX1/ALT-SCK0)
BTN7: S7.3, TEENSY.28 (28/ALT-MOSI0)
BTN8: S8.3, TEENSY.42
BTN9: S9.3, TEENSY.43 (43/CS2-0)
BTN10: S10.3, TEENSY.44 (44/MOSI2)
BTN11: S11.3, TEENSY.45 (45/CS0-5/MISO2)
BTN12: S12.3, TEENSY.46 (46/SCK2)
GND: GND-SHRT.2, I2C-0.2, IC1.9 (GND), IC2.9 (GND), J1.1, J2.1, LED13.K (C), LED14.K (C), LED15.K (C), LED16.K (C), S1.1, S1.C, S2.1, S2.C, S3.1, S3.C, S4.1, S4.C, S5.1, S5.C, S6.1, S6.C, S7.1, S7.C, S8.1, S8.C, S9.1, S9.C, S10.1, S10.C, S11.1, S11.C, S12.1, S12.C, TEENSY.G0 (GND), TEENSY.G1 (GND), TEENSY.G2 (GND), TEENSY.G3 (GND), TEENSY.G4 (GND), TEENSY.G5 (GND), TEENSY.G6 (GND), U1.2 (GND), U$7.GND, VIN.2, VOUT.1
GNDBREAK: POWER-5V.GNDBREAK
GND_MOT: GND-SHRT.1, POWER-5V.GND, U$7.GND1, U$7.GND2
I2C_SCL: I2C-0.3, R5.P$2 (2), TEENSY.47 (47/SCL0/RX6)
I2C_SDA: I2C-0.4, R6.P$2 (2), TEENSY.48 (48/SDA0/TX6)
JOY_AN_H_M: TEENSY.18 (18/A4/PWM/T/SDA0), U2.H2 (H)
JOY_AN_H_S: TEENSY.20 (20/A6/PWM/CS0-2/ALT-SCK1), U3.H2 (H)
JOY_AN_V_M: TEENSY.17 (17/A3/PWM/T/ALT-SDA0), U2.V2 (V)
JOY_AN_V_S: TEENSY.19 (19/A5/PWM/T/SCL0), U3.V2 (V)
JOY_BTN_M: TEENSY.0 (0/RX1/MOSI1/T), U2.B1A (SEL+)
JOY_BTN_S: TEENSY.1 (1/TX1/MISO1/T), U3.B1A (SEL+)
L1: IC1.1 (I1), TEENSY.2 (2/PWM)
L2: IC1.2 (I2), TEENSY.3 (3/PWM/SCL2/CAN0TX)
L3: IC1.3 (I3), TEENSY.4 (4/PWM/SDA2/CAN0RX)
L4: IC1.4 (I4), TEENSY.5 (5/PWM/ALT-TX1/ALT-MISO1)
L5: IC1.5 (I5), TEENSY.6 (6/PWM)
L6: IC1.6 (I6), TEENSY.7 (7/PWM/RX3/ALT-SCL0/ALT-MOSI0)
L7: IC1.7 (I7), TEENSY.8 (8/PWM/TX3/ALT-SDA0/ALT-MISO0)
L8: IC1.8 (I8), TEENSY.23 (23/A9/PWM/T)
L9: IC2.1 (I1), TEENSY.29 (29/PWM/T/ALT-CAN0TX)
L10: IC2.2 (I2), TEENSY.30 (30/PWM/T/ALT-CAN0RX)
L11: IC2.3 (I3), TEENSY.31 (31/A12/PWM/RX4/CS1-0)
L12: IC2.4 (I4), TEENSY.32 (32/A13/PWM/TX4/SCK1)
L13: IC2.5 (I5)
L14: IC2.6 (I6)
L15: IC2.7 (I7)
L16: IC2.8 (I8)
LED1: IC1.18 (O1), R1.P$2 (2)
LED2: IC1.17 (O2), R2.P$2 (2)
LED3: IC1.16 (O3), R3.P$2 (2)
LED4: IC1.15 (O4), R4.P$2 (2)
LED5: IC1.14 (O5), R17.P$2 (2)
LED6: IC1.13 (O6), R18.P$2 (2)
LED7: IC1.12 (O7), R19.P$2 (2)
LED8: IC1.11 (O8), R20.P$2 (2)
LED9: IC2.18 (O1), R9.P$2 (2)
LED10: IC2.17 (O2), R10.P$2 (2)
LED11: IC2.16 (O3), R11.P$2 (2)
LED12: IC2.15 (O4), R12.P$2 (2)
LED13: IC2.14 (O5)
LED14: IC2.13 (O6)
LED15: IC2.12 (O7)
LED16: IC2.11 (O8)
M_A_IN: TEENSY.40, U1.3 (2A), U$7.AIN1
M_B_IN: TEENSY.41, U1.1 (1A), U$7.BIN2
M_PWM_A: TEENSY.21 (21/A7/PWM/CS0-3/ALT-MOSI1/ALT-RX1), U$7.PWMA
M_PWM_B: TEENSY.22 (22/A8/PWM/T), U$7.PWMB
unnamed: R1.P$1 (1), S1.A
unnamed: LED13.A, R13.P$1 (1)
unnamed: LED14.A, R14.P$1 (1)
unnamed: LED15.A, R15.P$1 (1)
unnamed: U1.6 (1Y), U$7.BIN1
unnamed: U1.4 (2Y), U$7.AIN2
unnamed: LED16.A, R16.P$1 (1)
unnamed: R2.P$1 (1), S2.A
unnamed: R3.P$1 (1), S3.A
unnamed: R4.P$1 (1), S4.A
unnamed: R9.P$1 (1), S9.A
unnamed: R10.P$1 (1), S10.A
unnamed: R11.P$1 (1), S11.A
unnamed: R12.P$1 (1), S12.A
unnamed: R17.P$1 (1), S5.A
unnamed: R18.P$1 (1), S6.A
unnamed: R19.P$1 (1), S7.A
unnamed: R20.P$1 (1), S8.A
unnamed: MOTORS1.P$1 (1), U$7.BO1
unnamed: MOTORS1.P$2 (2), U$7.BO2
unnamed: MOTORS1.P$3 (3), U$7.AO2
unnamed: MOTORS1.P$4 (4), U$7.AO1
S1: J1.3, TEENSY.9 (9/PWM/RX2/CS0-1)
S2: J2.3, TEENSY.10 (10/PWM/TX2/CS0-0)
U1: R13.P$2 (2), TEENSY.51 (51/MISO2)
U2: R14.P$2 (2), TEENSY.52 (52/MOSI2)
U3: R15.P$2 (2), TEENSY.53 (53/PWM/SCK2)
U4: R16.P$2 (2), TEENSY.54 (54/CS2-1)
VMOT: U$7.VMOT, VOUT.2

Notes on the sheet:
***should combine into an illuminated pushbutton: look at: Digikey: 563-1933-ND Cheaper than sparkfun, LED color is variable, and uses less current
KNOB+LED+BUTTON (we need 12 of these)
MOTOR-DRIVER+JOYSTICK (we need 1 of these)
***CHANGE to the beefier STEP-UP from Amazon: https://www.amazon.com/gp/product/B01KFH32YI/ref=oh_aui_detailpage_o01_s00?ie=UTF8&psc=1 This is better than the smaller one we found because it has a built in voltage meter
POWER
SERVO+JOYSTICK (we need 1 of these)
LED-DRIVER (we need 1 of these)
USER_LEDs
I2C (we need 1 of these)
I2C
TEENSY 3.6

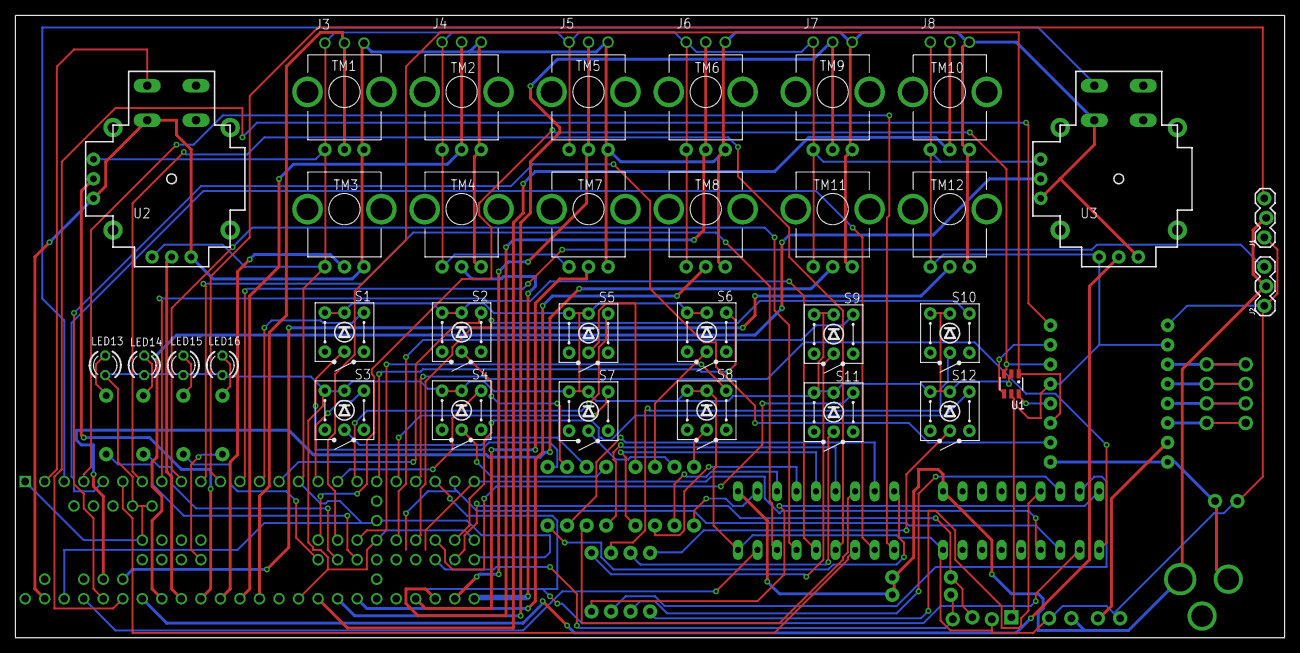
[picture p176: board MOD-v1.1.brd from above]

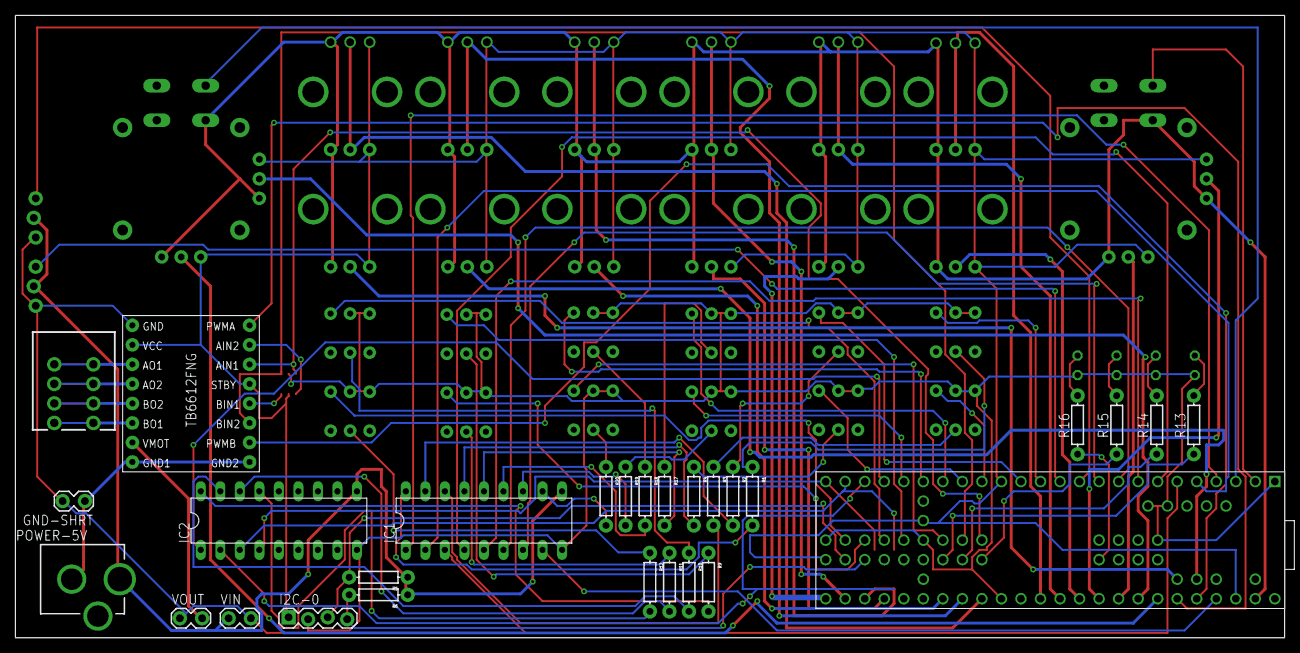
[picture p177: board MOD-v1.1.brd from below]

Board: 2 copper layers, 165.1 x 81.0 mm, 67 parts (28 on the bottom side), 94 nets.
