batchku/MO/PCBs/MO/_archive/MOD-v2-1_MOD-Strips.brd

## EAGLE design PCBs/MO/_archive/MOD-v2-1_MOD-Strips.brd (2017-07-26, an earlier design)

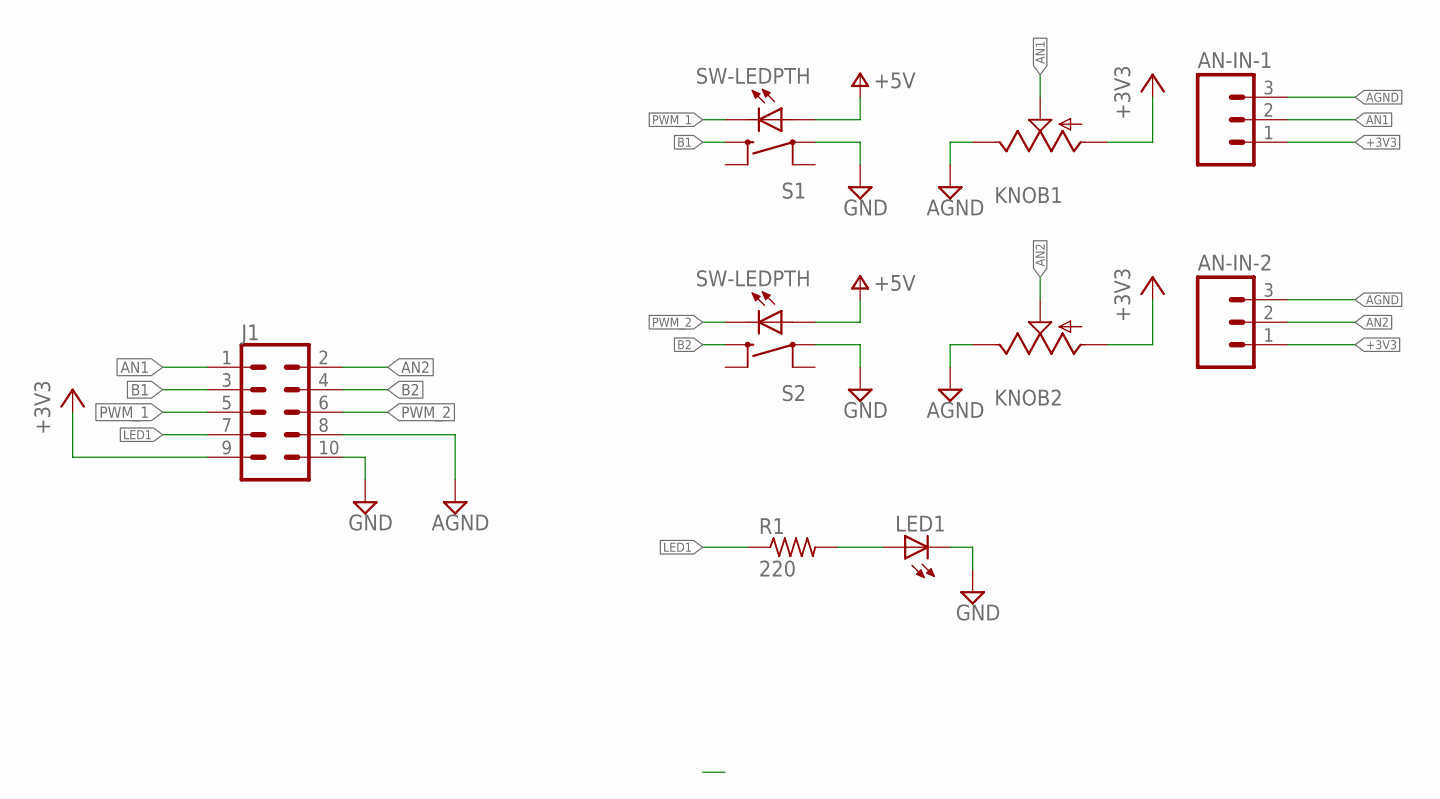
[picture p179: schematic MOD-v2-1_MOD-Strips.sch]

Parts:
AN-IN-1, AN-IN-2: M031X03_NO_SILK; 1X03_NO_SILK
J1: CONN_05X2SHD_LOCK; 2X5-SHROUDED_LOCK
KNOB1, KNOB2: TRIM; TRIM-PCB-9MM
LED1: LED3MM
R1: 220; 0204/7
S1, S2: SW-LEDPTH; TR2-SWITCH-MOMENTARY-LED

Connections:
+3V3: AN-IN-1.1, AN-IN-2.1, J1.9, KNOB1.1 (A), KNOB2.1 (A)
AGND: AN-IN-1.3, AN-IN-2.3, J1.8, KNOB1.3 (E), KNOB2.3 (E)
AN1: AN-IN-1.2, J1.1, KNOB1.2 (S)
AN2: AN-IN-2.2, J1.2, KNOB2.2 (S)
B1: J1.3, S1.1
B2: J1.4, S2.1
GND: J1.10, LED1.K (C), S1.3, S2.3
LED1: J1.7, R1.1
N1: LED1.A, R1.2
PWM_1: J1.5, S1.C
PWM_2: J1.6, S2.C
V+: S1.A, S2.A

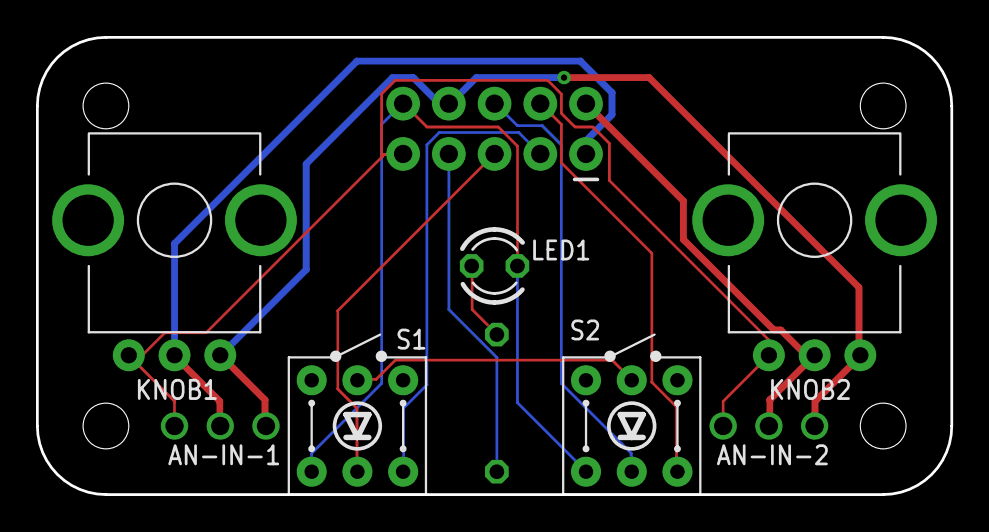
[picture p180: board MOD-v2-1_MOD-Strips.brd from above]

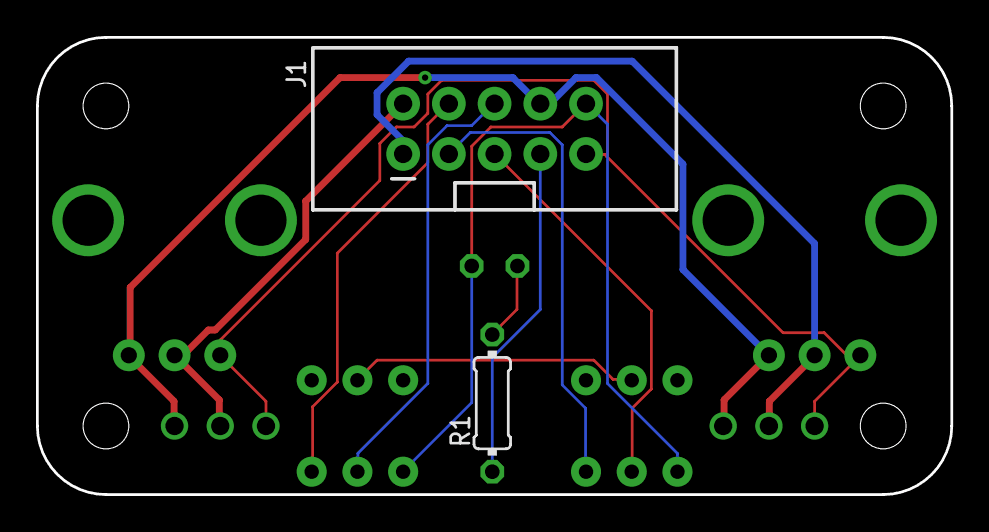
[picture p181: board MOD-v2-1_MOD-Strips.brd from below]

Board: 2 copper layers, 50.8 x 25.4 mm, 9 parts (2 on the bottom side), 12 nets.
