batchku/MO/PCBs/MOM/MOM_LED-out_v04.brd

## EAGLE design PCBs/MOM/MOM_LED-out_v04.brd (2017-07-26)

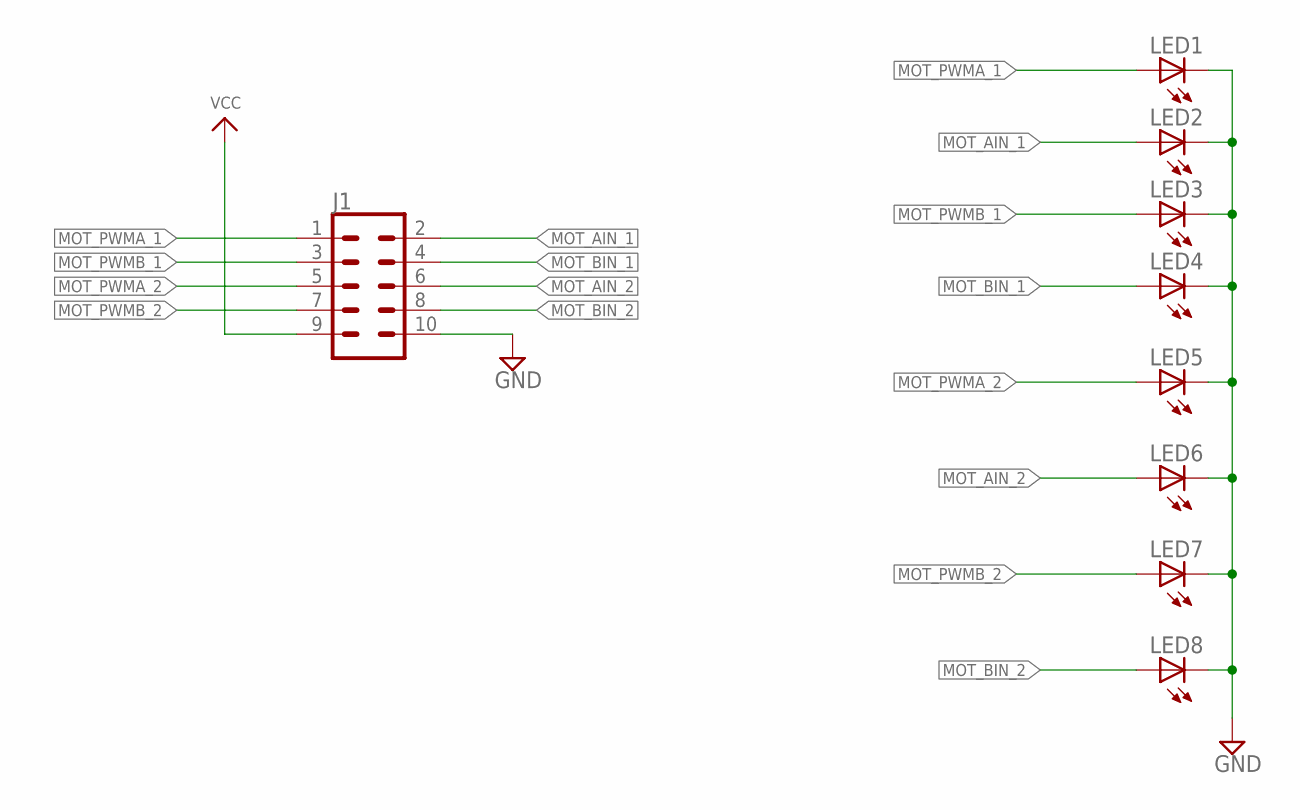
[picture p182: schematic MOM_LED-out_v04.sch]

Parts:
J1: CONN_05X2SHD_LOCK; 2X5-SHROUDED_LOCK
LED1, LED2, LED3, LED4, LED5, LED6, LED7, LED8: LED5MM

Connections:
GND: J1.10, LED1.K (C), LED2.K (C), LED3.K (C), LED4.K (C), LED5.K (C), LED6.K (C), LED7.K (C), LED8.K (C)
MOT_AIN_1: J1.2, LED2.A
MOT_AIN_2: J1.6, LED6.A
MOT_BIN_1: J1.4, LED4.A
MOT_BIN_2: J1.8, LED8.A
MOT_PWMA_1: J1.1, LED1.A
MOT_PWMA_2: J1.5, LED5.A
MOT_PWMB_1: J1.3, LED3.A
MOT_PWMB_2: J1.7, LED7.A
VCC: J1.9

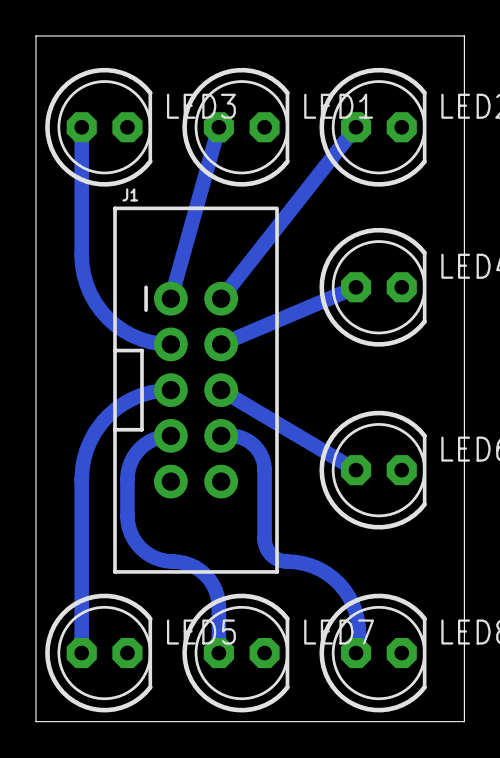
[picture p183: board MOM_LED-out_v04.brd from above]

Board: 2 copper layers, 23.8 x 38.1 mm, 9 parts (0 on the bottom side), 9 nets.
