batchku/MO/PCBs/MOM/MOM_analog-inputs_v04.brd

## EAGLE design PCBs/MOM/MOM_analog-inputs_v04.brd (2017-07-26)

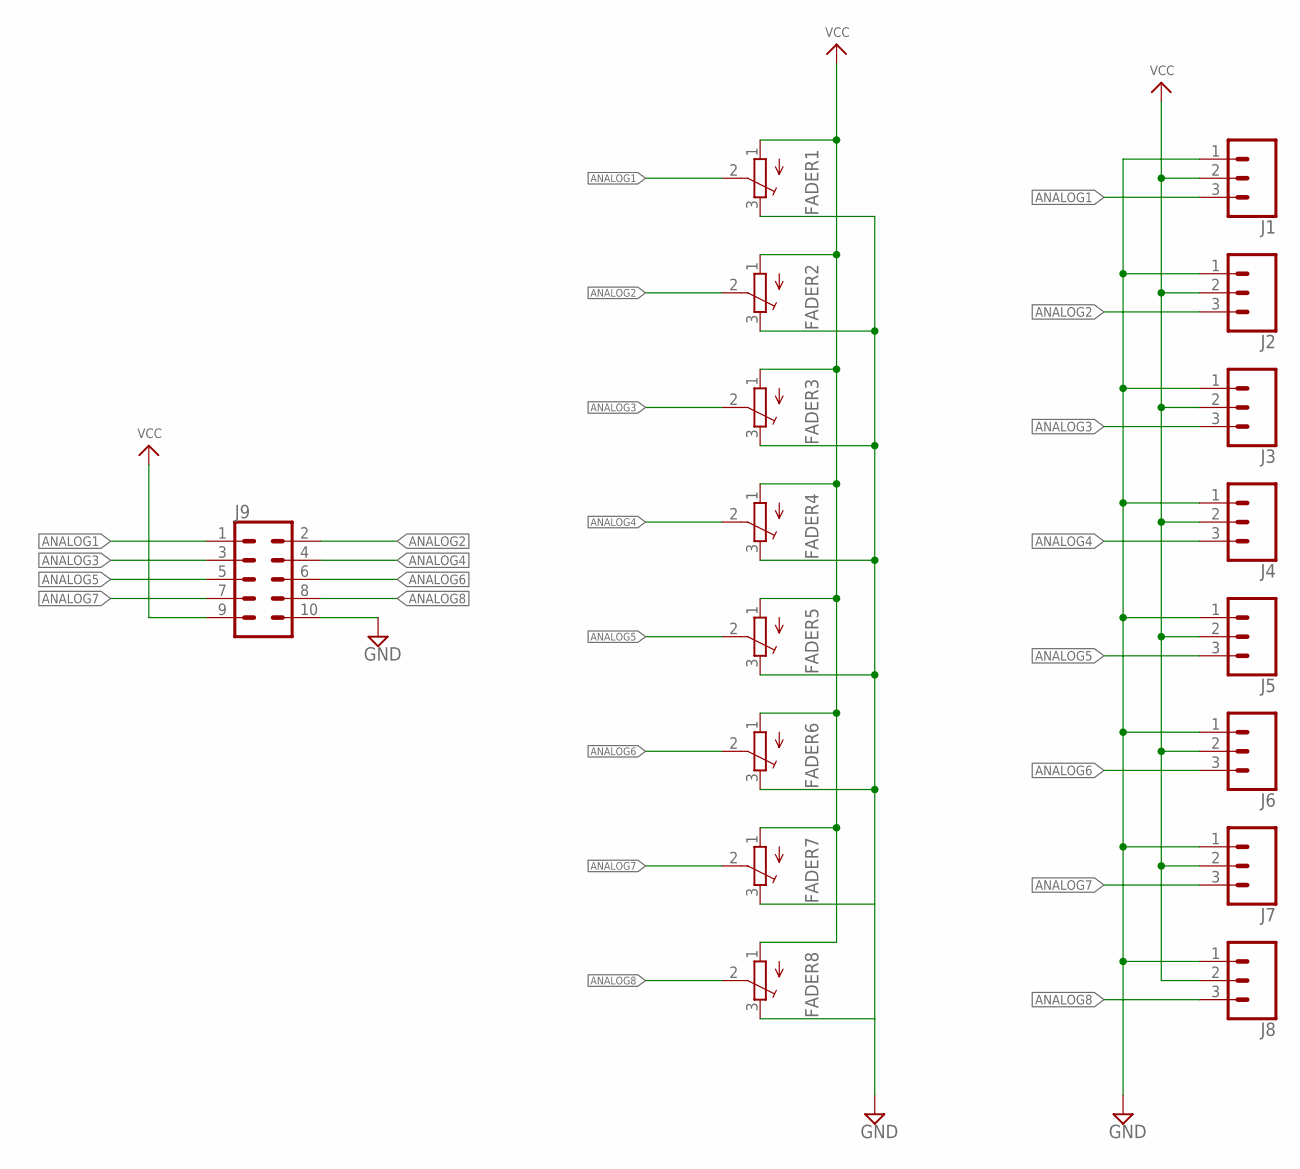
[picture p184: schematic MOM_analog-inputs_v04.sch]

Parts:
FADER1, FADER2, FADER3, FADER4, FADER5, FADER6, FADER7, FADER8: TRIMPOT3386; TRIM-3386
J1, J2, J3, J4, J5, J6, J7, J8: CONN_03LOCK; 1X03_LOCK
J9: CONN_05X2SHD_LOCK; 2X5-SHROUDED_LOCK

Connections:
ANALOG1: FADER1.2 (S), J1.3, J9.1
ANALOG2: FADER2.2 (S), J2.3, J9.2
ANALOG3: FADER3.2 (S), J3.3, J9.3
ANALOG4: FADER4.2 (S), J4.3, J9.4
ANALOG5: FADER5.2 (S), J5.3, J9.5
ANALOG6: FADER6.2 (S), J6.3, J9.6
ANALOG7: FADER7.2 (S), J7.3, J9.7
ANALOG8: FADER8.2 (S), J8.3, J9.8
GND: FADER1.3 (E), FADER2.3 (E), FADER3.3 (E), FADER4.3 (E), FADER5.3 (E), FADER6.3 (E), FADER7.3 (E), FADER8.3 (E), J1.1, J2.1, J3.1, J4.1, J5.1, J6.1, J7.1, J8.1, J9.10
VCC: FADER1.1 (A), FADER2.1 (A), FADER3.1 (A), FADER4.1 (A), FADER5.1 (A), FADER6.1 (A), FADER7.1 (A), FADER8.1 (A), J1.2, J2.2, J3.2, J4.2, J5.2, J6.2, J7.2, J8.2, J9.9

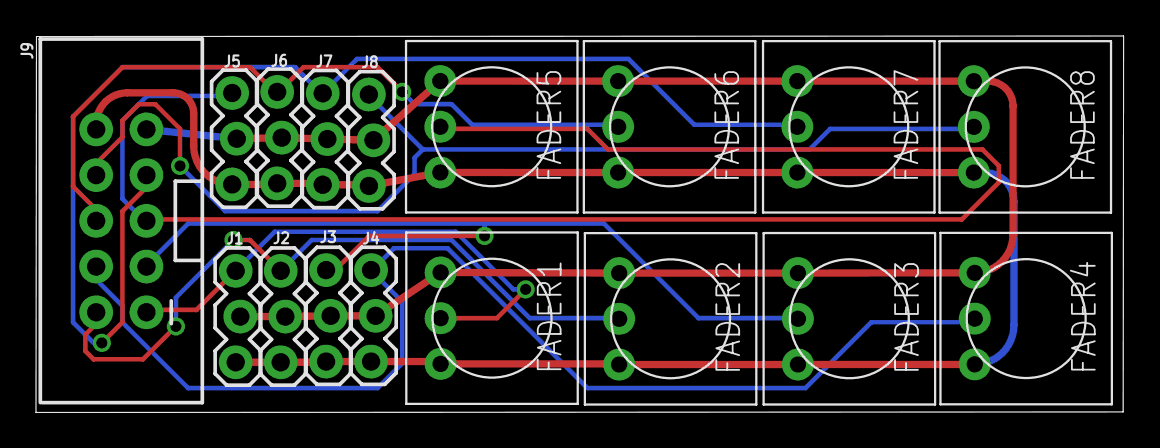
[picture p185: board MOM_analog-inputs_v04.brd from above]

Board: 2 copper layers, 60.4 x 20.9 mm, 17 parts (0 on the bottom side), 10 nets.
