batchku/MO/PCBs/MOM/MOM_buttons-in-LED-out_v04.brd

## EAGLE design PCBs/MOM/MOM_buttons-in-LED-out_v04.brd (2017-07-26)

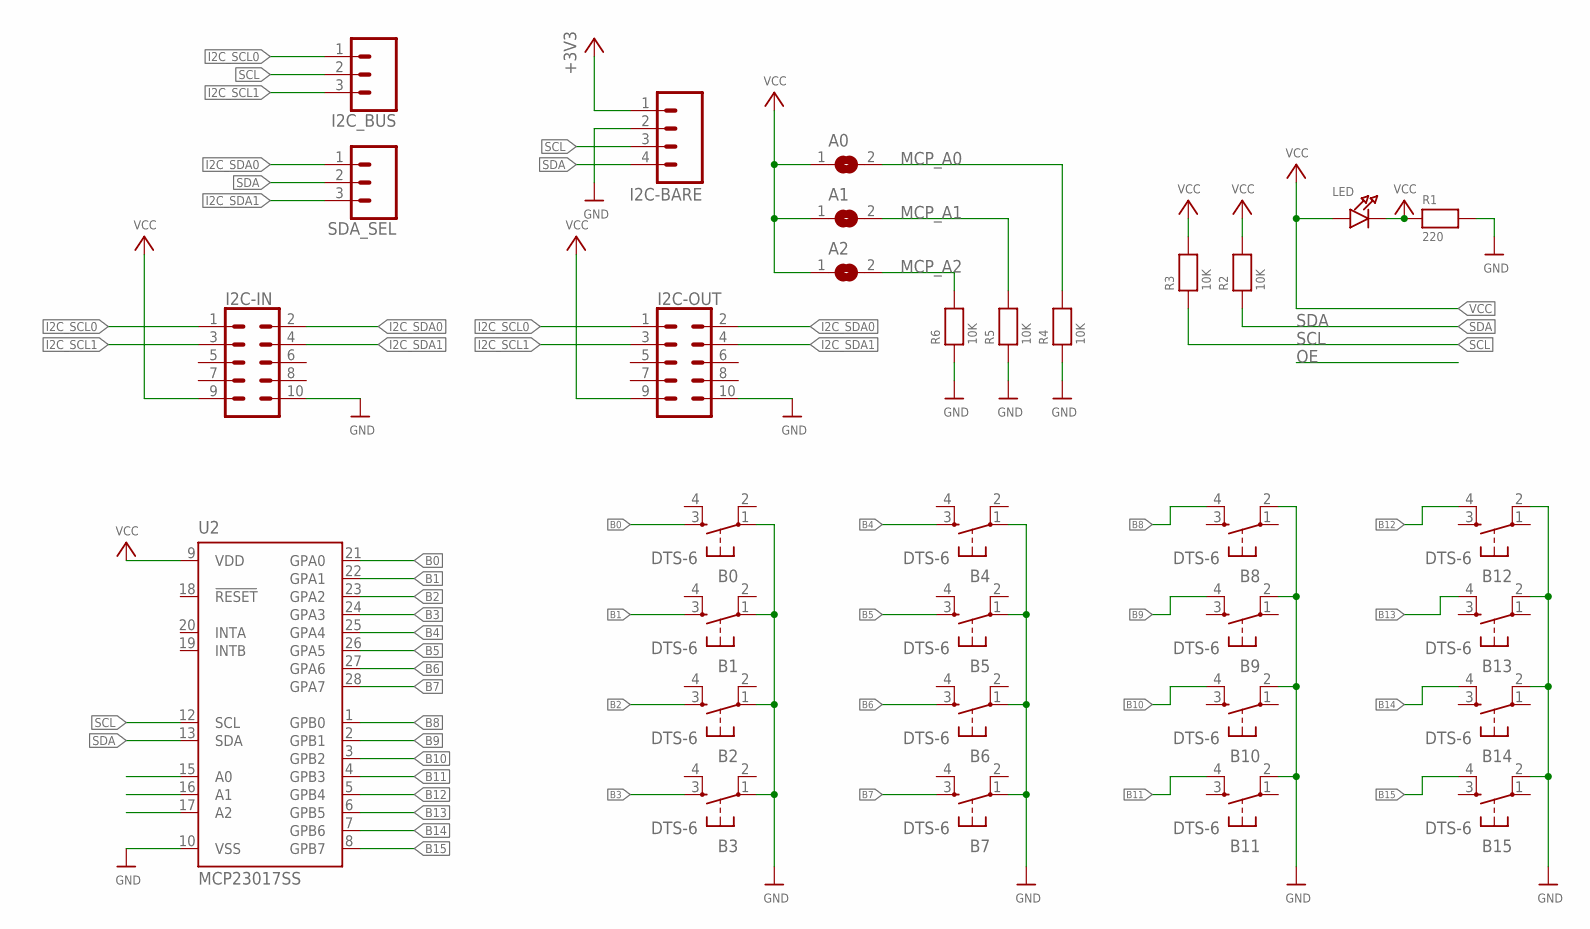
[picture p186: schematic MOM_buttons-in-LED-out_v04.sch]

Parts:
A0, A1, A2: SOLDERJUMPERREFLOW_NOPASTE; SOLDERJUMPER_REFLOW_NOPASTE
B0, B1, B2, B3, B4, B5, B6, B7, B8, B9, B10, B11, B12, B13, B14, B15: DTS-6
I2C-BARE: M04LOCK; 1X04_LOCK
I2C-IN, I2C-OUT: CONN_05X2SHD_LOCK; 2X5-SHROUDED_LOCK
I2C_BUS: CONN_03LOCK; 1X03_LOCK
LED: LED0805; CHIPLED_0805
R1: 220; 0805
R2, R3, R4, R5, R6: 10K; 0805
SDA_SEL: CONN_03LOCK; 1X03_LOCK
U2: MCP23017SS; SSOP28

Connections:
+3V3: I2C-BARE.1
B0: B0.3, U2.21 (GPA0)
B1: B1.3, U2.22 (GPA1)
B2: B2.3, U2.23 (GPA2)
B3: B3.3, U2.24 (GPA3)
B4: B4.3, U2.25 (GPA4)
B5: B5.3, U2.26 (GPA5)
B6: B6.3, U2.27 (GPA6)
B7: B7.3, U2.28 (GPA7)
B8: B8.4, U2.1 (GPB0)
B9: B9.4, U2.2 (GPB1)
B10: B10.4, U2.3 (GPB2)
B11: B11.4, U2.4 (GPB3)
B12: B12.4, U2.5 (GPB4)
B13: B13.4, U2.6 (GPB5)
B14: B14.4, U2.7 (GPB6)
B15: B15.4, U2.8 (GPB7)
GND: B0.1, B1.1, B2.1, B3.1, B4.1, B5.1, B6.1, B7.1, B8.2, B9.2, B10.2, B11.2, B12.2, B13.2, B14.2, B15.2, I2C-BARE.2, I2C-IN.10, I2C-OUT.10, R1.2, R4.1, R5.1, R6.1, U2.10 (VSS)
I2C_SCL0: I2C-IN.1, I2C-OUT.1, I2C_BUS.1
I2C_SCL1: I2C-IN.3, I2C-OUT.3, I2C_BUS.3
I2C_SDA0: I2C-IN.2, I2C-OUT.2, SDA_SEL.1
I2C_SDA1: I2C-IN.4, I2C-OUT.4, SDA_SEL.3
MCP_A0: A0.2, R4.2, U2.15 (A0)
MCP_A1: A1.2, R5.2, U2.16 (A1)
MCP_A2: A2.2, R6.2, U2.17 (A2)
unnamed: LED.C, R1.1
SCL: I2C-BARE.3, I2C_BUS.2, R3.1, U2.12 (SCL)
SDA: I2C-BARE.4, R2.1, SDA_SEL.2, U2.13 (SDA)
VCC: A0.1, A1.1, A2.1, I2C-IN.9, I2C-OUT.9, LED.A, R2.2, R3.2, U2.9 (VDD)

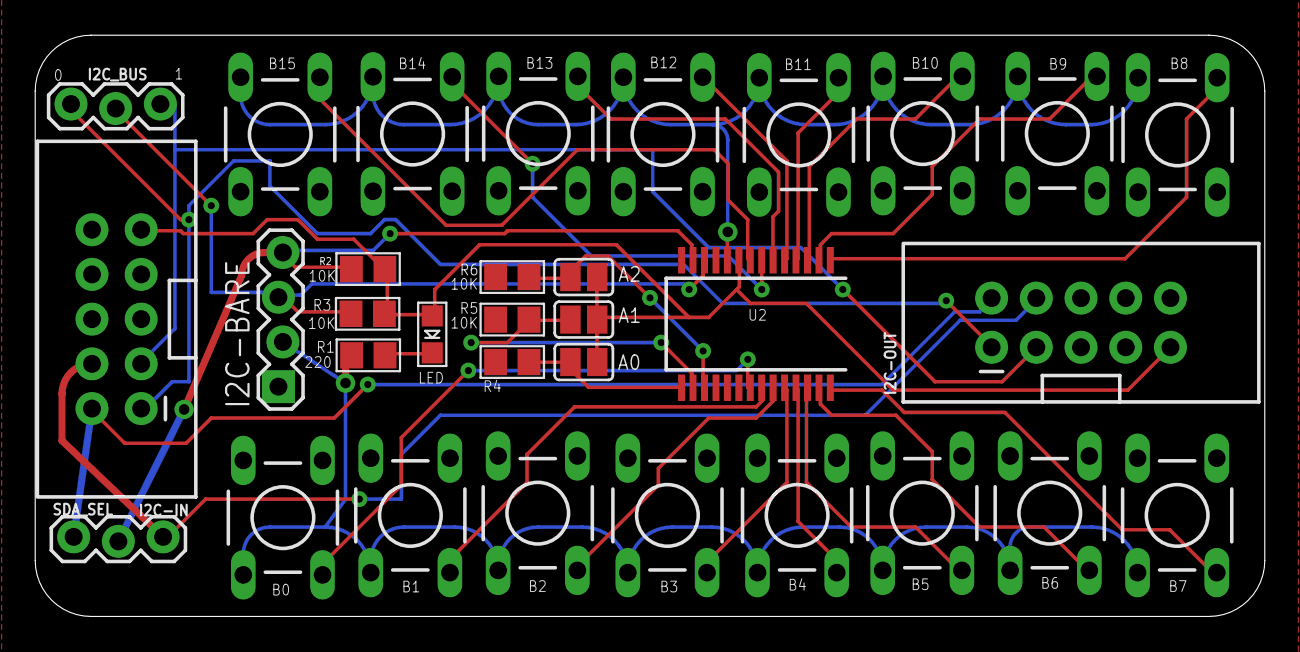
[picture p187: board MOM_buttons-in-LED-out_v04.brd from above]

Board: 2 copper layers, 69.8 x 33.0 mm, 32 parts (0 on the bottom side), 28 nets.
