batchku/MO/PCBs/MOM/MOM_teensy-breakout_v04.brd

## EAGLE design PCBs/MOM/MOM_teensy-breakout_v04.brd (2017-07-26)

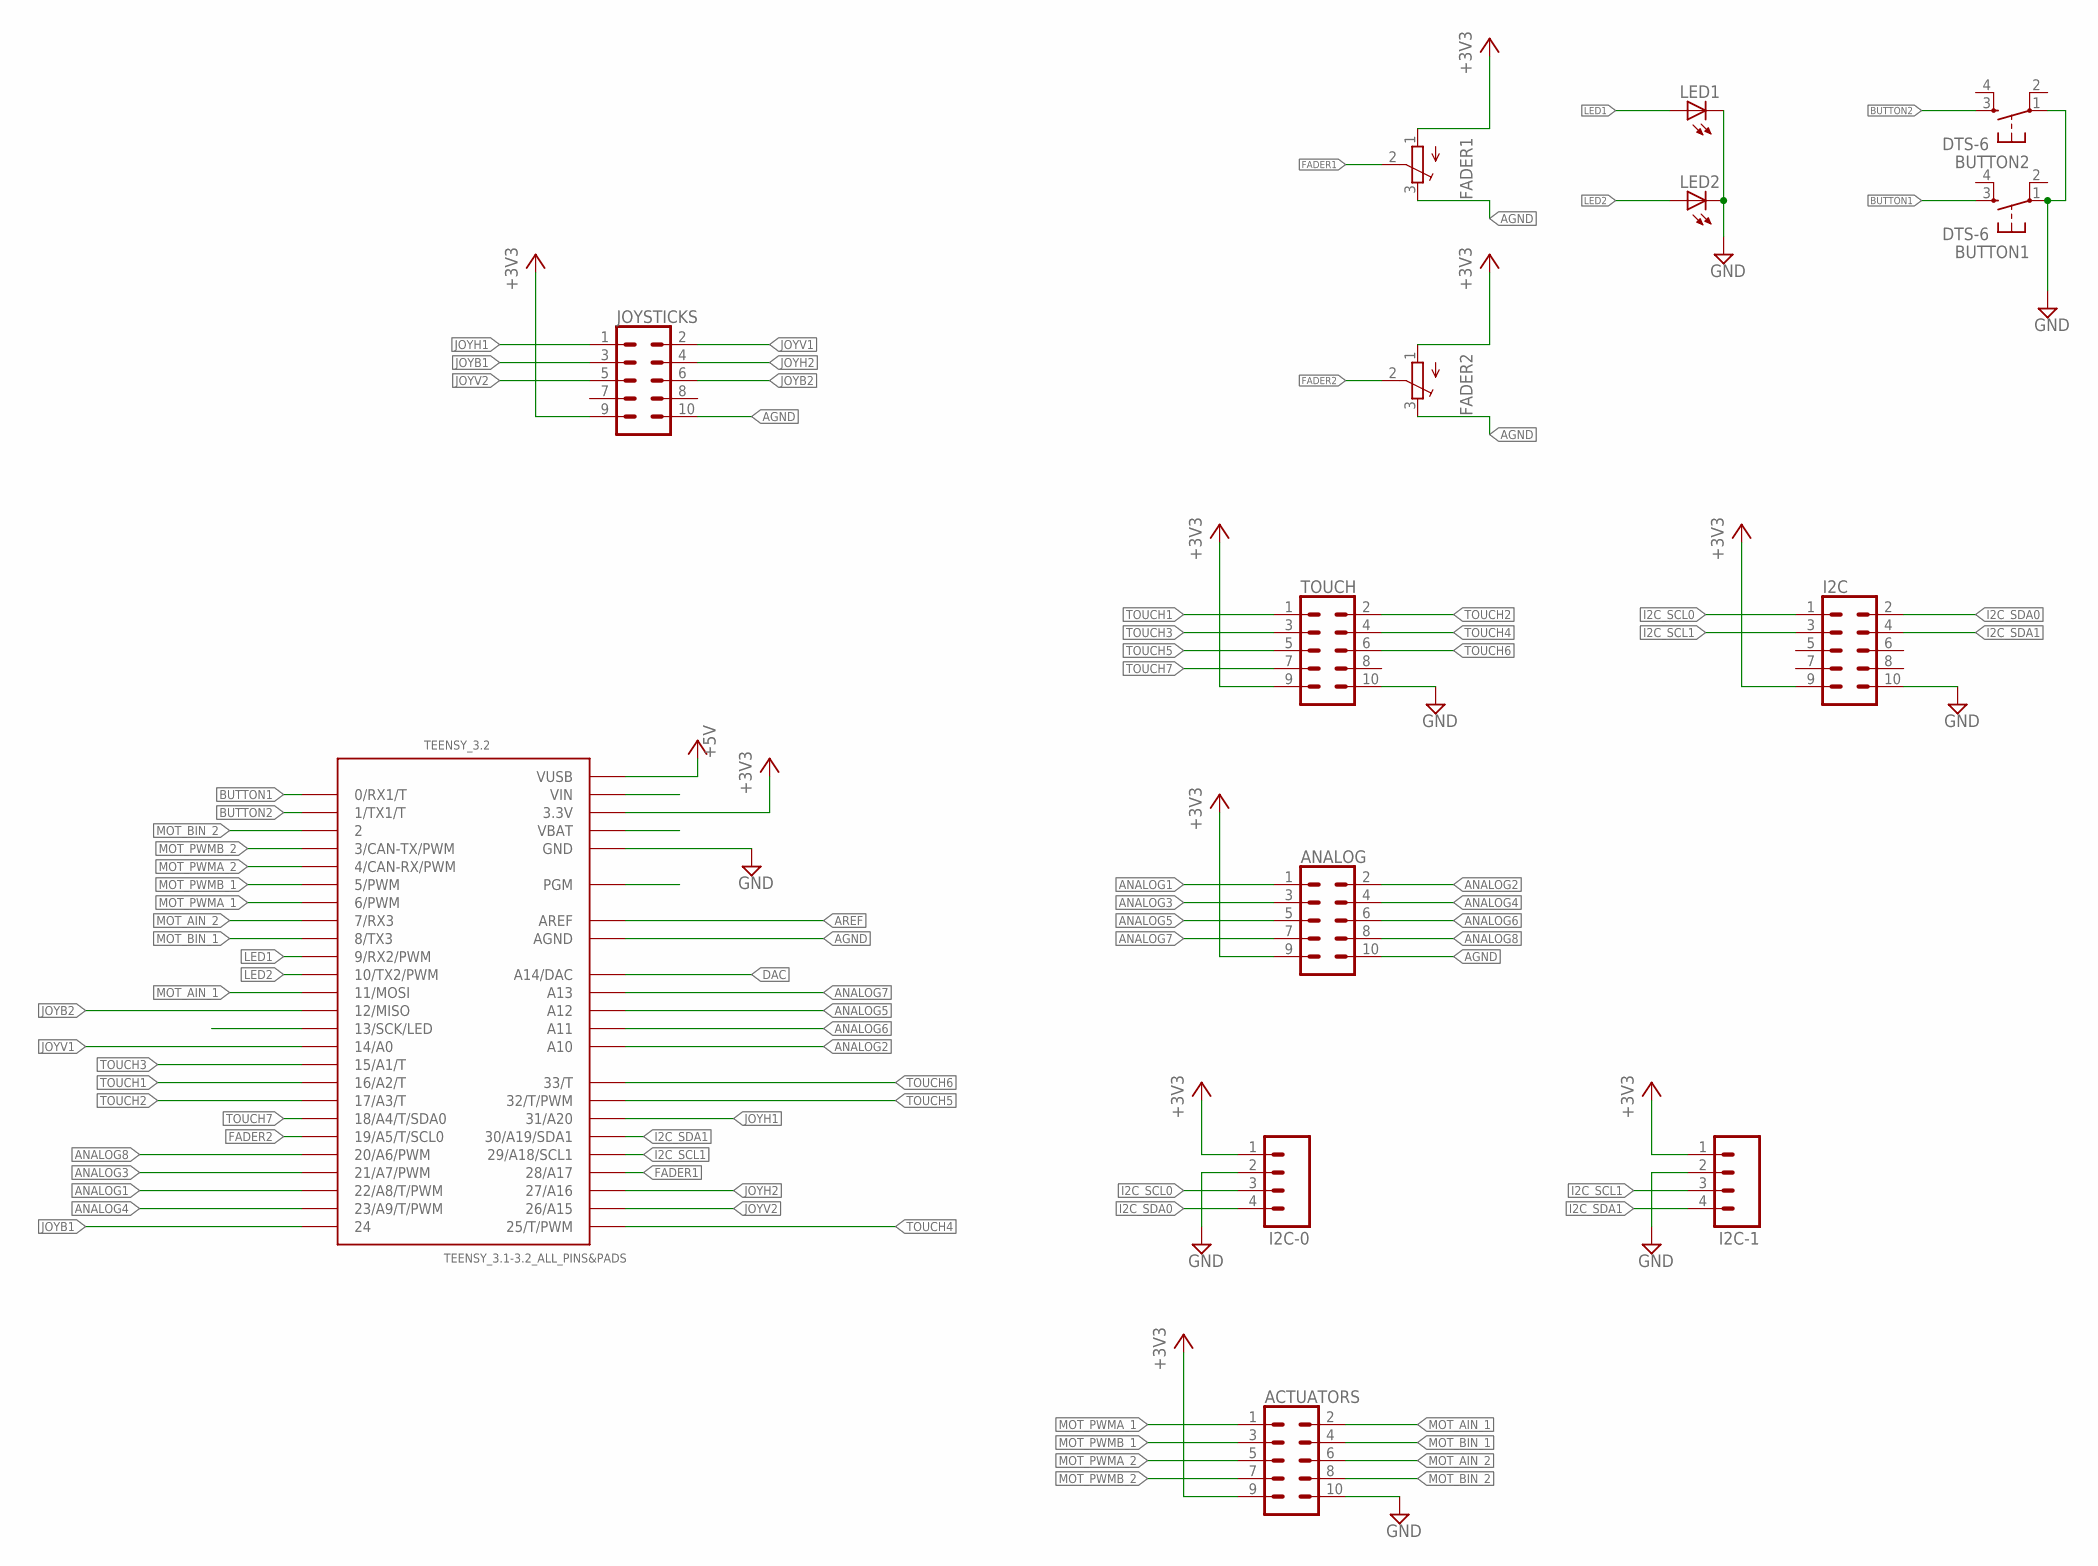
[picture p188: schematic MOM_teensy-breakout_v04.sch]

Parts:
ACTUATORS: CONN_05X2SHD_LOCK; 2X5-SHROUDED_LOCK
ANALOG: CONN_05X2SHD_LOCK; 2X5-SHROUDED_LOCK
BUTTON1, BUTTON2: DTS-6
FADER1, FADER2: TRIMPOT3386; TRIM-3386
I2C: CONN_05X2SHD_LOCK; 2X5-SHROUDED_LOCK
I2C-0, I2C-1: M04LOCK; 1X04_LOCK
JOYSTICKS: CONN_05X2SHD_LOCK; 2X5-SHROUDED_LOCK
LED1, LED2: LED3MM
TEENSY_3.2: TEENSY_3.1-3.2_ALL_PINS&PADS; TEENSY_3.0-3.2_ALL_PINS_&_PADS
TOUCH: CONN_05X2SHD_LOCK; 2X5-SHROUDED_LOCK

Connections:
+3V3: ACTUATORS.9, ANALOG.9, FADER1.1 (A), FADER2.1 (A), I2C.9, I2C-0.1, I2C-1.1, JOYSTICKS.9, TEENSY_3.2.3.3V, TEENSY_3.2.3.3V1 (3.3V), TEENSY_3.2.3.3V2 (3.3V), TOUCH.9
+5V: TEENSY_3.2.VUSB
AGND: ANALOG.10, FADER1.3 (E), FADER2.3 (E), JOYSTICKS.10, TEENSY_3.2.AGND
ANALOG1: ANALOG.1, TEENSY_3.2.22/A8 (22/A8/T/PWM)
ANALOG2: ANALOG.2, TEENSY_3.2.A10
ANALOG3: ANALOG.3, TEENSY_3.2.21/A7 (21/A7/PWM)
ANALOG4: ANALOG.4, TEENSY_3.2.23/A9 (23/A9/T/PWM)
ANALOG5: ANALOG.5, TEENSY_3.2.A12
ANALOG6: ANALOG.6, TEENSY_3.2.A11
ANALOG7: ANALOG.7, TEENSY_3.2.A13
ANALOG8: ANALOG.8, TEENSY_3.2.20/A6 (20/A6/PWM)
AREF: TEENSY_3.2.AREF
BUTTON1: BUTTON1.3, TEENSY_3.2.0 (0/RX1/T)
BUTTON2: BUTTON2.3, TEENSY_3.2.1 (1/TX1/T)
DAC: TEENSY_3.2.RESET/DAC (A14/DAC)
FADER1: FADER1.2 (S), TEENSY_3.2.28 (28/A17)
FADER2: FADER2.2 (S), TEENSY_3.2.19/A5 (19/A5/T/SCL0)
GND: ACTUATORS.10, BUTTON1.1, BUTTON2.1, I2C.10, I2C-0.2, I2C-1.2, LED1.K (C), LED2.K (C), TEENSY_3.2.GND, TEENSY_3.2.GND1 (GND), TEENSY_3.2.GND2 (GND), TOUCH.10
I2C_SCL0: I2C.1, I2C-0.3
I2C_SCL1: I2C.3, I2C-1.3, TEENSY_3.2.29 (29/A18/SCL1)
I2C_SDA0: I2C.2, I2C-0.4
I2C_SDA1: I2C.4, I2C-1.4, TEENSY_3.2.30 (30/A19/SDA1)
JOYB1: JOYSTICKS.3, TEENSY_3.2.24
JOYB2: JOYSTICKS.6, TEENSY_3.2.12 (12/MISO)
JOYH1: JOYSTICKS.1, TEENSY_3.2.31 (31/A20)
JOYH2: JOYSTICKS.4, TEENSY_3.2.27 (27/A16)
JOYV1: JOYSTICKS.2, TEENSY_3.2.14/A0
JOYV2: JOYSTICKS.5, TEENSY_3.2.26 (26/A15)
LED1: LED1.A, TEENSY_3.2.9 (9/RX2/PWM)
LED2: LED2.A, TEENSY_3.2.10 (10/TX2/PWM)
MOT_AIN_1: ACTUATORS.2, TEENSY_3.2.11 (11/MOSI)
MOT_AIN_2: ACTUATORS.6, TEENSY_3.2.7 (7/RX3)
MOT_BIN_1: ACTUATORS.4, TEENSY_3.2.8 (8/TX3)
MOT_BIN_2: ACTUATORS.8, TEENSY_3.2.2
MOT_PWMA_1: ACTUATORS.1, TEENSY_3.2.6 (6/PWM)
MOT_PWMA_2: ACTUATORS.5, TEENSY_3.2.4 (4/CAN-RX/PWM)
MOT_PWMB_1: ACTUATORS.3, TEENSY_3.2.5 (5/PWM)
MOT_PWMB_2: ACTUATORS.7, TEENSY_3.2.3 (3/CAN-TX/PWM)
TOUCH1: TEENSY_3.2.16/A2 (16/A2/T), TOUCH.1
TOUCH2: TEENSY_3.2.17/A3 (17/A3/T), TOUCH.2
TOUCH3: TEENSY_3.2.15/A1 (15/A1/T), TOUCH.3
TOUCH4: TEENSY_3.2.25 (25/T/PWM), TOUCH.4
TOUCH5: TEENSY_3.2.32 (32/T/PWM), TOUCH.5
TOUCH6: TEENSY_3.2.33 (33/T), TOUCH.6
TOUCH7: TEENSY_3.2.18/A4 (18/A4/T/SDA0), TOUCH.7

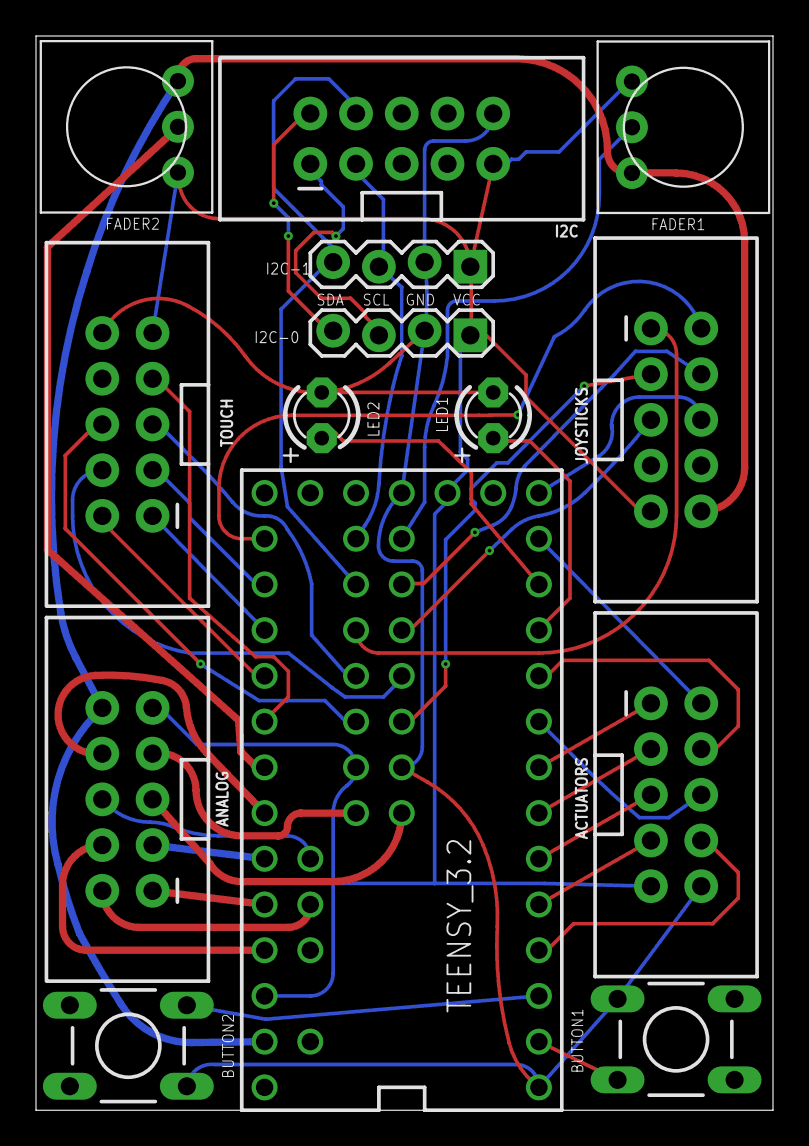
[picture p189: board MOM_teensy-breakout_v04.brd from above]

Board: 2 copper layers, 40.9 x 59.7 mm, 14 parts (0 on the bottom side), 42 nets.
